nevenfo/kicad-agentic-mcp/crates/konnect/src/ffi.rs

//! C ABI exports for KiCAD plugin integration.
//!
//! KiCAD (or the thin Python launcher) can load this cdylib and call:
//!   kicad_plugin_init(config_path)  — start the embedded MCP server thread
//!   kicad_plugin_version()          — return the version string
//!   kicad_plugin_shutdown()         — stop the server cleanly
//!
//! The MCP server runs in a background tokio thread; the calling process
//! communicates with it via the configured transport (STDIO or HTTP/SSE).

use std::ffi::{c_char, c_int, CStr, CString};
use std::sync::OnceLock;

static RUNTIME: OnceLock<tokio::runtime::Runtime> = OnceLock::new();
static VERSION_CSTR: OnceLock<CString> = OnceLock::new();

/// Initialize and start the embedded MCP server.
///
/// # Safety
/// `config_path` must be a valid null-terminated UTF-8 C string, or NULL to use defaults.
#[no_mangle]
pub unsafe extern "C" fn kicad_plugin_init(config_path: *const c_char) -> c_int {
    let config_path_str = if config_path.is_null() {
        None
    } else {
        match CStr::from_ptr(config_path).to_str() {
            Ok(s) => Some(s.to_owned()),
            Err(_) => return -1,
        }
    };

    let rt = match tokio::runtime::Runtime::new() {
        Ok(rt) => rt,
        Err(_) => return -1,
    };

    rt.spawn(async move {
        use crate::config::{Config, TransportMode};
        use konnect_core::mcp::handler::McpHandler;

        let mut config = match config_path_str.as_deref() {
            Some(p) => Config::load_from(std::path::Path::new(p)).unwrap_or_default(),
            None => Config::load().unwrap_or_default(),
        };
        // `load_from` does not apply the env fallbacks `load` does, and this
        // is the path KiCAD's own plugin loader takes (D.8). Without this,
        // `KONNECT_MODE=read-only` is silently ignored here and the plugin
        // starts writable — a guarantee that holds only on the binary's path
        // is the bug it is meant to prevent. Idempotent on the `load` branch:
        // every fallback either fills a blank or re-parses to the same value.
        // An unrecognised mode stops the server from starting at all, the
        // same shape as an invalid provider below: refusing to run is the
        // only safe reading of "I asked for read-only".
        if let Err(error) = config.apply_env_fallbacks() {
            tracing::error!("invalid server configuration: {error}");
            return;
        }
        let server_config = konnect_core::tools::ServerConfig {
            kicad_cli: config.kicad_cli.clone(),
            kicad_binary: config.kicad_binary.clone(),
            ipc_address: config.ipc_address.clone(),
            project_dir: config.project_dir.clone(),
            jlcpcb_db_path: config.jlcpcb_db_path.clone(),
            auto_load_toolsets: config.auto_load_toolsets,
            mode: config.mode,
        };
        let provider = match config.local_provider() {
            Ok(provider) => provider,
            Err(error) => {
                tracing::error!("invalid local Agent provider configuration: {error}");
                return;
            }
        };
        match McpHandler::new_with_agent_provider(server_config, provider).await {
            Ok(handler) => match config.transport {
                TransportMode::Stdio => {
                    let _ = crate::transport::stdio::run_stdio(handler).await;
                }
                TransportMode::Http => {
                    let _ = crate::transport::http::run_http(handler, &config.http_address).await;
                }
                TransportMode::Both => {
                    let handler_http = handler.clone();
                    let http_addr = config.http_address.clone();
                    tokio::select! {
                        _ = crate::transport::http::run_http(handler_http, &http_addr) => {},
                        _ = crate::transport::stdio::run_stdio(handler) => {},
                    }
                }
            },
            Err(e) => {
                eprintln!("kicad_plugin_init: failed to create handler: {}", e);
            }
        }
    });

    RUNTIME.set(rt).is_ok() as c_int
}

/// Return the plugin version string.
///
/// # Safety
/// The returned pointer is valid for the lifetime of the process.
#[no_mangle]
pub unsafe extern "C" fn kicad_plugin_version() -> *const c_char {
    VERSION_CSTR
        .get_or_init(|| CString::new(env!("CARGO_PKG_VERSION")).expect("version string is valid"))
        .as_ptr()
}

/// Shut down the embedded MCP server.
#[no_mangle]
pub extern "C" fn kicad_plugin_shutdown() {
    // The runtime will be dropped here; tokio tasks are cancelled automatically.
    // In a more complete implementation we would signal the server to flush and close.
    let _ = RUNTIME.get();
}
