nevenfo/kicad-agentic-mcp/crates/konnect-core/src/tools/library.rs

//! `library` toolset — create and manage footprints, symbols, and KiCAD library tables.
//!
//! Operations are file-based (S-expression manipulation + directory scanning).
//! No IPC or kicad-cli is required for most tools.

use crate::mcp::error::ToolErrorKind;
use crate::mcp::protocol::CallToolResult;
use crate::tool;
use crate::tools::{get_path, require_array, require_str, ToolContext, ToolDef};
use crate::try_arg;
use konnect_sexp::parser::{parse_sexp, SexpNode};
use konnect_sexp::writer::{find_balanced_block, find_block_starts, write_atomic};
use serde_json::json;
use std::path::{Path, PathBuf};

// ─── Tool definitions ─────────────────────────────────────────────────────────

/// The pin-item object schema (number/name/type/style/x/y/angle/length) shared
/// by `pins`, `units[].pins`, and `power_pins` in the create_symbol schema
/// below. `require_xy` is false where a `glyph` may auto-place the pins (so x/y
/// become optional) and true for the always-rectangular `power_pins`.
///
/// This object is emitted three times in one schema, so every word in it costs
/// three times as much catalogue budget as it looks like it does. The `type` and
/// `style` enums are self-documenting and carry no `description`; the one fact
/// they cannot express (NC is spelled `no_connect`) lives once in the tool
/// description instead of three times here. Measured: 219 -> 118 tokens per
/// copy, no field, value or default removed.
fn pin_item_schema(require_xy: bool) -> serde_json::Value {
    let mut required = vec!["number", "name", "type"];
    if require_xy {
        required.push("x");
        required.push("y");
    }
    json!({
        "type": "object",
        "properties": {
            "number": { "type": "string" },
            "name": { "type": "string" },
            "type": {
                "type": "string",
                "enum": ["input", "output", "bidirectional", "tri_state", "passive", "free", "unspecified", "power_in", "power_out", "open_collector", "open_emitter", "no_connect"]
            },
            "style": {
                "type": "string",
                "default": "line",
                "enum": ["line", "inverted", "clock", "inverted_clock", "input_low", "clock_low", "output_low", "edge_clock_high", "non_logic"]
            },
            "x": { "type": "number" },
            "y": { "type": "number" },
            "angle": { "type": "number", "default": 0 },
            "length": { "type": "number", "default": 2.54 }
        },
        "required": required
    })
}

pub fn tools() -> Vec<ToolDef> {
    vec![
        super::footprint_graphics::tool(),
        tool!(
            "create_footprint",
            "Create a new footprint (.kicad_mod) file from a pad layout description.",
            json!({
                "type": "object",
                "properties": {
                    "output": { "type": "string", "description": "Output .kicad_mod file path" },
                    "name": { "type": "string", "description": "Footprint name" },
                    "description": { "type": "string", "description": "Footprint description (optional)" },
                    "pads": {
                        "type": "array",
                        "description": "Pad definitions. Sizes in mm.",
                        "items": {
                            "type": "object",
                            "properties": {
                                "number": { "type": "string" },
                                "type": { "type": "string", "enum": ["smd", "thru_hole", "np_thru_hole", "connect"] },
                                "shape": { "type": "string", "enum": ["rect", "oval", "circle", "roundrect", "trapezoid", "custom"] },
                                "x": { "type": "number" },
                                "y": { "type": "number" },
                                "width": { "type": "number" },
                                "height": { "type": "number" },
                                "drill": { "type": "number", "description": "Drill diameter, thru-hole pads only" }
                            },
                            "required": ["number", "type", "shape", "x", "y", "width", "height"]
                        }
                    },
                    "body_width": { "type": "number", "description": "Component body width in mm. The courtyard, silkscreen and fab outlines are all derived from the body and pad envelopes together. Defaults to the pad envelope." },
                    "body_height": { "type": "number", "description": "Component body height in mm." },
                    "pin1_marker": { "type": "boolean", "default": true, "description": "Draw the pin-1 marker (silk dot + fab chamfer). Set false for a non-polarised part such as a fuse or a film capacitor, which has no pin 1 to point at." },
                    "package_type": {
                        "type": "string",
                        "enum": ["smd", "through_hole", "small", "bga"],
                        "description": "Courtyard clearance preset used when `courtyard_clearance` is absent: smd 0.25mm, through_hole 0.5mm, small 0.15mm (below 0603), bga 1.0mm."
                    },
                    "courtyard_clearance": { "type": "number", "description": "Courtyard clearance in mm; overrides `package_type`." },
                    "model": {
                        "type": "object",
                        "description": "3D model to attach.",
                        "properties": {
                            "path": { "type": "string", "description": "Path to a .step/.wrl file, absolute or KiCAD env-var form (${KICAD9_3DMODEL_DIR}/...)" },
                            "offset": { "type": "object", "description": "{x,y,z} mm, default 0,0,0" },
                            "scale": { "type": "object", "description": "{x,y,z}, default 1,1,1" },
                            "rotate": { "type": "object", "description": "{x,y,z} degrees, default 0,0,0" }
                        },
                        "required": ["path"]
                    }
                },
                "required": ["output", "name", "pads"]
            }),
            |args, ctx| async move { handle_create_footprint(args, ctx).await }
        ),
        tool!(
            "edit_footprint_pad",
            "Edit the size, shape, or position of a pad in an existing .kicad_mod footprint file.",
            json!({
                "type": "object",
                "properties": {
                    "footprint_path": { "type": "string", "description": "Path to .kicad_mod file" },
                    "pad_number": { "type": "string", "description": "Pad number to edit" },
                    "x": { "type": "number", "description": "New X position in mm (optional)" },
                    "y": { "type": "number", "description": "New Y position in mm (optional)" },
                    "width": { "type": "number", "description": "New pad width in mm (optional)" },
                    "height": { "type": "number", "description": "New pad height in mm (optional)" },
                    "shape": { "type": "string", "description": "New pad shape (optional)" },
                    "drill": { "type": "number", "description": "New drill diameter in mm (optional)" }
                },
                "required": ["footprint_path", "pad_number"]
            }),
            |args, ctx| async move { handle_edit_footprint_pad(args, ctx).await }
        ),
        tool!(
            "register_footprint_library",
            "Register a local footprint library directory in the KiCAD global or project library table.",
            json!({
                "type": "object",
                "properties": {
                    "library_path": { "type": "string", "description": "Path to .pretty directory" },
                    "nickname": { "type": "string", "description": "Library nickname" },
                    "scope": {
                        "type": "string",
                        "description": "Scope: 'global' or 'project'",
                        "default": "project"
                    },
                    "project": { "type": "string", "description": "Path to .kicad_pro file (required for project scope)" },
                    "replace_existing": {
                        "type": "boolean",
                        "description": "If the nickname is already registered with a different URI, correct that entry's URI in place, keeping its options and descr. Without it such a call is refused and nothing is written.",
                        "default": false
                    }
                },
                "required": ["library_path", "nickname"]
            }),
            |args, ctx| async move { handle_register_footprint_library(args, ctx).await }
        ),
        tool!(
            "list_footprint_libraries",
            "List all registered footprint libraries (global and optionally project-level).",
            json!({
                "type": "object",
                "properties": {
                    "project": { "type": "string", "description": "Path to .kicad_pro to include project libraries (optional)" },
                    "scope": {
                        "type": "string",
                        "description": "Scope: 'global', 'project', or 'all'",
                        "default": "all"
                    }
                },
                "required": []
            }),
            |args, ctx| async move { handle_list_footprint_libraries(args, ctx).await }
        ),
        tool!(
            "create_symbol",
            "Create a KiCAD schematic symbol and append it to a .kicad_sym library file. \
             Single-unit part: use `pins`. Multi-unit part (dual/quad op-amp, gate bank, \
             multi-bank connector): use `units`, plus `power_pins` for the rails they share. \
             A unit's body is a rectangle sized to its pins unless a `glyph` is set, in which \
             case the pins auto-place by `type` (inputs left, in the order listed, top-to- \
             bottom; output right; power top/bottom) and their x/y are ignored. NC pins take \
             type 'no_connect', not 'not_connected'.",
            json!({
                "type": "object",
                "properties": {
                    "library_path": { "type": "string", "description": "Path to .kicad_sym library file" },
                    "name": { "type": "string", "description": "Symbol name" },
                    "reference_prefix": { "type": "string", "description": "Default reference prefix (e.g. 'U')" },
                    "value": { "type": "string", "description": "Default value string" },
                    "glyph": {
                        "type": "string",
                        "default": "rectangle",
                        "enum": ["rectangle", "opamp", "buffer", "inverter", "schmitt", "schmitt_inverter", "and", "nand", "or", "nor", "xor", "xnor"],
                        "description": "Default body shape. 'rectangle' honours the pin x/y you supply; every other value draws a fixed conventional shape and auto-places the pins. Inverting glyphs (inverter/schmitt_inverter/nand/nor/xnor) draw their base body plus an inversion bubble on the output. A glyph whose pins do not fit it (wrong input count, not exactly one output) falls back to a rectangle and reports a warning."
                    },
                    "pins": {
                        "type": "array",
                        "description": "Pins of a single-unit symbol.",
                        "items": pin_item_schema(false)
                    },
                    "show_pin_names": { "type": "boolean", "description": "Show pin names (default true).", "default": true },
                    "show_pin_numbers": { "type": "boolean", "description": "Show pin numbers (default true).", "default": true },
                    "units": {
                        "type": "array",
                        "description": "One element per unit (Unit A, B, C...), each with its own pins and body. Replaces `pins`.",
                        "items": {
                            "type": "object",
                            "properties": {
                                "glyph": {
                                    "type": "string",
                                    "enum": ["rectangle", "opamp", "buffer", "inverter", "schmitt", "schmitt_inverter", "and", "nand", "or", "nor", "xor", "xnor"],
                                    "description": "Overrides the symbol-level `glyph` for this unit."
                                },
                                "pins": { "type": "array", "items": pin_item_schema(false) }
                            },
                            "required": ["pins"]
                        }
                    },
                    "power_pins": {
                        "type": "array",
                        "description": "Rails shared by every unit (V+/V-, VCC/GND). Only meaningful with `units`: they become one final rectangular power unit, following KiCAD's 74xx convention, instead of being drawn on every unit where each copy would need its own wiring to pass ERC.",
                        "items": pin_item_schema(true)
                    }
                },
                "required": ["library_path", "name", "reference_prefix"]
            }),
            |args, ctx| async move { handle_create_symbol(args, ctx).await }
        ),
        tool!(
            "delete_symbol",
            "Delete a symbol definition from a .kicad_sym library file.",
            json!({
                "type": "object",
                "properties": {
                    "library_path": { "type": "string", "description": "Path to .kicad_sym library file" },
                    "symbol_name": { "type": "string", "description": "Name of the symbol to delete" }
                },
                "required": ["library_path", "symbol_name"]
            }),
            |args, ctx| async move { handle_delete_symbol(args, ctx).await }
        ),
        tool!(
            "list_symbols_in_library",
            "List all symbol names defined in a .kicad_sym library file.",
            json!({
                "type": "object",
                "properties": {
                    "library_path": { "type": "string", "description": "Path to .kicad_sym library file" },
                    "limit": { "type": "integer", "description": "Maximum number of symbols to return", "default": 100 }
                },
                "required": ["library_path"]
            }),
            |args, ctx| async move { handle_list_symbols_in_library(args, ctx).await }
        ),
        tool!(
            "register_symbol_library",
            "Register a .kicad_sym library file in the KiCAD global or project symbol table.",
            json!({
                "type": "object",
                "properties": {
                    "library_path": { "type": "string", "description": "Path to .kicad_sym file" },
                    "nickname": { "type": "string", "description": "Library nickname" },
                    "scope": {
                        "type": "string",
                        "description": "Scope: 'global' or 'project'",
                        "default": "project"
                    },
                    "project": { "type": "string", "description": "Path to .kicad_pro file (required for project scope)" },
                    "replace_existing": {
                        "type": "boolean",
                        "description": "If the nickname is already registered with a different URI, correct that entry's URI in place, keeping its options and descr. Without it such a call is refused and nothing is written.",
                        "default": false
                    }
                },
                "required": ["library_path", "nickname"]
            }),
            |args, ctx| async move { handle_register_symbol_library(args, ctx).await }
        ),
        tool!(
            "list_symbol_libraries",
            "List all registered symbol libraries (global and optionally project-level).",
            json!({
                "type": "object",
                "properties": {
                    "project": { "type": "string", "description": "Path to .kicad_pro to include project libraries (optional)" },
                    "scope": {
                        "type": "string",
                        "description": "Scope: 'global', 'project', or 'all'",
                        "default": "all"
                    }
                },
                "required": []
            }),
            |args, ctx| async move { handle_list_symbol_libraries(args, ctx).await }
        ),
        tool!(
            "search_symbols",
            "Search for symbols across all registered libraries by name or keyword.",
            json!({
                "type": "object",
                "properties": {
                    "query": { "type": "string", "description": "Search string (partial name or keyword match)" },
                    "limit": { "type": "integer", "description": "Maximum number of results to return", "default": 50 },
                    "project_dir": { "type": "string", "description": "Project directory whose sym-lib-table is also searched. Defaults to the configured project_dir." }
                },
                "required": ["query"]
            }),
            |args, ctx| async move { handle_search_symbols(args, ctx).await }
        ),
        tool!(
            "list_library_footprints",
            "List all footprints in a specific registered footprint library (.pretty directory).",
            json!({
                "type": "object",
                "properties": {
                    "library_path": { "type": "string", "description": "Path to .pretty directory (or nickname to look up)" }
                },
                "required": ["library_path"]
            }),
            |args, ctx| async move { handle_list_library_footprints(args, ctx).await }
        ),
        tool!(
            "get_footprint_info",
            "Return detailed information about a footprint: pad layout, courtyard, description,              and its line/arc/rect/circle/poly graphics in the exact shape `set_footprint_graphics`              takes back.",
            json!({
                "type": "object",
                "properties": {
                    "footprint_path": { "type": "string", "description": "Path to .kicad_mod file, OR 'Library:Footprint' identifier" },
                    "graphics_layer": { "type": "string", "description": "Report only graphics on this canonical layer, such as F.CrtYd. Omit for all layers." }
                },
                "required": ["footprint_path"]
            }),
            |args, ctx| async move { handle_get_footprint_info(args, ctx).await }
        ),
        tool!(
            "search_footprints",
            "Search for footprints across all registered libraries by name or keyword.",
            json!({
                "type": "object",
                "properties": {
                    "query": { "type": "string", "description": "Search string (partial name or keyword)" },
                    "limit": { "type": "integer", "description": "Maximum number of results to return", "default": 50 }
                },
                "required": ["query"]
            }),
            |args, ctx| async move { handle_search_footprints(args, ctx).await }
        ),
        tool!(
            "get_symbol_info",
            "Return detailed information about a schematic symbol: pins, properties, description.",
            json!({
                "type": "object",
                "properties": {
                    "lib_id": { "type": "string", "description": "Library:Symbol identifier (e.g. 'Device:R')" },
                    "project_dir": { "type": "string", "description": "Project directory to resolve project-scoped libraries. Defaults to the configured project_dir." }
                },
                "required": ["lib_id"]
            }),
            |args, ctx| async move { handle_get_symbol_info(args, ctx).await }
        ),
    ]
}

// ─── Handlers ─────────────────────────────────────────────────────────────────

// ─── Footprint / symbol geometry (pure, unit-tested) ──────────────────────────

/// Minimal pad geometry needed to derive outlines, courtyards, and pin 1.
#[derive(Debug, Clone)]
struct PadGeom {
    number: String,
    pad_type: String,
    x: f64,
    y: f64,
    w: f64,
    h: f64,
}

/// Axis-aligned bounding box `(min_x, min_y, max_x, max_y)` over pad extents.
fn pads_bbox(pads: &[PadGeom]) -> (f64, f64, f64, f64) {
    let mut min_x = f64::INFINITY;
    let mut min_y = f64::INFINITY;
    let mut max_x = f64::NEG_INFINITY;
    let mut max_y = f64::NEG_INFINITY;
    for p in pads {
        min_x = min_x.min(p.x - p.w / 2.0);
        min_y = min_y.min(p.y - p.h / 2.0);
        max_x = max_x.max(p.x + p.w / 2.0);
        max_y = max_y.max(p.y + p.h / 2.0);
    }
    (min_x, min_y, max_x, max_y)
}

/// The body's own axis-aligned box, centred on the pad envelope — `None` when
/// the caller did not describe a body.
///
/// Centring on the pads rather than on the origin is what the fab outline
/// already did; keeping one definition means the courtyard and the fab outline
/// can never disagree about where the body is.
fn body_bbox(pads: &[PadGeom], body: Option<(f64, f64)>) -> Option<(f64, f64, f64, f64)> {
    let (bw, bh) = body?;
    let (pmin_x, pmin_y, pmax_x, pmax_y) = pads_bbox(pads);
    let cx = (pmin_x + pmax_x) / 2.0;
    let cy = (pmin_y + pmax_y) / 2.0;
    Some((cx - bw / 2.0, cy - bh / 2.0, cx + bw / 2.0, cy + bh / 2.0))
}

/// The union of two boxes.
fn union_bbox(a: (f64, f64, f64, f64), b: (f64, f64, f64, f64)) -> (f64, f64, f64, f64) {
    (a.0.min(b.0), a.1.min(b.1), a.2.max(b.2), a.3.max(b.3))
}

/// KLC's courtyard grid, as steps per millimetre: `KLC_CRTYD_GRID = 0.01` mm,
/// from `pcb/rules/klc_constants.py` in KiCad's own `kicad-library-utils`.
///
/// Held as the reciprocal because that is what makes the arithmetic exact.
/// `(-3.8 / 0.01).floor() * 0.01` is -3.8000000000000003 — one ULP out, and a
/// value that was already on the grid comes back off it. `-380.0 / 100.0` is
/// -3.8 exactly.
const COURTYARD_GRID_STEPS_PER_MM: f64 = 100.0;

/// Snap a courtyard box to the KLC grid, always **outward**.
///
/// KiCad's own checker snaps to nearest (`mapToGrid` in `pcb/rules/F5_3.py`).
/// Rounding outward instead is the one deliberate difference: rounding a bound
/// inward would take back up to half a grid step of the clearance that was just
/// added, and a courtyard 5 µm too small is the failure this whole change exists
/// to stop. Growing by at most 5 µm costs nothing.
fn snap_courtyard_outward(bbox: (f64, f64, f64, f64)) -> (f64, f64, f64, f64) {
    // The epsilon absorbs binary-float noise, so a bound that is already on the
    // grid is not pushed a whole step out by a representation error.
    let epsilon = 1e-9;
    let down =
        |v: f64| (v * COURTYARD_GRID_STEPS_PER_MM + epsilon).floor() / COURTYARD_GRID_STEPS_PER_MM;
    let up =
        |v: f64| (v * COURTYARD_GRID_STEPS_PER_MM - epsilon).ceil() / COURTYARD_GRID_STEPS_PER_MM;
    (down(bbox.0), down(bbox.1), up(bbox.2), up(bbox.3))
}

/// The courtyard box: the combined pad and body envelope, grown by `clearance`
/// and snapped outward to the KLC grid.
///
/// # The defect this replaces
///
/// The courtyard used to be the *pad* envelope plus clearance, with the body
/// used only for the fab outline. Every part whose body overruns its land
/// pattern therefore got a courtyard smaller than the part — and a courtyard
/// smaller than the part is worse than none, because DRC then reports clearance
/// as satisfied while the physical bodies collide. Found on a real board: a
/// 5 mm-pitch film capacitor, body 3.5 mm deep, pads 1.6 mm, courtyard 2.6 mm.
///
/// # The rule
///
/// KLC F5.3 defines the courtyard as the smallest rectangle giving the required
/// clearance around the **combined component body and land pattern**. KiCad's
/// own conformance checker implements exactly that: `getFootprintBounds()` in
/// `pcb/rules/F5_3.py` adds the pad bounds to the geometric bounds of F.Fab
/// (falling back to B.Fab, then the silkscreen), then `defaultCourtyard()`
/// expands by the offset and snaps to `KLC_CRTYD_GRID`.
fn courtyard_bbox(
    pads: &[PadGeom],
    body: Option<(f64, f64)>,
    clearance: f64,
) -> (f64, f64, f64, f64) {
    let envelope = match body_bbox(pads, body) {
        Some(body) => union_bbox(pads_bbox(pads), body),
        None => pads_bbox(pads),
    };
    snap_courtyard_outward((
        envelope.0 - clearance,
        envelope.1 - clearance,
        envelope.2 + clearance,
        envelope.3 + clearance,
    ))
}

/// Courtyard clearance per the contributor's rule: an explicit value wins, else
/// `package_type`, else auto-detect (through-hole 0.5 mm, sub-0603 body 0.15 mm,
/// otherwise SMT 0.25 mm). BGA (1.0 mm) is opt-in via `package_type` because an
/// area array can't be reliably auto-detected from pads alone.
fn courtyard_clearance(
    explicit: Option<f64>,
    package_type: Option<&str>,
    pads: &[PadGeom],
    body: Option<(f64, f64)>,
) -> f64 {
    if let Some(c) = explicit {
        return c;
    }
    match package_type {
        Some("bga") => return 1.0,
        Some("small") => return 0.15,
        Some("through_hole") | Some("th") => return 0.5,
        Some("smd") => return 0.25,
        _ => {}
    }
    if pads.iter().any(|p| p.pad_type.contains("thru")) {
        return 0.5;
    }
    if let Some((bw, bh)) = body {
        // 0603 imperial body is 1.6 x 0.8 mm; anything shorter is "smaller".
        if bw.max(bh) < 1.6 {
            return 0.15;
        }
    }
    0.25
}

/// Index of pin 1: the pad numbered "1", else the first pad. `None` if no pads.
fn pin1_index(pads: &[PadGeom]) -> Option<usize> {
    if pads.is_empty() {
        return None;
    }
    Some(pads.iter().position(|p| p.number == "1").unwrap_or(0))
}

/// The rectangle corner (of the four) nearest point `(px, py)`.
fn nearest_corner(min_x: f64, min_y: f64, max_x: f64, max_y: f64, px: f64, py: f64) -> (f64, f64) {
    let cx = if (px - min_x).abs() <= (max_x - px).abs() {
        min_x
    } else {
        max_x
    };
    let cy = if (py - min_y).abs() <= (max_y - py).abs() {
        min_y
    } else {
        max_y
    };
    (cx, cy)
}

/// Radius of the pin-1 silk dot, in mm.
const PIN1_DOT_RADIUS_MM: f64 = 0.15;

/// Where the pin-1 dot's centre goes along one axis: just outside the silk
/// outline, but never so far that any part of the dot leaves the courtyard.
///
/// `sign` is the outward direction, -1 for a min edge and +1 for a max edge.
///
/// The unclamped version put a dot at x = -9.3 on a footprint whose courtyard
/// stopped at -9.0. Drawing a footprint's own marker outside its own courtyard
/// is a contradiction: the courtyard is the claim about how much room the part
/// needs, and a mark beyond it says the claim is short. Clamping to
/// `courtyard_edge - sign * radius` puts the dot flush against the inside of
/// the courtyard in the worst case, which is still unmistakably beside pin 1.
fn pin1_dot_center(silk_edge: f64, courtyard_edge: f64, sign: f64) -> f64 {
    let desired = silk_edge + sign * 0.4;
    let limit = courtyard_edge - sign * PIN1_DOT_RADIUS_MM;
    if sign < 0.0 {
        desired.max(limit)
    } else {
        desired.min(limit)
    }
}

fn point_toward(from: (f64, f64), toward: (f64, f64), d: f64) -> (f64, f64) {
    let dx = toward.0 - from.0;
    let dy = toward.1 - from.1;
    let len = (dx * dx + dy * dy).sqrt();
    if len < 1e-9 {
        return from;
    }
    (from.0 + dx / len * d, from.1 + dy / len * d)
}

/// Ordered vertices of a rectangle outline whose corner nearest `(px, py)` is
/// chamfered by `chamfer` mm (clamped to 40% of the shorter side) — the F.Fab
/// pin-1 marker. Clockwise, KiCAD footprint Y-down.
fn chamfered_rect_points(
    min_x: f64,
    min_y: f64,
    max_x: f64,
    max_y: f64,
    px: f64,
    py: f64,
    chamfer: f64,
) -> Vec<(f64, f64)> {
    let ch = chamfer
        .min(0.4 * (max_x - min_x).min(max_y - min_y))
        .max(0.0);
    let corners = [
        (min_x, min_y),
        (max_x, min_y),
        (max_x, max_y),
        (min_x, max_y),
    ];
    let (tcx, tcy) = nearest_corner(min_x, min_y, max_x, max_y, px, py);
    let mut pts = Vec::new();
    for (i, &(cx, cy)) in corners.iter().enumerate() {
        if (cx - tcx).abs() < 1e-9 && (cy - tcy).abs() < 1e-9 && ch > 0.0 {
            let prev = corners[(i + 3) % 4];
            let next = corners[(i + 1) % 4];
            pts.push(point_toward((cx, cy), prev, ch));
            pts.push(point_toward((cx, cy), next, ch));
        } else {
            pts.push((cx, cy));
        }
    }
    pts
}

/// Emit the `(model ...)` block when a `model` object with a non-empty `path`
/// is present. Path is passed through verbatim (absolute or KiCAD env-var).
fn build_model_sexp(args: &serde_json::Value) -> String {
    let model = match args.get("model") {
        Some(m) if m.is_object() => m,
        _ => return String::new(),
    };
    let path = match model["path"].as_str() {
        Some(p) if !p.is_empty() => p,
        _ => return String::new(),
    };
    let xyz = |key: &str, default: f64| -> (f64, f64, f64) {
        let o = &model[key];
        (
            o["x"].as_f64().unwrap_or(default),
            o["y"].as_f64().unwrap_or(default),
            o["z"].as_f64().unwrap_or(default),
        )
    };
    let (ox, oy, oz) = xyz("offset", 0.0);
    let (sx, sy, sz) = xyz("scale", 1.0);
    let (rx, ry, rz) = xyz("rotate", 0.0);
    format!(
        "\n  (model \"{}\"\n    (offset (xyz {} {} {}))\n    (scale (xyz {} {} {}))\n    (rotate (xyz {} {} {}))\n  )",
        path, ox, oy, oz, sx, sy, sz, rx, ry, rz
    )
}

/// Build the courtyard, silkscreen, fab outline, reference/value text, and the
/// pin-1 marker (silk dot + fab chamfer) for a footprint from its pad geometry.
fn build_footprint_graphics(args: &serde_json::Value, name: &str, pads: &[PadGeom]) -> String {
    let (pmin_x, pmin_y, pmax_x, pmax_y) = pads_bbox(pads);

    let body = match (args["body_width"].as_f64(), args["body_height"].as_f64()) {
        (Some(bw), Some(bh)) => Some((bw, bh)),
        _ => None,
    };
    let clearance = courtyard_clearance(
        args["courtyard_clearance"].as_f64(),
        args["package_type"].as_str(),
        pads,
        body,
    );

    // Courtyard: the *combined* pad and body envelope plus clearance, per KLC
    // F5.3 — see `courtyard_bbox` for why the pad envelope alone was wrong.
    let (cmin_x, cmin_y, cmax_x, cmax_y) = courtyard_bbox(pads, body, clearance);

    // Fab: the component body when given, else the pad envelope. May overlap
    // pads — fab is a documentation layer, not subject to silk-over-pad rules.
    let (fmin_x, fmin_y, fmax_x, fmax_y) =
        body_bbox(pads, body).unwrap_or((pmin_x, pmin_y, pmax_x, pmax_y));

    // Silk: outside the same combined envelope, so it clears the pads (no
    // silk-over-pad violation) *and* actually outlines the part. Deriving it
    // from the pad envelope alone drew a 1.9 mm box around a 3.5 mm body on the
    // footprint that exposed the courtyard defect — three layers each claiming
    // a different body size.
    let silk_margin = 0.15;
    let (emin_x, emin_y, emax_x, emax_y) = match body_bbox(pads, body) {
        Some(body) => union_bbox((pmin_x, pmin_y, pmax_x, pmax_y), body),
        None => (pmin_x, pmin_y, pmax_x, pmax_y),
    };
    let (smin_x, smin_y, smax_x, smax_y) = (
        emin_x - silk_margin,
        emin_y - silk_margin,
        emax_x + silk_margin,
        emax_y + silk_margin,
    );

    let mut s = String::new();

    // Courtyard rectangle (F.CrtYd) — required for DRC.
    s.push_str(&format!(
        "\n  (fp_rect (start {:.4} {:.4}) (end {:.4} {:.4}) (stroke (width 0.05) (type solid)) (fill none) (layer \"F.CrtYd\"))",
        cmin_x, cmin_y, cmax_x, cmax_y
    ));
    // Silkscreen outline (F.SilkS).
    s.push_str(&format!(
        "\n  (fp_rect (start {:.4} {:.4}) (end {:.4} {:.4}) (stroke (width 0.12) (type solid)) (fill none) (layer \"F.SilkS\"))",
        smin_x, smin_y, smax_x, smax_y
    ));

    // A pin-1 mark is right for a polarised part and wrong for one that has no
    // pin 1 to find: a fuse, a resistor, a non-polarised capacitor. Nothing in
    // a pad list distinguishes the two — a fuse's pads are numbered "1" and "2"
    // exactly like a diode's — so this is a caller's statement, not a guess.
    // Default true, because the parts that need the mark are the ones where
    // omitting it is a build error.
    let want_pin1 = args["pin1_marker"].as_bool().unwrap_or(true);

    if let Some(i1) = pin1_index(pads).filter(|_| want_pin1) {
        let p1 = &pads[i1];

        // Fab outline with the pin-1 corner chamfered.
        let chamfer = (0.25 * (fmax_x - fmin_x).min(fmax_y - fmin_y)).clamp(0.3, 1.0);
        let pts = chamfered_rect_points(fmin_x, fmin_y, fmax_x, fmax_y, p1.x, p1.y, chamfer);
        let pts_str: String = pts
            .iter()
            .map(|(x, y)| format!("(xy {:.4} {:.4}) ", x, y))
            .collect();
        s.push_str(&format!(
            "\n  (fp_poly (pts {}) (stroke (width 0.1) (type solid)) (fill none) (layer \"F.Fab\"))",
            pts_str.trim()
        ));

        // Silk pin-1 dot just outside the silk outline, aligned with pin 1's
        // pad — NOT at the footprint corner, where a dot is ambiguous between
        // pin 1 and the last pin that shares the same corner. It sits directly
        // beside pin 1 so the mark is unmistakable.
        let bcx = (pmin_x + pmax_x) / 2.0;
        let bcy = (pmin_y + pmax_y) / 2.0;
        let (dx, dy) = if (p1.x - bcx).abs() >= (p1.y - bcy).abs() {
            // Pin 1 is on a left/right edge: dot outside that edge, at pin 1's y.
            let sign = if p1.x < bcx { -1.0 } else { 1.0 };
            let silk_edge = if sign < 0.0 { smin_x } else { smax_x };
            let courtyard_edge = if sign < 0.0 { cmin_x } else { cmax_x };
            (pin1_dot_center(silk_edge, courtyard_edge, sign), p1.y)
        } else {
            // Pin 1 is on a top/bottom edge: dot outside that edge, at pin 1's x.
            let sign = if p1.y < bcy { -1.0 } else { 1.0 };
            let silk_edge = if sign < 0.0 { smin_y } else { smax_y };
            let courtyard_edge = if sign < 0.0 { cmin_y } else { cmax_y };
            (p1.x, pin1_dot_center(silk_edge, courtyard_edge, sign))
        };
        s.push_str(&format!(
            "\n  (fp_circle (center {:.4} {:.4}) (end {:.4} {:.4}) (stroke (width 0.1) (type solid)) (fill solid) (layer \"F.SilkS\"))",
            dx, dy, dx + PIN1_DOT_RADIUS_MM, dy
        ));
    } else {
        // No pads to mark pin 1 against — plain fab rectangle.
        s.push_str(&format!(
            "\n  (fp_rect (start {:.4} {:.4}) (end {:.4} {:.4}) (stroke (width 0.1) (type solid)) (fill none) (layer \"F.Fab\"))",
            fmin_x, fmin_y, fmax_x, fmax_y
        ));
    }

    // Reference (F.SilkS, above) and value (F.Fab, below).
    let cx = (pmin_x + pmax_x) / 2.0;
    s.push_str(&format!(
        "\n  (fp_text reference \"REF**\" (at {:.4} {:.4} 0) (layer \"F.SilkS\") (effects (font (size 1 1) (thickness 0.15))))",
        cx, cmin_y - 1.0
    ));
    s.push_str(&format!(
        "\n  (fp_text value \"{}\" (at {:.4} {:.4} 0) (layer \"F.Fab\") (effects (font (size 1 1) (thickness 0.15))))",
        name, cx, cmax_y + 1.0
    ));

    s
}

async fn handle_create_footprint(
    args: &serde_json::Value,
    _ctx: &ToolContext,
) -> anyhow::Result<CallToolResult> {
    let output = get_path(args, "output")?;
    let name = try_arg!(require_str(args, "name"));
    let description = args["description"].as_str().unwrap_or("");

    // `name` and `pads` are `required` in the schema. Defaulting them wrote a
    // footprint called "Footprint" with no pads over whatever `output` already
    // held — a destructive write standing in for the call the caller meant.
    let pads_val = try_arg!(require_array(args, "pads"));
    let mut pad_geoms: Vec<PadGeom> = Vec::new();
    let mut pad_sexp = String::new();
    for pad in pads_val {
        let number = pad["number"].as_str().unwrap_or("1").to_string();
        let pad_type = pad["type"].as_str().unwrap_or("smd").to_string();
        let shape = pad["shape"].as_str().unwrap_or("rect");
        let x = pad["x"].as_f64().unwrap_or(0.0);
        let y = pad["y"].as_f64().unwrap_or(0.0);
        let w = pad["width"].as_f64().unwrap_or(1.0);
        let h = pad["height"].as_f64().unwrap_or(1.0);

        let layers = if pad_type == "smd" {
            r#"(layers "F.Cu" "F.Paste" "F.Mask")"#
        } else {
            r#"(layers "*.Cu" "*.Mask")"#
        };

        let drill_sexp = if let Some(drill) = pad["drill"].as_f64() {
            format!("(drill {})", drill)
        } else {
            String::new()
        };

        pad_sexp.push_str(&format!(
            "\n  (pad \"{}\" {} {} (at {} {}) (size {} {}) {} {})",
            number, pad_type, shape, x, y, w, h, layers, drill_sexp
        ));
        pad_geoms.push(PadGeom {
            number,
            pad_type,
            x,
            y,
            w,
            h,
        });
    }

    // Courtyard, silk, fab, text, and pin-1 marker, derived from pad geometry.
    let graphics = if pad_geoms.is_empty() {
        String::new()
    } else {
        build_footprint_graphics(args, name, &pad_geoms)
    };
    let model_sexp = build_model_sexp(args);

    let attr = if pad_geoms.iter().any(|p| p.pad_type == "smd") {
        "smd"
    } else {
        "through_hole"
    };

    let content = format!(
        "(footprint \"{}\"\n  (version 20240108)\n  (generator \"konnect\")\n  (layer \"F.Cu\")\n  (descr \"{}\")\n  (attr {}){}{}{}\n)",
        name, description, attr, pad_sexp, graphics, model_sexp
    );

    // Ensure parent directory exists
    if let Some(parent) = output.parent() {
        tokio::fs::create_dir_all(parent).await?;
    }
    write_atomic(&output, &content)?;

    Ok(CallToolResult::text(
        serde_json::to_string(&json!({
            "success": true,
            "footprint": name,
            "output": output.to_str().unwrap_or(""),
            "pad_count": pad_geoms.len(),
            "courtyard": !pad_geoms.is_empty(),
            "pin1_marked": !pad_geoms.is_empty() && args["pin1_marker"].as_bool().unwrap_or(true),
            "model": args.get("model").and_then(|m| m["path"].as_str()).unwrap_or("")
        }))
        .unwrap(),
    ))
}

async fn handle_edit_footprint_pad(
    args: &serde_json::Value,
    _ctx: &ToolContext,
) -> anyhow::Result<CallToolResult> {
    let path = get_path(args, "footprint_path")?;
    let pad_number = try_arg!(require_str(args, "pad_number"));

    let content = tokio::fs::read_to_string(&path).await?;

    // Find the pad block:  (pad "N" ... (at X Y) (size W H) ...)
    // We search for the at/size/drill atoms and replace them individually.
    let pad_pat = format!(r#"(pad "{}""#, pad_number);
    let pad_start = content
        .find(&pad_pat)
        .ok_or_else(|| anyhow::anyhow!("Pad '{}' not found in footprint", pad_number))?;

    // Find the closing paren of this pad block (simple depth count)
    let pad_end = {
        let mut depth = 0i32;
        let mut end = pad_start;
        for (i, ch) in content[pad_start..].char_indices() {
            match ch {
                '(' => depth += 1,
                ')' => {
                    depth -= 1;
                    if depth == 0 {
                        end = pad_start + i + 1;
                        break;
                    }
                }
                _ => {}
            }
        }
        end
    };
    let pad_block = &content[pad_start..pad_end];

    // Helper: replace or add a sub-expression within the pad block
    let mut new_pad = pad_block.to_string();

    if let Some(x) = args["x"].as_f64() {
        // Replace (at OLD_X OLD_Y [ROT]) → update X
        if let Some(at_pos) = new_pad.find("(at ") {
            let at_end = new_pad[at_pos..]
                .find(')')
                .map(|i| at_pos + i + 1)
                .unwrap_or(new_pad.len());
            let at_block = &new_pad[at_pos..at_end];
            // Parse existing values
            let parts: Vec<&str> = at_block
                .trim_start_matches("(at ")
                .trim_end_matches(')')
                .split_whitespace()
                .collect();
            let old_y = parts
                .get(1)
                .and_then(|s| s.parse::<f64>().ok())
                .unwrap_or(0.0);
            let rot = parts.get(2).map(|s| format!(" {}", s)).unwrap_or_default();
            let new_at = format!("(at {} {}{})", x, old_y, rot);
            new_pad.replace_range(at_pos..at_end, &new_at);
        }
    }
    if let Some(y) = args["y"].as_f64() {
        if let Some(at_pos) = new_pad.find("(at ") {
            let at_end = new_pad[at_pos..]
                .find(')')
                .map(|i| at_pos + i + 1)
                .unwrap_or(new_pad.len());
            let at_block = &new_pad[at_pos..at_end];
            let parts: Vec<&str> = at_block
                .trim_start_matches("(at ")
                .trim_end_matches(')')
                .split_whitespace()
                .collect();
            let old_x = parts
                .first()
                .and_then(|s| s.parse::<f64>().ok())
                .unwrap_or(0.0);
            let rot = parts.get(2).map(|s| format!(" {}", s)).unwrap_or_default();
            let new_at = format!("(at {} {}{})", old_x, y, rot);
            new_pad.replace_range(at_pos..at_end, &new_at);
        }
    }
    if let (Some(w), Some(h)) = (args["width"].as_f64(), args["height"].as_f64()) {
        if let Some(sz_pos) = new_pad.find("(size ") {
            let sz_end = new_pad[sz_pos..]
                .find(')')
                .map(|i| sz_pos + i + 1)
                .unwrap_or(new_pad.len());
            let new_size = format!("(size {} {})", w, h);
            new_pad.replace_range(sz_pos..sz_end, &new_size);
        }
    }
    if let Some(drill) = args["drill"].as_f64() {
        if let Some(dr_pos) = new_pad.find("(drill ") {
            let dr_end = new_pad[dr_pos..]
                .find(')')
                .map(|i| dr_pos + i + 1)
                .unwrap_or(new_pad.len());
            let new_drill = format!("(drill {})", drill);
            new_pad.replace_range(dr_pos..dr_end, &new_drill);
        } else {
            // Insert drill before closing paren of pad
            let insert_at = new_pad.rfind(')').unwrap_or(new_pad.len());
            new_pad.insert_str(insert_at, &format!(" (drill {})", drill));
        }
    }

    // Apply the pad block replacement
    let new_content = format!(
        "{}{}{}",
        &content[..pad_start],
        new_pad,
        &content[pad_end..]
    );
    write_atomic(&path, &new_content)?;

    Ok(CallToolResult::text(
        serde_json::to_string(&json!({
            "success": true,
            "pad": pad_number
        }))
        .unwrap(),
    ))
}

// ─── Library table helpers ────────────────────────────────────────────────────

/// Returns the path to the global fp-lib-table file.
fn global_fp_lib_table() -> PathBuf {
    super::kicad_config_dir().join("fp-lib-table")
}

/// Returns the path to the global sym-lib-table file.
fn global_sym_lib_table() -> PathBuf {
    super::kicad_config_dir().join("sym-lib-table")
}

/// Parse a lib-table S-expression and return list of (nickname, uri, type) tuples.
///
/// Indentation-agnostic: KiCad's own writers emit tab-indented, CRLF-terminated
/// tables while this crate's writer uses two spaces, so a fixed literal such as
/// `"\n  (lib "` silently matches nothing in a real `fp-lib-table`.
fn parse_lib_table(content: &str) -> Vec<serde_json::Value> {
    let mut libs = Vec::new();
    // Each entry: (lib (name "NICK") (type "...") (uri "...") (options "") (descr "..."))
    for start in find_block_starts(content, "lib") {
        let Some((block_start, block_end)) = find_balanced_block(content, start) else {
            continue;
        };
        let block = &content[block_start..block_end];

        let nickname = extract_sexp_string(block, "name").unwrap_or_default();
        let uri = extract_sexp_string(block, "uri").unwrap_or_default();
        let lib_type = extract_sexp_string(block, "type").unwrap_or_default();
        let descr = extract_sexp_string(block, "descr").unwrap_or_default();

        libs.push(json!({
            "nickname": nickname,
            "uri": uri,
            "type": lib_type,
            "description": descr
        }));
    }
    libs
}

/// Resolve a lib-table URI to a concrete path, expanding a leading
/// `${KICAD*_DIR}` reference.
///
/// KiCad's shipped tables address bundled libraries as
/// `${KICAD10_FOOTPRINT_DIR}/Resistor_SMD.pretty`. An exported environment
/// variable wins; otherwise the variable's kind is inferred from its name and
/// the known install locations are searched.
fn expand_lib_uri(uri: &str, kiprjmod: Option<&Path>) -> Option<PathBuf> {
    let Some(rest) = uri.strip_prefix("${") else {
        return (!uri.is_empty()).then(|| PathBuf::from(uri));
    };
    let close = rest.find('}')?;
    let var = &rest[..close];
    let tail = rest[close + 1..].trim_start_matches(['/', '\\']);

    // ${KIPRJMOD} is the project directory — resolved from the table's own
    // location, not the environment: KiCad sets it per open project at
    // runtime, so an exported value (if any) may belong to a different
    // project than the table being read. Project-scoped registrations are
    // the default for register_footprint_library, so this is the common
    // case for user-registered libraries, not an edge.
    if var == "KIPRJMOD" {
        let p = kiprjmod?.join(tail);
        return p.exists().then_some(p);
    }

    // var_os, not var: `var` treats a non-Unicode value as absent, which would
    // send a perfectly good ${KICAD*_DIR} down the install-root guess path.
    if let Some(base) = std::env::var_os(var) {
        let p = PathBuf::from(base).join(tail);
        if p.exists() {
            return Some(p);
        }
    }

    // e.g. KICAD10_FOOTPRINT_DIR -> "footprints"
    let kind = if var.ends_with("_FOOTPRINT_DIR") {
        "footprints"
    } else if var.ends_with("_SYMBOL_DIR") {
        "symbols"
    } else if var.ends_with("_3DMODEL_DIR") {
        "3dmodels"
    } else {
        return None;
    };

    super::find_kicad_library_dirs(kind)
        .into_iter()
        .map(|base| base.join(tail))
        .find(|p| p.exists())
}

/// Maximum depth when following nested `(type "Table")` lib-table references.
const MAX_LIB_TABLE_DEPTH: usize = 4;

/// Parse a lib-table and return concrete libraries, following nested tables.
///
/// KiCad 10 no longer copies its ~155 bundled libraries into the user's table.
/// The default global table instead holds a single indirection entry —
/// `(lib (name "KiCad") (type "Table") (uri ".../template/fp-lib-table"))` —
/// pointing at the shipped template table. Treating that entry as a library
/// makes every bundled library invisible, so it is followed here.
///
/// Each returned entry carries the original `uri` plus a resolved `path`
/// whenever [`expand_lib_uri`] yields one: a `${KICAD*_DIR}` URI resolves only
/// if the expansion exists on disk, while a plain URI is passed through as
/// written. The target may be a directory (`.pretty`) or a file
/// (`.kicad_sym`), so the presence of `path` is not a promise that the library
/// is readable — only that the URI was understood.
fn flatten_lib_table(
    content: &str,
    depth: usize,
    kiprjmod: Option<&Path>,
) -> Vec<serde_json::Value> {
    let mut out = Vec::new();

    for mut entry in parse_lib_table(content) {
        let uri = entry["uri"].as_str().unwrap_or("").to_string();
        let is_nested = entry["type"].as_str() == Some("Table");

        if is_nested {
            if depth >= MAX_LIB_TABLE_DEPTH {
                tracing::warn!(
                    "lib-table nesting deeper than {} levels at '{}' — not followed",
                    MAX_LIB_TABLE_DEPTH,
                    uri
                );
                continue;
            }
            match expand_lib_uri(&uri, kiprjmod).map(std::fs::read_to_string) {
                Some(Ok(nested)) => out.extend(flatten_lib_table(&nested, depth + 1, kiprjmod)),
                _ => tracing::warn!("nested lib-table '{}' could not be read", uri),
            }
            continue;
        }

        if let Some(path) = expand_lib_uri(&uri, kiprjmod) {
            entry["path"] = json!(path.to_string_lossy());
        }
        out.push(entry);
    }

    out
}

/// Read a lib-table file from disk and flatten it, reporting a table that is
/// present but unreadable.
///
/// An absent table is normal and yields an empty list: a project without its
/// own fp-lib-table simply has none, and every caller checks both the global
/// and project tables. Anything else — a permissions problem, a truncated
/// file — is not normal, and must not be folded into the same empty list. The
/// symptom that produces is a bare `{"count": 0}`, which is precisely what the
/// bug this module fixes looked like, so silence here would make a real
/// failure indistinguishable from a regression.
fn read_lib_table_checked(path: &Path) -> Result<Vec<serde_json::Value>, LibTableUnreadable> {
    match std::fs::read_to_string(path) {
        // ${KIPRJMOD} is the directory the project's lib-table lives in, so
        // the table's own parent IS the correct expansion base for a project
        // table. For the global table the parent is KiCad's config dir, where
        // a ${KIPRJMOD} entry would be authoring error to begin with — the
        // expansion then simply fails its exists() check.
        Ok(content) => Ok(flatten_lib_table(&content, 0, path.parent())),
        Err(e) if e.kind() == std::io::ErrorKind::NotFound => Ok(Vec::new()),
        Err(source) => Err(LibTableUnreadable {
            path: path.to_path_buf(),
            source,
        }),
    }
}

/// A lib-table that exists but could not be read.
///
/// D.6.5: this used to be a `String`, and the `io::Error` inside it — the only
/// thing that distinguishes a permissions problem from a truncated file from a
/// path that is really a directory — was destroyed at the point of formatting.
/// Every handler downstream then had nothing left to classify on, which is why
/// four call sites carried the same "uncatalogued on purpose" comment. The
/// prose is unchanged; only the type survives further now.
#[derive(Debug)]
pub(crate) struct LibTableUnreadable {
    /// The table that could not be read.
    pub path: PathBuf,
    /// Why. Kept as the original error, never as its message.
    pub source: std::io::Error,
}

impl std::fmt::Display for LibTableUnreadable {
    fn fmt(&self, formatter: &mut std::fmt::Formatter<'_>) -> std::fmt::Result {
        write!(
            formatter,
            "Cannot read lib-table {}: {}",
            self.path.display(),
            self.source
        )
    }
}

impl std::error::Error for LibTableUnreadable {
    fn source(&self) -> Option<&(dyn std::error::Error + 'static)> {
        Some(&self.source)
    }
}

/// The one place a [`LibTableUnreadable`] becomes an agent-facing error.
///
/// The kind comes from the `io::Error` itself, so `permission_denied` and
/// `is_a_directory` reach the caller as different codes rather than as the
/// same sentence with different words in it.
fn lib_table_error_result(error: &LibTableUnreadable) -> CallToolResult {
    CallToolResult::error_kind(ToolErrorKind::from_io(&error.source), error.to_string())
}

/// As [`read_lib_table_checked`], for callers with nowhere to put an error.
///
/// The failure is logged rather than dropped in silence. Handlers that can
/// surface it to the user should call `read_lib_table_checked` directly.
fn read_flat_lib_table(path: &Path) -> Vec<serde_json::Value> {
    match read_lib_table_checked(path) {
        Ok(libs) => libs,
        Err(error) => {
            tracing::warn!("{error}");
            Vec::new()
        }
    }
}

/// Whether a footprint reference is KiCad's `Library:Footprint` form rather
/// than a filesystem path.
///
/// "Contains a colon" is not enough, because Windows paths contain one too.
/// `C:\libs\R.kicad_mod` is caught by the separator test, but the
/// drive-*relative* form `C:R.kicad_mod` — meaning `R.kicad_mod` in the current
/// directory of drive C — carries no separator and is otherwise shaped exactly
/// like a lib id.
///
/// A one-letter prefix is therefore read as a drive letter rather than a
/// nickname. Nothing distinguishes the two, so this is a choice: a drive letter
/// is much the likelier reading, and guessing the other way means silently
/// hunting for a library named "C". The cost is that a single-letter nickname
/// cannot be written in this form — it is still reachable by path — and the
/// rule is applied on every platform so the behaviour does not change under
/// the caller's feet.
pub(crate) fn is_lib_id(reference: &str) -> bool {
    let Some((nick, _)) = reference.split_once(':') else {
        return false;
    };
    if reference.contains('/') || reference.contains('\\') {
        return false;
    }
    !(nick.len() == 1 && nick.as_bytes()[0].is_ascii_alphabetic())
}

/// The nickname the fp-lib-table gives to the library living in `dir`, if any.
///
/// This is the inverse of `resolve_footprint_path` and exists because a
/// nickname is *not* derivable from the directory name: KiCad lets a table map
/// any nickname to any path, so `MyParts` may well point at `vendor.pretty`,
/// and two nicknames may share one directory. Only the table can answer it.
///
/// Paths are compared canonicalised so a symlinked or non-normalised entry
/// still matches, falling back to a literal comparison when canonicalisation
/// fails (a directory that no longer exists, say).
pub(crate) fn footprint_lib_nickname_for_dir(dir: &Path) -> Option<String> {
    let canonical = std::fs::canonicalize(dir).ok();
    let same = |candidate: &Path| -> bool {
        match (&canonical, std::fs::canonicalize(candidate).ok()) {
            (Some(a), Some(b)) => a == &b,
            _ => candidate == dir,
        }
    };

    read_flat_lib_table(&global_fp_lib_table())
        .into_iter()
        .find(|lib| lib["path"].as_str().is_some_and(|p| same(Path::new(p))))
        .and_then(|lib| lib["nickname"].as_str().map(str::to_string))
}

/// Resolve a footprint reference to an on-disk `.kicad_mod` path.
///
/// Accepts either a direct filesystem path or KiCad's `Library:Footprint`
/// form. Returns a human-readable message on failure so callers can surface it
/// verbatim.
///
/// A lib id is looked up in `project_dir`'s fp-lib-table first, then the
/// global one, and finally the conventional `<nickname>.pretty` layout under
/// the bundled library directories. Project-first matches KiCad, where a
/// project entry shadows a global one of the same nickname, and it is the only
/// order that makes `register_footprint_library` useful — it writes to the
/// project table by default, so a global-only lookup cannot see anything it
/// registers. The `.pretty` fallback covers a stock install whose global
/// table is missing or unreadable.
///
/// (`resolve_symbol_lib_path` still searches global-first for symbols; that
/// asymmetry is pre-existing and noted on that function.)
pub(crate) fn resolve_footprint_path(
    reference: &str,
    project_dir: Option<&Path>,
) -> Result<PathBuf, FootprintPathError> {
    if !is_lib_id(reference) {
        // Check here rather than leaving it to the caller's read: an unchecked
        // path reaches the reader as a bare io::Error, which surfaces as
        // "The system cannot find the file specified. (os error 2)" with no
        // mention of what was being looked for.
        let path = PathBuf::from(reference);
        if !path.is_file() {
            return Err(FootprintPathError::FileNotFound { path });
        }
        return Ok(path);
    }

    let (nick, fp_name) = reference.split_once(':').expect("checked above");
    let filename = format!("{fp_name}.kicad_mod");

    // Project table first: its entries shadow same-nickname global ones.
    let mut libs = Vec::new();
    if let Some(project) = project_dir.map(|d| d.join("fp-lib-table")) {
        libs.extend(read_flat_lib_table(&project));
    }
    libs.extend(read_flat_lib_table(&global_fp_lib_table()));

    if let Some(lib) = libs.iter().find(|l| l["nickname"].as_str() == Some(nick)) {
        let Some(dir) = lib["path"].as_str() else {
            return Err(FootprintPathError::LibraryUriUnresolved {
                table: "fp-lib-table",
                nickname: nick.to_string(),
                uri: lib["uri"].as_str().unwrap_or("").to_string(),
            });
        };
        let path = PathBuf::from(dir).join(&filename);
        if !path.is_file() {
            return Err(FootprintPathError::FootprintNotInLibrary {
                nickname: nick.to_string(),
                footprint: fp_name.to_string(),
                looked_for: path,
            });
        }
        return Ok(path);
    }

    // Not in any table — fall back to the conventional `<nickname>.pretty`
    // layout under the discovered KiCad library directories.
    let attempted: Vec<PathBuf> = super::find_kicad_library_dirs("footprints")
        .into_iter()
        .map(|base| base.join(format!("{nick}.pretty")).join(&filename))
        .collect();
    if let Some(path) = attempted.iter().find(|p| p.is_file()) {
        return Ok(path.clone());
    }

    let known: Vec<&str> = libs
        .iter()
        .filter_map(|l| l["nickname"].as_str())
        .take(12)
        .collect();
    let attempted_list = if attempted.is_empty() {
        "no KiCad library directories were found — set KICAD10_FOOTPRINT_DIR for a \
         non-standard install"
            .to_string()
    } else {
        format!(
            "also looked for {}",
            attempted
                .iter()
                .map(|p| p.display().to_string())
                .collect::<Vec<_>>()
                .join(", ")
        )
    };
    Err(FootprintPathError::LibraryNotRegistered {
        table: "fp-lib-table",
        nickname: nick.to_string(),
        // Built here, where the search's own bookkeeping still exists: how
        // many libraries were known, which of them, and where else this
        // lookup looked. No caller downstream can reconstruct a search it
        // did not run, so the prose travels with the variant.
        detail: format!(
            "Library '{}' not found in the project or global fp-lib-table ({} libraries known{}); {}",
            nick,
            libs.len(),
            if known.is_empty() {
                String::new()
            } else {
                format!(", e.g. {}", known.join(", "))
            },
            attempted_list
        ),
    })
}

/// Why a footprint reference did not resolve to a file on disk.
///
/// D.6.5: `resolve_footprint_path` used to answer `Result<PathBuf, String>`,
/// and its own doc admitted what that cost — "a human-readable message ...
/// verbatim" covering a missing file, a library whose URI does not resolve, a
/// footprint absent from a library that exists, and a nickname registered
/// nowhere. Those are four different things to do next, and the caller had one
/// sentence to guess from.
///
/// The prose is unchanged at every variant. What is new is that the *reason*
/// survives the return, so `kind` can name it.
#[derive(Debug)]
pub(crate) enum FootprintPathError {
    /// `reference` was a filesystem path, and nothing is at it.
    FileNotFound { path: PathBuf },
    /// The nickname is registered, but its URI expanded to no path — a
    /// `${KICAD*_DIR}` that is not set, or a table entry pointing at a
    /// directory that is gone.
    LibraryUriUnresolved {
        table: &'static str,
        nickname: String,
        uri: String,
    },
    /// The library resolved; it does not contain this footprint.
    FootprintNotInLibrary {
        nickname: String,
        footprint: String,
        looked_for: PathBuf,
    },
    /// No lib-table and no conventional `.pretty` directory has this nickname.
    LibraryNotRegistered {
        table: &'static str,
        nickname: String,
        detail: String,
    },
}

impl FootprintPathError {
    /// The catalogued kind for this failure.
    ///
    /// Three of the four are `NotFound`, and the distinction a caller acts on
    /// is carried by `item_kind`: a library that is not registered is fixed by
    /// `register_footprint_library`, a library whose URI does not expand is
    /// fixed in the environment or the table, and a missing footprint is fixed
    /// by naming a different one. All three are `TransientClass::None` — no
    /// retry of the identical call resolves any of them.
    pub(crate) fn kind(&self) -> ToolErrorKind {
        match self {
            Self::FileNotFound { path } => ToolErrorKind::FileNotFound {
                path: path.display().to_string(),
            },
            Self::LibraryUriUnresolved {
                table, nickname, ..
            } => ToolErrorKind::NotFound {
                document: (*table).to_string(),
                item_kind: "library uri".to_string(),
                key: nickname.clone(),
                candidates: Vec::new(),
            },
            Self::FootprintNotInLibrary {
                nickname,
                footprint,
                ..
            } => ToolErrorKind::NotFound {
                document: nickname.clone(),
                item_kind: "footprint".to_string(),
                key: footprint.clone(),
                candidates: Vec::new(),
            },
            Self::LibraryNotRegistered {
                table, nickname, ..
            } => ToolErrorKind::NotFound {
                document: (*table).to_string(),
                item_kind: "library".to_string(),
                key: nickname.clone(),
                candidates: Vec::new(),
            },
        }
    }
}

impl std::fmt::Display for FootprintPathError {
    fn fmt(&self, formatter: &mut std::fmt::Formatter<'_>) -> std::fmt::Result {
        match self {
            Self::FileNotFound { path } => write!(
                formatter,
                "Footprint file not found: {}. Pass either a path to a .kicad_mod \
                 file or a Library:Footprint id (e.g. 'Resistor_SMD:R_0402').",
                path.display()
            ),
            Self::LibraryUriUnresolved { nickname, uri, .. } => {
                write!(
                    formatter,
                    "Library '{nickname}' has an unresolvable URI '{uri}'"
                )
            }
            Self::FootprintNotInLibrary {
                nickname,
                footprint,
                looked_for,
            } => write!(
                formatter,
                "Footprint '{}' not found in library '{}' (looked for {})",
                footprint,
                nickname,
                looked_for.display()
            ),
            Self::LibraryNotRegistered { detail, .. } => write!(formatter, "{detail}"),
        }
    }
}

impl std::error::Error for FootprintPathError {}

/// The one place a [`FootprintPathError`] becomes an agent-facing error.
fn footprint_path_error_result(error: &FootprintPathError) -> CallToolResult {
    CallToolResult::error_kind(error.kind(), error.to_string())
}

/// Extract a quoted string value from `(key "value")` within a block.
fn extract_sexp_string(block: &str, key: &str) -> Option<String> {
    let pat = format!("({} \"", key);
    let start = block.find(&pat)? + pat.len();
    let end = block[start..].find('"')? + start;
    Some(block[start..end].to_string())
}

/// The `replace_existing` policy, defaulting to `false`.
///
/// False is the conservative reading of the old behaviour: a registration used
/// to touch nothing when the nickname was present, so a default of `true`
/// would turn every repeat call into a silent rewrite of someone else's entry.
/// Correcting a stale URI is an explicit request, and the refusal that comes
/// without it names the flag.
fn replace_existing(args: &serde_json::Value) -> bool {
    args["replace_existing"].as_bool().unwrap_or(false)
}

/// The one place a [`LibTableRegistration`] becomes an agent-facing answer,
/// shared by the footprint and symbol registrars so the two report the same
/// vocabulary for the same outcome.
fn registration_result(
    outcome: &LibTableRegistration,
    nickname: &str,
    scope: &str,
    table_path: &Path,
    requested_uri: &str,
) -> CallToolResult {
    let table = table_path.to_str().unwrap_or("");
    if let LibTableRegistration::UriConflict { existing_uri } = outcome {
        return CallToolResult::error_kind(
            crate::mcp::error::ToolErrorKind::InvalidArgument {
                field: "replace_existing".to_string(),
                reason: "nickname already registered with a different URI".to_string(),
            },
            format!(
                "'{nickname}' is already registered in {table} as '{existing_uri}', not \
                 '{requested_uri}'. Nothing was written — pass replace_existing: true to \
                 correct the URI in place, or register under another nickname."
            ),
        );
    }

    let mut body = json!({
        "success": true,
        "result": outcome.as_str(),
        "nickname": nickname,
        "scope": scope,
        "table": table,
        "uri": requested_uri
    });
    if let LibTableRegistration::Updated { previous_uri } = outcome {
        body["previous_uri"] = json!(previous_uri);
    }
    CallToolResult::text(serde_json::to_string(&body).unwrap())
}

async fn handle_register_footprint_library(
    args: &serde_json::Value,
    _ctx: &ToolContext,
) -> anyhow::Result<CallToolResult> {
    let lib_path = get_path(args, "library_path")?;
    let nickname = try_arg!(require_str(args, "nickname"));
    let scope = args["scope"].as_str().unwrap_or("project");

    let table_path = if scope == "global" {
        global_fp_lib_table()
    } else if let Some(proj) = args["project"].as_str() {
        PathBuf::from(proj)
            .parent()
            .unwrap_or(Path::new("."))
            .join("fp-lib-table")
    } else {
        return Ok(CallToolResult::error_kind(
            crate::mcp::error::ToolErrorKind::InvalidArgument {
                field: "project".to_string(),
                reason: "required for project scope".to_string(),
            },
            "For project scope, provide 'project' path to .kicad_pro file",
        ));
    };

    let requested_uri = lib_path.to_str().unwrap_or("");
    let outcome = register_in_lib_table(
        &table_path,
        nickname,
        requested_uri,
        "KiCad",
        replace_existing(args),
    )
    .await?;

    Ok(registration_result(
        &outcome,
        nickname,
        scope,
        &table_path,
        requested_uri,
    ))
}

async fn handle_list_footprint_libraries(
    args: &serde_json::Value,
    _ctx: &ToolContext,
) -> anyhow::Result<CallToolResult> {
    let scope = args["scope"].as_str().unwrap_or("all");
    let mut all_libs = Vec::new();

    // A table that exists but cannot be read is reported rather than counted
    // as zero libraries — "0" is the symptom of the bug this PR fixes, so the
    // two must not look alike.
    if scope == "global" || scope == "all" {
        let mut libs = match read_lib_table_checked(&global_fp_lib_table()) {
            Ok(libs) => libs,
            Err(error) => return Ok(lib_table_error_result(&error)),
        };
        for lib in &mut libs {
            lib["scope"] = json!("global");
        }
        all_libs.extend(libs);
    }

    if (scope == "project" || scope == "all") && args["project"].is_string() {
        let proj = PathBuf::from(args["project"].as_str().unwrap());
        let table = proj.parent().unwrap_or(Path::new(".")).join("fp-lib-table");
        let mut libs = match read_lib_table_checked(&table) {
            Ok(libs) => libs,
            Err(error) => return Ok(lib_table_error_result(&error)),
        };
        for lib in &mut libs {
            lib["scope"] = json!("project");
        }
        all_libs.extend(libs);
    }

    Ok(CallToolResult::text(
        serde_json::to_string(&json!({
            "count": all_libs.len(),
            "libraries": all_libs
        }))
        .unwrap(),
    ))
}

async fn handle_register_symbol_library(
    args: &serde_json::Value,
    _ctx: &ToolContext,
) -> anyhow::Result<CallToolResult> {
    let lib_path = get_path(args, "library_path")?;
    let nickname = try_arg!(require_str(args, "nickname"));
    let scope = args["scope"].as_str().unwrap_or("project");

    let table_path = if scope == "global" {
        global_sym_lib_table()
    } else if let Some(proj) = args["project"].as_str() {
        PathBuf::from(proj)
            .parent()
            .unwrap_or(Path::new("."))
            .join("sym-lib-table")
    } else {
        return Ok(CallToolResult::error_kind(
            crate::mcp::error::ToolErrorKind::InvalidArgument {
                field: "project".to_string(),
                reason: "required for project scope".to_string(),
            },
            "For project scope, provide 'project' path to .kicad_pro file",
        ));
    };

    let requested_uri = lib_path.to_str().unwrap_or("");
    let outcome = register_in_lib_table(
        &table_path,
        nickname,
        requested_uri,
        "KiCad",
        replace_existing(args),
    )
    .await?;

    Ok(registration_result(
        &outcome,
        nickname,
        scope,
        &table_path,
        requested_uri,
    ))
}

async fn handle_list_symbol_libraries(
    args: &serde_json::Value,
    _ctx: &ToolContext,
) -> anyhow::Result<CallToolResult> {
    let scope = args["scope"].as_str().unwrap_or("all");
    let mut all_libs = Vec::new();

    // Same as the footprint listing: an unreadable table is an error, not a
    // zero count.
    if scope == "global" || scope == "all" {
        let mut libs = match read_lib_table_checked(&global_sym_lib_table()) {
            Ok(libs) => libs,
            Err(error) => return Ok(lib_table_error_result(&error)),
        };
        for lib in &mut libs {
            lib["scope"] = json!("global");
        }
        all_libs.extend(libs);
    }

    if (scope == "project" || scope == "all") && args["project"].is_string() {
        let proj = PathBuf::from(args["project"].as_str().unwrap());
        let table = proj
            .parent()
            .unwrap_or(Path::new("."))
            .join("sym-lib-table");
        let mut libs = match read_lib_table_checked(&table) {
            Ok(libs) => libs,
            Err(error) => return Ok(lib_table_error_result(&error)),
        };
        for lib in &mut libs {
            lib["scope"] = json!("project");
        }
        all_libs.extend(libs);
    }

    Ok(CallToolResult::text(
        serde_json::to_string(&json!({
            "count": all_libs.len(),
            "libraries": all_libs
        }))
        .unwrap(),
    ))
}

/// Root S-expression element for a lib-table file, decided by its filename:
/// `sym-lib-table` uses `sym_lib_table`, everything else (`fp-lib-table`)
/// uses `fp_lib_table`. Credit: first diagnosed in PR #54 (presire) — the
/// hardcoded `fp_lib_table` scaffold produced symbol tables KiCad rejects.
fn table_root_element(table_path: &Path) -> &'static str {
    let is_sym = table_path
        .file_name()
        .and_then(|n| n.to_str())
        .is_some_and(|n| n.contains("sym"));
    if is_sym {
        "sym_lib_table"
    } else {
        "fp_lib_table"
    }
}

/// What a call to [`register_in_lib_table`] did to the table.
///
/// P.6.9.12: the function used to return `()`, so "wrote the entry" and "found
/// the nickname and did nothing" reached the caller as the same bare
/// `"success": true`. A no-op was indistinguishable from a registration, and a
/// stale URI could not be corrected at all — re-registering hit the early
/// return and reported success without touching the table.
#[derive(Debug, Clone, PartialEq, Eq)]
enum LibTableRegistration {
    /// The nickname was not in the table; the entry was appended.
    Inserted,
    /// The nickname was already registered against this exact URI. The file
    /// is not rewritten, so it stays byte-identical.
    Unchanged,
    /// The nickname was registered against a different URI and
    /// `replace_existing` allowed correcting it in place.
    Updated { previous_uri: String },
    /// The nickname was registered against a different URI and
    /// `replace_existing` was not set. Nothing was written.
    UriConflict { existing_uri: String },
}

impl LibTableRegistration {
    /// The word the tool reports.
    fn as_str(&self) -> &'static str {
        match self {
            Self::Inserted => "inserted",
            Self::Unchanged => "unchanged",
            Self::Updated { .. } => "updated",
            Self::UriConflict { .. } => "uri_conflict",
        }
    }
}

/// Byte range of the `(lib …)` block in `content` whose `(name …)` is
/// `nickname`.
///
/// Not `content.contains("(name \"X\")")`, which is what this replaced: that
/// is a substring test over the whole file, so any entry whose `descr` quotes
/// the text made `X` look registered. [`find_block_starts`] skips quoted
/// strings and matches whole tags, and [`find_balanced_block`] closes the
/// entry by nesting depth — the same pair [`parse_lib_table`] already reads
/// these tables with, rather than a second parser for the same file.
fn find_lib_entry(content: &str, nickname: &str) -> Option<(usize, usize)> {
    find_block_starts(content, "lib")
        .into_iter()
        .filter_map(|start| find_balanced_block(content, start))
        .find(|&(block_start, block_end)| {
            extract_sexp_string(&content[block_start..block_end], "name").as_deref()
                == Some(nickname)
        })
}

/// Insert a new `(lib ...)` entry into a lib-table file (fp-lib-table or sym-lib-table),
/// or correct an existing entry's URI when `replace_existing` is set.
/// Creates the file with minimal scaffolding if it doesn't exist.
///
/// An update rewrites the `(uri …)` sub-block and nothing else, so the entry's
/// own `options` and `descr` — whatever the user or KiCad put there — survive
/// the correction.
async fn register_in_lib_table(
    table_path: &Path,
    nickname: &str,
    uri: &str,
    lib_type: &str,
    replace_existing: bool,
) -> anyhow::Result<LibTableRegistration> {
    let content = if table_path.exists() {
        tokio::fs::read_to_string(table_path).await?
    } else {
        // The scaffold's root element must match the table kind: a
        // sym-lib-table created with an (fp_lib_table root is rejected by
        // KiCad. Decide from the filename, which is fixed by convention.
        format!("({}\n  (version 7)\n)\n", table_root_element(table_path))
    };

    let (new_content, outcome) = match find_lib_entry(&content, nickname) {
        Some((entry_start, entry_end)) => {
            let entry = &content[entry_start..entry_end];
            let existing_uri = extract_sexp_string(entry, "uri").unwrap_or_default();
            if existing_uri == uri {
                return Ok(LibTableRegistration::Unchanged);
            }
            if !replace_existing {
                return Ok(LibTableRegistration::UriConflict { existing_uri });
            }
            // Replace only the (uri …) sub-block, keeping the rest of the
            // entry — an entry with no uri at all gets one before its closing
            // paren.
            let (uri_start, uri_end) = find_block_starts(entry, "uri")
                .into_iter()
                .find_map(|start| find_balanced_block(entry, start))
                .unwrap_or((entry.len() - 1, entry.len() - 1));
            let rewritten = format!(
                "{}(uri \"{}\"){}",
                &entry[..uri_start],
                uri,
                &entry[uri_end..]
            );
            (
                format!(
                    "{}{}{}",
                    &content[..entry_start],
                    rewritten,
                    &content[entry_end..]
                ),
                LibTableRegistration::Updated {
                    previous_uri: existing_uri,
                },
            )
        }
        None => {
            // Find closing paren of the root expression
            let insert_pos = content.rfind(')').unwrap_or(content.len());
            let entry = format!(
                "\n  (lib (name \"{}\") (type \"{}\") (uri \"{}\") (options \"\") (descr \"\"))",
                nickname, lib_type, uri
            );
            (
                format!("{}{}\n)", &content[..insert_pos], entry),
                LibTableRegistration::Inserted,
            )
        }
    };

    if let Some(parent) = table_path.parent() {
        tokio::fs::create_dir_all(parent).await?;
    }
    write_atomic(table_path, &new_content)?;
    Ok(outcome)
}

// ─── Symbol library tools ─────────────────────────────────────────────────────

/// Minimal pin geometry for deriving the symbol body.
#[derive(Debug, Clone, Copy)]
struct PinGeom {
    x: f64,
    y: f64,
    angle: f64,
    length: f64,
}

/// The point where a pin meets the symbol body. In KiCAD symbols the pin's
/// connection endpoint (the "bulb", where wires attach) is at `(x, y)` and the
/// pin extends by `length` in its orientation to reach the body outline. Angles
/// are 0=E, 90=N, 180=W, 270=S with Y up, so the body-attach point (root) is
/// `(x + length*cos, y + length*sin)` — on the far side of the bulb.
fn pin_root(x: f64, y: f64, angle_deg: f64, length: f64) -> (f64, f64) {
    let a = angle_deg.to_radians();
    (x + length * a.cos(), y + length * a.sin())
}

/// Body rectangle `(min_x, min_y, max_x, max_y)` for a symbol: edges that pins
/// attach to pass through those pins' roots (so each pin's far end touches the
/// border and its connection bulb sits outside), and edges with no pins are
/// pushed out by a margin so there is clear spacing beyond the outermost pins.
/// `None` when there are no pins.
fn symbol_body_rect(pins: &[PinGeom]) -> Option<(f64, f64, f64, f64)> {
    if pins.is_empty() {
        return None;
    }
    let roots: Vec<(f64, f64)> = pins
        .iter()
        .map(|p| pin_root(p.x, p.y, p.angle, p.length))
        .collect();
    let mut min_x = f64::INFINITY;
    let mut min_y = f64::INFINITY;
    let mut max_x = f64::NEG_INFINITY;
    let mut max_y = f64::NEG_INFINITY;
    for &(x, y) in &roots {
        min_x = min_x.min(x);
        min_y = min_y.min(y);
        max_x = max_x.max(x);
        max_y = max_y.max(y);
    }

    // Which edges have pins attaching, by orientation (Y up): a pin pointing
    // right (0) sits on the left edge, left (180) on the right edge, up (90) on
    // the bottom edge, down (270) on the top edge.
    let norm = |a: f64| ((a % 360.0) + 360.0) % 360.0;
    let near = |a: f64, t: f64| {
        let d = (norm(a) - t).abs();
        !(1.0..=359.0).contains(&d)
    };
    let (mut has_left, mut has_right, mut has_bottom, mut has_top) = (false, false, false, false);
    for p in pins {
        if near(p.angle, 0.0) {
            has_left = true;
        } else if near(p.angle, 180.0) {
            has_right = true;
        } else if near(p.angle, 90.0) {
            has_bottom = true;
        } else if near(p.angle, 270.0) {
            has_top = true;
        }
    }

    // Spacing beyond the last pin on any edge without attachments (~1 grid).
    let margin = 2.54;
    if !has_left {
        min_x -= margin;
    }
    if !has_right {
        max_x += margin;
    }
    if !has_bottom {
        min_y -= margin;
    }
    if !has_top {
        max_y += margin;
    }

    // Minimum visible body.
    let min_size = 2.54;
    if max_x - min_x < min_size {
        let c = (min_x + max_x) / 2.0;
        min_x = c - min_size / 2.0;
        max_x = c + min_size / 2.0;
    }
    if max_y - min_y < min_size {
        let c = (min_y + max_y) / 2.0;
        min_y = c - min_size / 2.0;
        max_y = c + min_size / 2.0;
    }
    Some((min_x, min_y, max_x, max_y))
}

/// KiCAD's 12 valid pin electrical types — the first token of a
/// `(pin TYPE line …)` S-expression. Anything else makes eeschema refuse to
/// load the library ("Failed to load schematic"-class parse error), so the
/// value is validated instead of interpolated verbatim (#55).
const ALLOWED_PIN_ELECTRICAL_TYPES: [&str; 12] = [
    "input",
    "output",
    "bidirectional",
    "tri_state",
    "passive",
    "free",
    "unspecified",
    "power_in",
    "power_out",
    "open_collector",
    "open_emitter",
    "no_connect",
];

/// Error when any pin's electrical type is not one of KiCAD's 12 valid values
/// (#55) — eeschema refuses to load a library with a bad type, so nothing must
/// be written in that case. Shared by the rectangle and glyph paths.
fn validate_pin_types(pins_val: &[serde_json::Value]) -> anyhow::Result<()> {
    for pin in pins_val {
        let pin_type = pin["type"].as_str().unwrap_or("passive");
        if !ALLOWED_PIN_ELECTRICAL_TYPES.contains(&pin_type) {
            let number = pin["number"].as_str().unwrap_or("1");
            // The one mistake seen in the wild (#55) gets a targeted hint.
            let hint = if pin_type == "not_connected" {
                " (did you mean \"no_connect\"?)"
            } else {
                ""
            };
            anyhow::bail!(
                "invalid pin electrical type \"{}\" on pin \"{}\"{} — KiCAD accepts exactly one of: {}",
                pin_type,
                number,
                hint,
                ALLOWED_PIN_ELECTRICAL_TYPES.join(", ")
            );
        }
    }
    Ok(())
}

/// A conventional body shape for a symbol unit. `Rectangle` is the default (a
/// derived box around caller-positioned pins); the others draw a fixed op-amp or
/// logic-gate glyph copied from KiCAD's stock libraries and auto-place the pins.
#[derive(Debug, Clone, Copy, PartialEq, Eq)]
enum Glyph {
    Rectangle,
    Opamp,
    Buffer,
    Inverter,
    Schmitt,
    SchmittInverter,
    And,
    Nand,
    Or,
    Nor,
    Xor,
    Xnor,
}

impl Glyph {
    fn parse(s: &str) -> Option<Glyph> {
        Some(match s {
            "rectangle" => Glyph::Rectangle,
            "opamp" => Glyph::Opamp,
            "buffer" => Glyph::Buffer,
            "inverter" => Glyph::Inverter,
            "schmitt" => Glyph::Schmitt,
            "schmitt_inverter" => Glyph::SchmittInverter,
            "and" => Glyph::And,
            "nand" => Glyph::Nand,
            "or" => Glyph::Or,
            "nor" => Glyph::Nor,
            "xor" => Glyph::Xor,
            "xnor" => Glyph::Xnor,
            _ => return None,
        })
    }

    fn name(self) -> &'static str {
        match self {
            Glyph::Rectangle => "rectangle",
            Glyph::Opamp => "opamp",
            Glyph::Buffer => "buffer",
            Glyph::Inverter => "inverter",
            Glyph::Schmitt => "schmitt",
            Glyph::SchmittInverter => "schmitt_inverter",
            Glyph::And => "and",
            Glyph::Nand => "nand",
            Glyph::Or => "or",
            Glyph::Nor => "nor",
            Glyph::Xor => "xor",
            Glyph::Xnor => "xnor",
        }
    }

    /// Inverting glyphs draw the same body as their non-inverting base and mark
    /// the inversion with an `inverted` output pin (matching KiCAD's own gates,
    /// which carry the bubble on the pin rather than as a body circle).
    fn is_inverting(self) -> bool {
        matches!(
            self,
            Glyph::Inverter | Glyph::SchmittInverter | Glyph::Nand | Glyph::Nor | Glyph::Xnor
        )
    }

    /// How many input pins the fixed geometry has room for.
    fn input_count(self) -> usize {
        match self {
            Glyph::Buffer | Glyph::Inverter | Glyph::Schmitt | Glyph::SchmittInverter => 1,
            _ => 2,
        }
    }

    /// The narrow triangle-bodied glyphs (op-amp and the buffer family). Their
    /// apex leaves no room for power-pin names, so a single-unit triangular
    /// symbol that carries power pins puts them on a separate rectangular power
    /// unit instead (the gate glyphs have a flat back with room, so they keep
    /// their power pins on the body).
    fn is_triangular(self) -> bool {
        matches!(
            self,
            Glyph::Opamp
                | Glyph::Buffer
                | Glyph::Inverter
                | Glyph::Schmitt
                | Glyph::SchmittInverter
        )
    }
}

/// Whether a pin is a supply pin (belongs on a power unit).
fn is_power_pin(p: &serde_json::Value) -> bool {
    matches!(p["type"].as_str(), Some("power_in") | Some("power_out"))
}

/// Lay out power pins for a standalone rectangular power unit: vertical, V+/V-
/// style — even-indexed pins enter from the top (pointing down), odd from the
/// bottom (pointing up), matching KiCAD's multi-unit op-amp power unit. Any
/// caller x/y is replaced. Same spread (bulbs at y = ±7.62) as the multi-unit
/// `power_pins` path so a single op-amp's power unit matches a dual's.
fn layout_power_unit(power: &[serde_json::Value]) -> Vec<serde_json::Value> {
    let n_top = power.len().div_ceil(2);
    let n_bot = power.len() / 2;
    let mut top_i = 0usize;
    let mut bot_i = 0usize;
    power
        .iter()
        .enumerate()
        .map(|(i, p)| {
            let mut q = p.clone();
            if let Some(obj) = q.as_object_mut() {
                if i % 2 == 0 {
                    let x = (top_i as f64 - (n_top as f64 - 1.0) / 2.0) * 2.54;
                    obj.insert("x".into(), json!(x));
                    obj.insert("y".into(), json!(7.62));
                    obj.insert("angle".into(), json!(270));
                    obj.insert("length".into(), json!(2.54));
                    top_i += 1;
                } else {
                    let x = (bot_i as f64 - (n_bot as f64 - 1.0) / 2.0) * 2.54;
                    obj.insert("x".into(), json!(x));
                    obj.insert("y".into(), json!(-7.62));
                    obj.insert("angle".into(), json!(90));
                    obj.insert("length".into(), json!(2.54));
                    bot_i += 1;
                }
            }
            q
        })
        .collect()
}

/// Normalize a caller-supplied pin graphic style to a valid KiCAD token,
/// defaulting to `line`.
fn pin_style_token(s: Option<&str>) -> &'static str {
    match s {
        Some("inverted") => "inverted",
        Some("clock") => "clock",
        Some("inverted_clock") => "inverted_clock",
        Some("input_low") => "input_low",
        Some("clock_low") => "clock_low",
        Some("output_low") => "output_low",
        Some("edge_clock_high") => "edge_clock_high",
        Some("non_logic") => "non_logic",
        _ => "line",
    }
}

/// Default pin name/number text height (KiCAD's default).
const PIN_TEXT: f64 = 1.27;
/// Smaller pin-name height for glyph units. The fixed op-amp/gate bodies are
/// compact (KiCAD's own gates keep pin names empty on them), so real pin names
/// at the default 1.27 mm collide; 0.762 mm (KiCAD's standard small text) fits
/// them without enlarging the body and breaking the library-matching shape.
const GLYPH_PIN_NAME_TEXT: f64 = 0.762;

/// One `(pin …)` S-expression. `name_font` sets the pin-name text height;
/// numbers stay at the default (they sit outside the body and don't crowd).
#[allow(clippy::too_many_arguments)]
fn emit_pin(
    pin_type: &str,
    style: &str,
    x: f64,
    y: f64,
    angle: f64,
    length: f64,
    name: &str,
    number: &str,
    name_font: f64,
) -> String {
    format!(
        "\n    (pin {} {} (at {} {} {})\n      (length {})\n      (name \"{}\" (effects (font (size {} {}))))\n      (number \"{}\" (effects (font (size {} {}))))\n    )",
        pin_type, style, x, y, angle, length, name, name_font, name_font, number, PIN_TEXT, PIN_TEXT
    )
}

// ── Glyph geometry (coordinates copied verbatim from KiCAD 10's stock symbols)

fn fmt_pts(pts: &[(f64, f64)]) -> String {
    pts.iter()
        .map(|(x, y)| format!("(xy {} {})", x, y))
        .collect::<Vec<_>>()
        .join(" ")
}

fn g_polyline(pts: &[(f64, f64)], width: f64, fill: &str) -> String {
    format!(
        "\n      (polyline (pts {}) (stroke (width {}) (type default)) (fill (type {})))",
        fmt_pts(pts),
        width,
        fill
    )
}

fn g_arc(s: (f64, f64), m: (f64, f64), e: (f64, f64), fill: &str) -> String {
    format!(
        "\n      (arc (start {} {}) (mid {} {}) (end {} {}) (stroke (width 0.254) (type default)) (fill (type {})))",
        s.0, s.1, m.0, m.1, e.0, e.1, fill
    )
}

/// The OR/NOR body (also the base of XOR/XNOR): a concave back arc, two back
/// stubs, two front arcs meeting at the apex, and KiCAD's fill-outline polyline.
fn or_body() -> String {
    let mut b = g_arc((-3.81, 3.81), (-2.589, 0.0), (-3.81, -3.81), "none");
    b.push_str(&g_polyline(
        &[(-3.81, 3.81), (-0.635, 3.81)],
        0.254,
        "background",
    ));
    b.push_str(&g_polyline(
        &[(-3.81, -3.81), (-0.635, -3.81)],
        0.254,
        "background",
    ));
    b.push_str(&g_arc(
        (3.81, 0.0),
        (2.1855, -2.584),
        (-0.6096, -3.81),
        "background",
    ));
    b.push_str(&g_arc(
        (-0.6096, 3.81),
        (2.1928, 2.5924),
        (3.81, 0.0),
        "background",
    ));
    b.push_str(&g_polyline(
        &[
            (-0.635, 3.81),
            (-3.81, 3.81),
            (-3.81, 3.81),
            (-3.556, 3.4036),
            (-3.0226, 2.2606),
            (-2.6924, 1.0414),
            (-2.6162, -0.254),
            (-2.7686, -1.4986),
            (-3.175, -2.7178),
            (-3.81, -3.81),
            (-3.81, -3.81),
            (-0.635, -3.81),
        ],
        -25.4,
        "background",
    ));
    b
}

/// Fixed body + pin anchors for a glyph. Input anchors are ordered
/// top-to-bottom; the caller's pin order maps onto them in that order.
/// `power_top`/`power_bottom` are the points *on the body outline* where a
/// power pin's root should land (so the pin visually touches the shape, not the
/// bounding box).
struct GlyphGeom {
    body: String,
    inputs: Vec<(f64, f64, f64, f64)>,
    output: (f64, f64, f64, f64),
    power_top: (f64, f64),
    power_bottom: (f64, f64),
    rect: (f64, f64, f64, f64),
}

fn glyph_geom(g: Glyph) -> GlyphGeom {
    match g {
        Glyph::Rectangle => unreachable!("rectangle is handled by the rectangle path"),
        Glyph::Opamp => GlyphGeom {
            body: g_polyline(
                &[(-5.08, 5.08), (5.08, 0.0), (-5.08, -5.08), (-5.08, 5.08)],
                0.254,
                "background",
            ),
            inputs: vec![(-7.62, 2.54, 0.0, 2.54), (-7.62, -2.54, 0.0, 2.54)],
            output: (7.62, 0.0, 180.0, 2.54),
            // Centered on the triangle top/bottom edges (at x = 0, y = ±2.54),
            // so the power names clear the +/- input names on the left.
            power_top: (0.0, 2.54),
            power_bottom: (0.0, -2.54),
            rect: (-5.08, -5.08, 5.08, 5.08),
        },
        Glyph::Buffer | Glyph::Inverter => GlyphGeom {
            body: g_polyline(
                &[(-3.81, 3.81), (-3.81, -3.81), (3.81, 0.0), (-3.81, 3.81)],
                0.254,
                "background",
            ),
            inputs: vec![(-7.62, 0.0, 0.0, 3.81)],
            output: (7.62, 0.0, 180.0, 3.81),
            // Centered on the triangle top/bottom edges (x = 0, y = ±1.905).
            power_top: (0.0, 1.905),
            power_bottom: (0.0, -1.905),
            rect: (-3.81, -3.81, 3.81, 3.81),
        },
        Glyph::Schmitt | Glyph::SchmittInverter => {
            let mut body = g_polyline(
                &[(-3.81, 3.81), (-3.81, -3.81), (3.81, 0.0), (-3.81, 3.81)],
                0.254,
                "background",
            );
            // Hysteresis mark (from KiCAD's 74HC14).
            body.push_str(&g_polyline(
                &[(-2.54, -1.27), (-0.635, -1.27), (-0.635, 1.27), (0.0, 1.27)],
                0.254,
                "none",
            ));
            body.push_str(&g_polyline(
                &[(-1.905, -1.27), (-1.905, 1.27), (-0.635, 1.27)],
                0.254,
                "none",
            ));
            GlyphGeom {
                body,
                inputs: vec![(-7.62, 0.0, 0.0, 3.81)],
                output: (7.62, 0.0, 180.0, 3.81),
                // Centered (x = 0, y = ±1.905); the hysteresis mark sits at x <= 0.
                power_top: (0.0, 1.905),
                power_bottom: (0.0, -1.905),
                rect: (-3.81, -3.81, 3.81, 3.81),
            }
        }
        Glyph::And | Glyph::Nand => {
            let mut body = g_arc((0.0, 3.81), (3.7934, 0.0), (0.0, -3.81), "background");
            body.push_str(&g_polyline(
                &[(0.0, 3.81), (-3.81, 3.81), (-3.81, -3.81), (0.0, -3.81)],
                0.254,
                "background",
            ));
            GlyphGeom {
                body,
                inputs: vec![(-7.62, 2.54, 0.0, 3.81), (-7.62, -2.54, 0.0, 3.81)],
                output: (7.62, 0.0, 180.0, 3.81),
                // Right end of the flat back edges (x = 0, y = ±3.81), away from
                // the input names on the left.
                power_top: (0.0, 3.81),
                power_bottom: (0.0, -3.81),
                rect: (-3.81, -3.81, 3.81, 3.81),
            }
        }
        Glyph::Or | Glyph::Nor => GlyphGeom {
            body: or_body(),
            // Longer than the gates above: the back is a *concave* arc that sits
            // at x ≈ -3.10 at the input height, so length 4.52 puts the roots on
            // the curve (3.81 would leave a visible gap).
            inputs: vec![(-7.62, 2.54, 0.0, 4.52), (-7.62, -2.54, 0.0, 4.52)],
            output: (7.62, 0.0, 180.0, 3.81),
            // Rightmost point of the flat back stubs (y = ±3.81, x = -0.635),
            // away from the input names on the left.
            power_top: (-0.635, 3.81),
            power_bottom: (-0.635, -3.81),
            rect: (-3.81, -3.81, 3.81, 3.81),
        },
        Glyph::Xor | Glyph::Xnor => {
            // OR body plus a second offset back arc and two input stubs.
            let mut body = g_arc((-4.4196, 3.81), (-3.2033, 0.0), (-4.4196, -3.81), "none");
            body.push_str(&or_body());
            body.push_str(&g_polyline(
                &[(-3.81, 2.54), (-3.175, 2.54)],
                0.254,
                "background",
            ));
            body.push_str(&g_polyline(
                &[(-3.81, -2.54), (-3.175, -2.54)],
                0.254,
                "background",
            ));
            GlyphGeom {
                body,
                inputs: vec![(-7.62, 2.54, 0.0, 4.445), (-7.62, -2.54, 0.0, 4.445)],
                output: (7.62, 0.0, 180.0, 3.81),
                // Rightmost flat point of the back stubs (x = -0.635, y = ±3.81).
                power_top: (-0.635, 3.81),
                power_bottom: (-0.635, -3.81),
                rect: (-4.4196, -3.81, 3.81, 3.81),
            }
        }
    }
}

/// Build a glyph unit: the fixed body plus auto-placed pins. Returns `Err(msg)`
/// when the unit's pins don't fit the glyph (wrong input count, not exactly one
/// output, or unsupported pin types) so the caller can fall back to a rectangle.
fn build_glyph_unit(
    pins_val: &[serde_json::Value],
    g: Glyph,
) -> Result<(String, SymbolRect), String> {
    let mut inputs: Vec<&serde_json::Value> = Vec::new();
    let mut outputs: Vec<&serde_json::Value> = Vec::new();
    let mut powers: Vec<&serde_json::Value> = Vec::new();
    let mut others = 0usize;
    for p in pins_val {
        match p["type"].as_str().unwrap_or("passive") {
            "input" => inputs.push(p),
            "output" | "tri_state" | "open_collector" | "open_emitter" => outputs.push(p),
            "power_in" | "power_out" => powers.push(p),
            _ => others += 1,
        }
    }

    let want = g.input_count();
    if inputs.len() != want {
        return Err(format!(
            "glyph '{}' expects {} input pin(s) but {} were given; drew a rectangle instead",
            g.name(),
            want,
            inputs.len()
        ));
    }
    if outputs.len() != 1 {
        return Err(format!(
            "glyph '{}' expects exactly 1 output pin but {} were given; drew a rectangle instead",
            g.name(),
            outputs.len()
        ));
    }
    if others > 0 {
        return Err(format!(
            "glyph '{}' only supports input/output/power pins; drew a rectangle instead",
            g.name()
        ));
    }

    let geom = glyph_geom(g);
    let mut sexp = geom.body.clone();

    // Inputs map onto the glyph anchors in the caller's order (top-to-bottom).
    for (p, &(x, y, angle, length)) in inputs.iter().zip(geom.inputs.iter()) {
        let number = p["number"].as_str().unwrap_or("1");
        let name = p["name"].as_str().unwrap_or("~");
        let style = pin_style_token(p["style"].as_str());
        sexp.push_str(&emit_pin(
            "input",
            style,
            x,
            y,
            angle,
            length,
            name,
            number,
            GLYPH_PIN_NAME_TEXT,
        ));
    }

    // The single output sits at the apex; inverting glyphs default to an
    // inverted pin (the bubble), but the caller can override via `style`.
    let out = outputs[0];
    let out_number = out["number"].as_str().unwrap_or("1");
    let out_name = out["name"].as_str().unwrap_or("~");
    let out_type = out["type"].as_str().unwrap_or("output");
    let out_style = match out["style"].as_str() {
        Some(s) => pin_style_token(Some(s)),
        None if g.is_inverting() => "inverted",
        None => "line",
    };
    let (ox, oy, oa, ol) = geom.output;
    sexp.push_str(&emit_pin(
        out_type,
        out_style,
        ox,
        oy,
        oa,
        ol,
        out_name,
        out_number,
        GLYPH_PIN_NAME_TEXT,
    ));

    // Power pins (e.g. a single op-amp's V+/V-) enter vertically, alternating
    // top/bottom, with their roots on the body outline so they touch the shape.
    for (i, p) in powers.iter().enumerate() {
        let number = p["number"].as_str().unwrap_or("1");
        let name = p["name"].as_str().unwrap_or("~");
        let ptype = p["type"].as_str().unwrap_or("power_in");
        let style = pin_style_token(p["style"].as_str());
        let length = 2.54;
        let (x, y, angle) = if i % 2 == 0 {
            let (ax, ay) = geom.power_top;
            (ax, ay + length, 270.0) // bulb above, root on the top edge
        } else {
            let (ax, ay) = geom.power_bottom;
            (ax, ay - length, 90.0) // bulb below, root on the bottom edge
        };
        sexp.push_str(&emit_pin(
            ptype,
            style,
            x,
            y,
            angle,
            length,
            name,
            number,
            GLYPH_PIN_NAME_TEXT,
        ));
    }

    Ok((sexp, Some(geom.rect)))
}

/// Build one unit's inner S-expression — an optional body (a rectangle, or a
/// conventional `glyph` shape) followed by its pins — and return it with the
/// body rect (used for reference/value placement) and an optional warning (e.g.
/// a glyph that didn't fit its pins and fell back to a rectangle). Shared by the
/// single- and multi-unit paths.
///
/// Errors (#55) when a pin's electrical type is not one of KiCAD's 12 valid
/// values — the caller must not write anything to disk in that case.
fn build_symbol_unit(
    pins_val: &[serde_json::Value],
    with_body: bool,
    glyph: Option<Glyph>,
) -> anyhow::Result<(String, SymbolRect, Option<String>)> {
    validate_pin_types(pins_val)?;
    if let Some(g) = glyph {
        if g != Glyph::Rectangle {
            match build_glyph_unit(pins_val, g) {
                Ok((sexp, rect)) => return Ok((sexp, rect, None)),
                Err(reason) => {
                    let (sexp, rect) = build_rect_unit(pins_val, with_body);
                    return Ok((sexp, rect, Some(reason)));
                }
            }
        }
    }
    let (sexp, rect) = build_rect_unit(pins_val, with_body);
    Ok((sexp, rect, None))
}

/// The default rectangle body + caller-positioned pins. Pin types are assumed
/// already validated by `build_symbol_unit`.
fn build_rect_unit(pins_val: &[serde_json::Value], with_body: bool) -> (String, SymbolRect) {
    let mut pins_sexp = String::new();
    let mut pin_geoms: Vec<PinGeom> = Vec::new();
    for pin in pins_val {
        let number = pin["number"].as_str().unwrap_or("1");
        let pin_name = pin["name"].as_str().unwrap_or("~");
        let pin_type = pin["type"].as_str().unwrap_or("passive");
        let style = pin_style_token(pin["style"].as_str());
        let x = pin["x"].as_f64().unwrap_or(0.0);
        let y = pin["y"].as_f64().unwrap_or(0.0);
        let angle = pin["angle"].as_f64().unwrap_or(0.0);
        let length = pin["length"].as_f64().unwrap_or(2.54);

        pin_geoms.push(PinGeom {
            x,
            y,
            angle,
            length,
        });
        pins_sexp.push_str(&emit_pin(
            pin_type, style, x, y, angle, length, pin_name, number, PIN_TEXT,
        ));
    }
    let body = if with_body {
        symbol_body_rect(&pin_geoms)
    } else {
        None
    };
    let body_sexp = match body {
        Some((min_x, min_y, max_x, max_y)) => format!(
            "\n      (rectangle (start {:.4} {:.4}) (end {:.4} {:.4})\n        (stroke (width 0.254) (type default))\n        (fill (type background))\n      )",
            min_x, min_y, max_x, max_y
        ),
        None => String::new(),
    };
    (format!("{}{}", body_sexp, pins_sexp), body)
}

type SymbolRect = Option<(f64, f64, f64, f64)>;

async fn handle_create_symbol(
    args: &serde_json::Value,
    _ctx: &ToolContext,
) -> anyhow::Result<CallToolResult> {
    let lib_path = get_path(args, "library_path")?;
    // Both are `required` in the schema; the old defaults appended a symbol
    // named "Symbol" with prefix "U" to the caller's library.
    let name = try_arg!(require_str(args, "name"));
    let ref_prefix = try_arg!(require_str(args, "reference_prefix"));
    let value_str = args["value"].as_str().unwrap_or(name);
    let show_names = args["show_pin_names"].as_bool().unwrap_or(true);
    let show_numbers = args["show_pin_numbers"].as_bool().unwrap_or(true);

    // Optional conventional body shape. `glyph` may be set at the symbol level
    // (a default for every unit) and/or per unit (overriding the default).
    let mut warnings: Vec<String> = Vec::new();
    let sym_glyph = match args["glyph"].as_str() {
        None => None,
        Some(s) => match Glyph::parse(s) {
            Some(g) => Some(g),
            None => {
                warnings.push(format!("unknown glyph '{}'; used a rectangle", s));
                None
            }
        },
    };

    // Multi-unit when `units` is a non-empty array; otherwise the single-unit
    // `pins` path. Sub-symbols are named NAME_<unit>_1; units 1..N are the
    // individual units, and shared `power_pins` become a dedicated final unit.
    let unit_objs: Vec<serde_json::Value> = args["units"].as_array().cloned().unwrap_or_default();
    let power_pins = args["power_pins"].as_array().cloned().unwrap_or_default();

    let mut units_sexp = String::new();
    let unit_count: usize;
    let ref_body: SymbolRect;
    if unit_objs.is_empty() {
        let pins_val = args["pins"].as_array().cloned().unwrap_or_default();
        // A single-unit triangular glyph (op-amp/buffer/inverter/schmitt) has no
        // room for power-pin names on its narrow apex, so if it carries power
        // pins, split them onto a dedicated rectangular power unit (like KiCAD's
        // multi-unit op-amps) instead of drawing them on the triangle.
        let split_power =
            matches!(sym_glyph, Some(g) if g.is_triangular()) && pins_val.iter().any(is_power_pin);
        if split_power {
            let signal: Vec<serde_json::Value> = pins_val
                .iter()
                .filter(|p| !is_power_pin(p))
                .cloned()
                .collect();
            let power: Vec<serde_json::Value> = pins_val
                .iter()
                .filter(|p| is_power_pin(p))
                .cloned()
                .collect();
            // Unit 1: the triangle with its signal pins.
            let (inner1, body1, warn1) = match build_symbol_unit(&signal, true, sym_glyph) {
                Ok(v) => v,
                Err(e) => {
                    return Ok(CallToolResult::error_kind(
                        crate::mcp::error::ToolErrorKind::InvalidArgument {
                            field: "pins[].type".to_string(),
                            reason: e.to_string(),
                        },
                        e.to_string(),
                    ))
                }
            };
            if let Some(w) = warn1 {
                warnings.push(w);
            }
            units_sexp.push_str(&format!("\n    (symbol \"{}_1_1\"{}\n    )", name, inner1));
            // Unit 2: a rectangular power unit.
            let power_laid = layout_power_unit(&power);
            let (inner2, _, warn2) = match build_symbol_unit(&power_laid, true, None) {
                Ok(v) => v,
                Err(e) => {
                    return Ok(CallToolResult::error_kind(
                        crate::mcp::error::ToolErrorKind::InvalidArgument {
                            field: "pins[].type".to_string(),
                            reason: e.to_string(),
                        },
                        e.to_string(),
                    ))
                }
            };
            if let Some(w) = warn2 {
                warnings.push(w);
            }
            units_sexp.push_str(&format!("\n    (symbol \"{}_2_1\"{}\n    )", name, inner2));
            unit_count = 2;
            ref_body = body1;
        } else {
            // Single unit: body + all pins live in NAME_0_1 (unchanged behavior).
            let (inner, body, warn) = match build_symbol_unit(&pins_val, true, sym_glyph) {
                Ok(v) => v,
                Err(e) => {
                    return Ok(CallToolResult::error_kind(
                        crate::mcp::error::ToolErrorKind::InvalidArgument {
                            field: "pins[].type".to_string(),
                            reason: e.to_string(),
                        },
                        e.to_string(),
                    ))
                }
            };
            if let Some(w) = warn {
                warnings.push(w);
            }
            units_sexp.push_str(&format!("\n    (symbol \"{}_0_1\"{}\n    )", name, inner));
            unit_count = 1;
            ref_body = body;
        }
    } else {
        // Multi-unit: each signal unit is NAME_1_1..NAME_N_1, and the power
        // pins (if any) become a dedicated FINAL unit rather than being drawn
        // on every unit. KiCAD's own multi-unit parts do this (e.g. 74LS00 has
        // the four gates as units 1..4 and VCC/GND as unit 5). It means the
        // power pins appear on exactly one placed unit instead of on every
        // unit, where each duplicate would otherwise need wiring to pass ERC.
        let mut first_body: SymbolRect = None;
        for (i, u) in unit_objs.iter().enumerate() {
            let unit_pins = u["pins"].as_array().cloned().unwrap_or_default();
            // A per-unit `glyph` overrides the symbol-level default.
            let unit_glyph = match u["glyph"].as_str() {
                None => sym_glyph,
                Some(s) => match Glyph::parse(s) {
                    Some(g) => Some(g),
                    None => {
                        warnings.push(format!(
                            "unit {}: unknown glyph '{}'; used a rectangle",
                            i + 1,
                            s
                        ));
                        Some(Glyph::Rectangle)
                    }
                },
            };
            let (inner, body, warn) = match build_symbol_unit(&unit_pins, true, unit_glyph) {
                Ok(v) => v,
                Err(e) => {
                    return Ok(CallToolResult::error_kind(
                        crate::mcp::error::ToolErrorKind::InvalidArgument {
                            field: "pins[].type".to_string(),
                            reason: e.to_string(),
                        },
                        e.to_string(),
                    ))
                }
            };
            if let Some(w) = warn {
                warnings.push(format!("unit {}: {}", i + 1, w));
            }
            if i == 0 {
                first_body = body;
            }
            units_sexp.push_str(&format!(
                "\n    (symbol \"{}_{}_1\"{}\n    )",
                name,
                i + 1,
                inner
            ));
        }
        let mut total = unit_objs.len();
        if !power_pins.is_empty() {
            // The power unit is always a rectangle.
            let (inner, _, _) = match build_symbol_unit(&power_pins, true, None) {
                Ok(v) => v,
                Err(e) => {
                    return Ok(CallToolResult::error_kind(
                        crate::mcp::error::ToolErrorKind::InvalidArgument {
                            field: "pins[].type".to_string(),
                            reason: e.to_string(),
                        },
                        e.to_string(),
                    ))
                }
            };
            total += 1;
            units_sexp.push_str(&format!(
                "\n    (symbol \"{}_{}_1\"{}\n    )",
                name, total, inner
            ));
        }
        unit_count = total;
        ref_body = first_body;
    }

    // Reference/value placement above/below the (first) unit body (Y-up).
    let (ref_y, value_y) = match ref_body {
        Some((_, min_y, _, max_y)) => (max_y + 2.54, min_y - 2.54),
        None => (2.54, -2.54),
    };

    let numbers_vis = if show_numbers { "" } else { " hide" };
    let names_vis = if show_names { "" } else { " hide" };

    let symbol_sexp = format!(
        "\n  (symbol \"{}\"\n    (pin_numbers{})\n    (pin_names (offset 1.016){})\n    (in_bom yes)\n    (on_board yes)\n    (property \"Reference\" \"{}\" (at 0 {:.4} 0) (effects (font (size 1.27 1.27))))\n    (property \"Value\" \"{}\" (at 0 {:.4} 0) (effects (font (size 1.27 1.27))))\n    (property \"Footprint\" \"\" (at 0 0 0) (effects (font (size 1.27 1.27)) hide))\n    (property \"Datasheet\" \"~\" (at 0 0 0) (effects (font (size 1.27 1.27)) hide)){}\n  )",
        name, numbers_vis, names_vis, ref_prefix, ref_y, value_str, value_y, units_sexp
    );

    // If file doesn't exist, create scaffold
    let content = if lib_path.exists() {
        tokio::fs::read_to_string(&lib_path).await?
    } else {
        "(kicad_symbol_lib\n  (version 20240108)\n  (generator \"konnect\")\n)\n".to_string()
    };

    // Insert before closing paren of root expression
    let insert_pos = content.rfind(')').unwrap_or(content.len());
    let new_content = format!("{}{}\n)", &content[..insert_pos], symbol_sexp);

    if let Some(parent) = lib_path.parent() {
        tokio::fs::create_dir_all(parent).await?;
    }
    write_atomic(&lib_path, &new_content)?;

    let mut result = json!({
        "success": true,
        "symbol": name,
        "library": lib_path.to_str().unwrap_or(""),
        "unit_count": unit_count,
        "power_pin_count": power_pins.len()
    });
    if !warnings.is_empty() {
        result["warnings"] = json!(warnings);
    }

    Ok(CallToolResult::text(
        serde_json::to_string(&result).unwrap(),
    ))
}

async fn handle_delete_symbol(
    args: &serde_json::Value,
    _ctx: &ToolContext,
) -> anyhow::Result<CallToolResult> {
    let lib_path = get_path(args, "library_path")?;
    let symbol_name = try_arg!(require_str(args, "symbol_name"));

    let content = tokio::fs::read_to_string(&lib_path).await?;

    // Find `  (symbol "NAME"` block
    let pat = format!(r#"  (symbol "{}""#, symbol_name);
    let start = content
        .find(&pat)
        .ok_or_else(|| anyhow::anyhow!("Symbol '{}' not found in library", symbol_name))?;

    // Walk back to find preceding newline
    let block_start = content[..start].rfind('\n').map(|i| i + 1).unwrap_or(start);

    // Walk forward to find end of block (depth count)
    let mut depth = 0i32;
    let mut end = start;
    for (i, ch) in content[start..].char_indices() {
        match ch {
            '(' => depth += 1,
            ')' => {
                depth -= 1;
                if depth == 0 {
                    end = start + i + 1;
                    break;
                }
            }
            _ => {}
        }
    }
    // Skip trailing newline
    let end = if content[end..].starts_with('\n') {
        end + 1
    } else {
        end
    };

    let new_content = format!("{}{}", &content[..block_start], &content[end..]);
    write_atomic(&lib_path, &new_content)?;

    Ok(CallToolResult::text(
        serde_json::to_string(&json!({
            "success": true,
            "deleted": symbol_name
        }))
        .unwrap(),
    ))
}

/// Extract the names of every top-level symbol defined in a `.kicad_sym`
/// library body, sorted and de-duplicated.
///
/// KiCad writes these files with CRLF line endings (on Windows) and TAB
/// indentation, so a fixed string search such as `\n  (symbol "` does not work
/// — it returned 0 symbols for every real library (KiCad 10, format version
/// 20251024). Instead we parse the S-expression structurally and read the
/// **direct** children of the `(kicad_symbol_lib …)` root whose head is
/// `symbol`. Nested unit sub-symbols (`NAME_0_1`, `NAME_1_1`, …) live one
/// level deeper, so they are excluded automatically — no name-pattern
/// heuristics required, and names containing underscores are preserved
/// verbatim.
fn top_level_symbol_names(content: &str) -> anyhow::Result<Vec<String>> {
    let root = parse_sexp(content)
        .map_err(|e| anyhow::anyhow!("failed to parse .kicad_sym library: {e}"))?;
    let mut names: Vec<String> = root
        .find_all("symbol")
        .into_iter()
        .filter_map(|sym| sym.get(1).and_then(|n| n.as_str()).map(str::to_owned))
        .collect();
    names.sort();
    names.dedup();
    Ok(names)
}

/// Resolve a symbol library nickname to an on-disk `.kicad_sym` path.
///
/// Checks the **project** table at `project_dir/sym-lib-table` first (when a
/// project dir is supplied), then the **global** sym-lib-table. Returns the first
/// entry whose nickname matches and whose URI resolved to a path at all. Both
/// tables are read with `read_flat_lib_table`, so nested `(type "Table")`
/// references are followed and `${KICAD*_DIR}` URIs are expanded.
///
/// The returned path is *not* guaranteed to exist: `expand_lib_uri` checks
/// existence only for `${KICAD*_DIR}` expansions, and takes a plain URI as
/// written. Project-first ordering matches KiCad's project override semantics.
async fn resolve_symbol_lib_path(
    nick: &str,
    project_dir: Option<&Path>,
) -> Result<PathBuf, SymbolLibPathError> {
    let mut tables = Vec::with_capacity(2);
    if let Some(pd) = project_dir {
        tables.push(pd.join("sym-lib-table"));
    }
    tables.push(global_sym_lib_table());
    // D.6.5: the nickname matching and the URI expanding are separate
    // failures, and this used to return `None` for both. A nickname whose URI
    // does not expand is passed over in favour of a later table that resolves;
    // if nothing resolves, the fact that the nickname *was* registered is what
    // gets reported.
    let mut nickname_seen = false;
    for table in tables {
        for lib in read_flat_lib_table(&table) {
            if lib["nickname"].as_str() == Some(nick) {
                nickname_seen = true;
                if let Some(path) = lib["path"].as_str() {
                    return Ok(PathBuf::from(path));
                }
            }
        }
    }
    Err(if nickname_seen {
        SymbolLibPathError::LibraryUriUnresolved {
            nickname: nick.to_string(),
        }
    } else {
        SymbolLibPathError::LibraryNotRegistered {
            nickname: nick.to_string(),
        }
    })
}

/// Why a symbol library nickname did not resolve to a path.
///
/// D.6.5: this was an `Option::None`, and the call site's message had to name
/// both possibilities at once — "not found in global or project sym-lib-table,
/// or its uri uses an unresolved env var" — because nothing downstream could
/// tell which had happened. They are separated here for the reason the prose
/// gives away: the fix for one is to register the library, and the fix for the
/// other is to set the variable its URI names.
#[derive(Debug)]
pub(crate) enum SymbolLibPathError {
    /// Neither table has an entry with this nickname.
    LibraryNotRegistered { nickname: String },
    /// A table has the nickname, but its URI expanded to no path.
    LibraryUriUnresolved { nickname: String },
}

impl SymbolLibPathError {
    fn kind(&self) -> ToolErrorKind {
        let (item_kind, nickname) = match self {
            Self::LibraryNotRegistered { nickname } => ("library", nickname),
            Self::LibraryUriUnresolved { nickname } => ("library uri", nickname),
        };
        ToolErrorKind::NotFound {
            document: "sym-lib-table".to_string(),
            item_kind: item_kind.to_string(),
            key: nickname.clone(),
            candidates: Vec::new(),
        }
    }
}

impl std::fmt::Display for SymbolLibPathError {
    fn fmt(&self, formatter: &mut std::fmt::Formatter<'_>) -> std::fmt::Result {
        match self {
            Self::LibraryNotRegistered { nickname } => write!(
                formatter,
                "Library '{nickname}' not found in the global or project sym-lib-table"
            ),
            Self::LibraryUriUnresolved { nickname } => write!(
                formatter,
                "Library '{nickname}' is registered in a sym-lib-table, but its uri \
                 resolved to no path — it most likely uses an environment \
                 variable that is not set"
            ),
        }
    }
}

impl std::error::Error for SymbolLibPathError {}
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
