nevenfo/kicad-agentic-mcp/crates/konnect-core/src/tools/design_review.rs

//! `design_review` toolset — AI-powered design audits.
//!
//! Analyzes schematic and PCB files for common design issues. Returns structured
//! findings that Claude can explain, prioritize, and suggest fixes for.
//!
//! These tools work on the S-expression files directly — no KiCAD running required.

use crate::mcp::protocol::CallToolResult;
use crate::tool;
use crate::tools::{drc_gate, get_path, invalid_arg, ToolContext, ToolDef};
use konnect_schematic_editor as cse;
use konnect_sexp::{
    parser::parse_sexp,
    schematic::{
        extract_lib_pins_for_unit, extract_symbol_instances, find_lib_symbol, pin_endpoint,
        read_schematic,
    },
};
use serde_json::json;
use std::collections::HashSet;
use tracing::info;

// ─── Tool definitions ─────────────────────────────────────────────────────────

pub fn tools() -> Vec<ToolDef> {
    vec![
        tool!(
            "audit_decoupling",
            "Check that all ICs have appropriate decoupling capacitors. Finds power pins \
             without nearby capacitors and flags wrong values. The #1 most common PCB design mistake.",
            json!({
                "type": "object",
                "properties": {
                    "schematic": { "type": "string", "description": "Path to .kicad_sch file" },
                    "board": { "type": "string", "description": "Path to .kicad_pcb file (optional, for distance check)" },
                    "max_distance_mm": {
                        "type": "number",
                        "description": "Max allowed distance from power pin to decoupling cap on PCB (mm)",
                        "default": 5.0
                    }
                },
                "required": ["schematic"]
            }),
            |args, ctx| async move { handle_audit_decoupling(args, ctx).await }
        ),
        tool!(
            "audit_connections",
            "Check for common connection mistakes: missing pull-ups on I2C/reset, \
             missing series resistors on LEDs, floating inputs, outputs shorted together.",
            json!({
                "type": "object",
                "properties": {
                    "schematic": { "type": "string", "description": "Path to .kicad_sch file" }
                },
                "required": ["schematic"]
            }),
            |args, ctx| async move { handle_audit_connections(args, ctx).await }
        ),
        tool!(
            "audit_power_rails",
            "Check power rail integrity: missing bulk capacitance, no test points on power rails, \
             voltage regulator output caps missing.",
            json!({
                "type": "object",
                "properties": {
                    "schematic": { "type": "string", "description": "Path to .kicad_sch file" }
                },
                "required": ["schematic"]
            }),
            |args, ctx| async move { handle_audit_power_rails(args, ctx).await }
        ),
        tool!(
            "audit_manufacturing",
            "DFM checks for the configured fab house: component spacing, silkscreen overlap, \
             via-in-pad, acid traps, board outline issues.",
            json!({
                "type": "object",
                "properties": {
                    "board": { "type": "string", "description": "Path to .kicad_pcb file" },
                    "fab_house": {
                        "type": "string",
                        "description": "Target manufacturer: 'jlcpcb' (default), 'pcbway', 'oshpark'",
                        "default": "jlcpcb"
                    }
                },
                "required": ["board"]
            }),
            |args, ctx| async move { handle_audit_manufacturing(args, ctx).await }
        ),
        tool!(
            "run_design_review",
            "Run all available audit checks and produce a consolidated design review report. \
             This is the tool to call when the user asks 'is my board ready?' or 'review my design'.",
            json!({
                "type": "object",
                "properties": {
                    "schematic": { "type": "string", "description": "Path to .kicad_sch file" },
                    "board": { "type": "string", "description": "Path to .kicad_pcb file (optional)" },
                    "severity_filter": {
                        "type": "string",
                        "description": "Minimum severity to include: 'error', 'warning' (default), 'info'",
                        "default": "warning"
                    }
                },
                // P.6.9.16: `schematic` alone was never the contract. A
                // board-only review is intended and tested
                // (`a_board_review_without_drc_evidence_cannot_look_good`),
                // so listing `schematic` as required made the dispatch refuse
                // a legitimate call. The real rule is the same disjunction
                // `get_datasheet_url` publishes: one of the two, or both.
                "required": [],
                "anyOf": [
                    { "required": ["schematic"] },
                    { "required": ["board"] }
                ]
            }),
            |args, ctx| async move { handle_run_design_review(args, ctx).await }
        ),
        tool!(
            "check_bom_health",
            "Analyze the BOM for supply chain risks: parts with no MPN, lifecycle warnings, \
             low stock, parts not available from preferred distributors.",
            json!({
                "type": "object",
                "properties": {
                    "schematic": { "type": "string", "description": "Path to .kicad_sch file" }
                },
                "required": ["schematic"]
            }),
            |args, ctx| async move { handle_check_bom_health(args, ctx).await }
        ),
    ]
}

// ─── Audit types ─────────────────────────────────────────────────────────────

#[derive(Debug, Clone, serde::Serialize)]
struct AuditFinding {
    severity: &'static str, // "error", "warning", "info"
    category: &'static str, // "decoupling", "connection", "power", "dfm", "bom"
    component: Option<String>,
    issue: String,
    recommendation: String,
}

// ─── Decoupling audit ────────────────────────────────────────────────────────

async fn handle_audit_decoupling(
    args: &serde_json::Value,
    _ctx: &ToolContext,
) -> anyhow::Result<CallToolResult> {
    let sch_path = get_path(args, "schematic")?;
    info!(schematic = %sch_path.display(), "[BETA] Running decoupling audit");
    let (content, tree) = read_schematic(&sch_path)?;

    let instances = extract_symbol_instances(&tree);
    let lib_syms = tree
        .find("lib_symbols")
        .map(|n| n.find_all("symbol"))
        .unwrap_or_default();

    let mut findings = Vec::new();
    let mut pass_count = 0;
    let mut total_power_pins = 0;

    // Collect all capacitor references and their net connections
    let cap_nets = collect_capacitor_nets(&content, &instances, &lib_syms);

    // For each IC (non-passive, non-connector component), check power pins
    for inst in &instances {
        let lib_sym = find_lib_symbol(&lib_syms, inst);
        let lib_sym = match lib_sym {
            Some(s) => s,
            None => continue,
        };

        let pins = extract_lib_pins_for_unit(lib_sym, inst.unit);
        let is_passive = inst.lib_id.contains("R_")
            || inst.lib_id.contains("C_")
            || inst.lib_id.contains("L_")
            || inst.lib_id.contains("D_");
        let is_connector = inst.lib_id.contains("Conn_")
            || inst.lib_id.contains("Jack")
            || inst.lib_id.contains("Header");

        if is_passive || is_connector {
            continue;
        }

        // Find power pins (power_in type, or named VCC/VDD/VBUS/3V3/etc.)
        for pin in &pins {
            let is_power_pin = is_power_pin_name(&pin.name);
            if !is_power_pin {
                continue;
            }
            total_power_pins += 1;

            // Get the endpoint position of this power pin
            let (px, py) = pin_endpoint(pin, inst.pin_transform());

            // Check if there's a capacitor connected to a net that this pin is on
            let pin_net = find_net_at_point(&content, px, py);

            let has_decoupling = if let Some(ref net) = pin_net {
                cap_nets.contains(net)
            } else {
                false
            };

            if has_decoupling {
                pass_count += 1;
            } else {
                findings.push(AuditFinding {
                    severity: "error",
                    category: "decoupling",
                    component: Some(inst.reference.clone()),
                    issue: format!(
                        "Power pin '{}' on {} has no decoupling capacitor{}",
                        pin.name,
                        inst.reference,
                        pin_net
                            .as_ref()
                            .map(|n| format!(" (net: {})", n))
                            .unwrap_or_default()
                    ),
                    recommendation: format!(
                        "Add a 100nF ceramic capacitor close to {} pin '{}'",
                        inst.reference, pin.name
                    ),
                });
            }
        }
    }

    Ok(CallToolResult::text(
        serde_json::to_string(&json!({
            "audit": "decoupling",
            "findings": findings,
            "pass_count": pass_count,
            "total_power_pins": total_power_pins,
            "summary": format!(
                "{}/{} power pins have decoupling. {} issues found.",
                pass_count, total_power_pins, findings.len()
            )
        }))
        .unwrap(),
    ))
}

// ─── Connection audit ────────────────────────────────────────────────────────

async fn handle_audit_connections(
    args: &serde_json::Value,
    _ctx: &ToolContext,
) -> anyhow::Result<CallToolResult> {
    let sch_path = get_path(args, "schematic")?;
    info!(schematic = %sch_path.display(), "[BETA] Running connection audit");
    let (content, tree) = read_schematic(&sch_path)?;

    let instances = extract_symbol_instances(&tree);
    let lib_syms = tree
        .find("lib_symbols")
        .map(|n| n.find_all("symbol"))
        .unwrap_or_default();

    let mut findings = Vec::new();

    for inst in &instances {
        let lib_sym = match find_lib_symbol(&lib_syms, inst) {
            Some(s) => s,
            None => continue,
        };

        let pins = extract_lib_pins_for_unit(lib_sym, inst.unit);

        // Check for I2C pull-ups
        if has_i2c_pins(&pins) {
            let sda_pin = pins.iter().find(|p| p.name.to_uppercase().contains("SDA"));
            let scl_pin = pins.iter().find(|p| p.name.to_uppercase().contains("SCL"));

            for (pin_name, pin) in [("SDA", sda_pin), ("SCL", scl_pin)] {
                if let Some(pin) = pin {
                    let (px, py) = pin_endpoint(pin, inst.pin_transform());
                    let net = find_net_at_point(&content, px, py);
                    if let Some(ref net_name) = net {
                        if !has_pull_up_on_net(&content, &instances, &lib_syms, net_name) {
                            findings.push(AuditFinding {
                                severity: "warning",
                                category: "connection",
                                component: Some(inst.reference.clone()),
                                issue: format!(
                                    "I2C {} pin on {} (net: {}) has no pull-up resistor",
                                    pin_name, inst.reference, net_name
                                ),
                                recommendation: format!(
                                    "Add a 4.7k pull-up resistor from {} to VCC",
                                    net_name
                                ),
                            });
                        }
                    }
                }
            }
        }

        // Check for reset pins without pull-up
        for pin in &pins {
            let name_upper = pin.name.to_uppercase();
            if (name_upper.contains("RESET") || name_upper.contains("NRST") || name_upper == "RST")
                && !name_upper.contains("OUT")
            {
                let (px, py) = pin_endpoint(pin, inst.pin_transform());
                let net = find_net_at_point(&content, px, py);
                if let Some(ref net_name) = net {
                    if !has_pull_up_on_net(&content, &instances, &lib_syms, net_name) {
                        findings.push(AuditFinding {
                            severity: "warning",
                            category: "connection",
                            component: Some(inst.reference.clone()),
                            issue: format!(
                                "Reset pin '{}' on {} (net: {}) has no pull-up resistor",
                                pin.name, inst.reference, net_name
                            ),
                            recommendation: format!(
                                "Add a 10k pull-up resistor from {} to VCC with 100nF cap to GND",
                                net_name
                            ),
                        });
                    }
                }
            }
        }
    }

    Ok(CallToolResult::text(
        serde_json::to_string(&json!({
            "audit": "connections",
            "findings": findings,
            "summary": format!("{} connection issues found.", findings.len())
        }))
        .unwrap(),
    ))
}

// ─── Power rail audit ────────────────────────────────────────────────────────

async fn handle_audit_power_rails(
    args: &serde_json::Value,
    _ctx: &ToolContext,
) -> anyhow::Result<CallToolResult> {
    let sch_path = get_path(args, "schematic")?;
    info!(schematic = %sch_path.display(), "[BETA] Running power rail audit");
    let (content, tree) = read_schematic(&sch_path)?;

    let instances = extract_symbol_instances(&tree);
    let lib_syms = tree
        .find("lib_symbols")
        .map(|n| n.find_all("symbol"))
        .unwrap_or_default();

    let mut findings = Vec::new();

    // Find all power nets (from power symbols and labels)
    let power_nets = collect_power_nets(&content);

    // Check each power net for bulk capacitance
    let cap_nets = collect_capacitor_nets(&content, &instances, &lib_syms);
    let bulk_cap_nets = collect_bulk_cap_nets(&content, &instances, &lib_syms);

    for net in &power_nets {
        if net.to_uppercase().contains("GND") || net.to_uppercase().contains("VSS") {
            continue; // Ground nets don't need caps
        }

        if !cap_nets.contains(net.as_str()) {
            findings.push(AuditFinding {
                severity: "error",
                category: "power",
                component: None,
                issue: format!("Power rail '{}' has no decoupling capacitors", net),
                recommendation: format!("Add at least one 100nF ceramic cap on the '{}' rail", net),
            });
        } else if !bulk_cap_nets.contains(net.as_str()) {
            findings.push(AuditFinding {
                severity: "warning",
                category: "power",
                component: None,
                issue: format!("Power rail '{}' has no bulk capacitance (>= 10uF)", net),
                recommendation: format!(
                    "Add a 10uF or larger electrolytic/ceramic cap on the '{}' rail near the power source",
                    net
                ),
            });
        }
    }

    // Check for test points on power rails
    let test_point_nets = collect_test_point_nets(&content, &instances);
    for net in &power_nets {
        if net.to_uppercase().contains("GND") {
            continue;
        }
        if !test_point_nets.contains(net.as_str()) {
            findings.push(AuditFinding {
                severity: "info",
                category: "power",
                component: None,
                issue: format!("Power rail '{}' has no test point", net),
                recommendation: format!("Add a test point on '{}' for debugging", net),
            });
        }
    }

    Ok(CallToolResult::text(
        serde_json::to_string(&json!({
            "audit": "power_rails",
            "power_nets": power_nets,
            "findings": findings,
            "summary": format!("{} power rail issues found across {} rails.", findings.len(), power_nets.len())
        }))
        .unwrap(),
    ))
}

// ─── Manufacturing audit ─────────────────────────────────────────────────────

async fn handle_audit_manufacturing(
    args: &serde_json::Value,
    _ctx: &ToolContext,
) -> anyhow::Result<CallToolResult> {
    let board_path = get_path(args, "board")?;
    let fab_house = args["fab_house"].as_str().unwrap_or("jlcpcb");
    info!(board = %board_path.display(), fab_house = %fab_house, "[BETA] Running DFM audit");

    let content = tokio::fs::read_to_string(&board_path).await?;
    let tree = parse_sexp(&content)?;

    let mut findings = Vec::new();

    // Get fab constraints for the target fab house
    let (min_trace, _min_space, _min_drill, _min_annular) = match fab_house {
        "jlcpcb" => (0.127, 0.127, 0.3, 0.13), // JLCPCB standard capability
        "pcbway" => (0.1, 0.1, 0.2, 0.1),
        "oshpark" => (0.152, 0.152, 0.254, 0.127), // 6mil/6mil
        _ => (0.15, 0.15, 0.3, 0.13),
    };

    // Check board outline exists
    let has_edge_cuts = content.contains("Edge.Cuts");
    if !has_edge_cuts {
        findings.push(AuditFinding {
            severity: "error",
            category: "dfm",
            component: None,
            issue: "No board outline found (Edge.Cuts layer is empty)".to_string(),
            recommendation: "Add a board outline on the Edge.Cuts layer using add_board_outline"
                .to_string(),
        });
    }

    // Check for footprints on both sides (assembly complexity)
    let fps = tree.find_all("footprint");
    let mut front_count = 0;
    let mut back_count = 0;
    for fp in &fps {
        if let Some(layer) = fp
            .find("layer")
            .and_then(|l| l.get(1))
            .and_then(|l| l.as_str())
        {
            if layer == "F.Cu" {
                front_count += 1;
            }
            if layer == "B.Cu" {
                back_count += 1;
            }
        }
    }
    if back_count > 0 && front_count > 0 {
        findings.push(AuditFinding {
            severity: "info",
            category: "dfm",
            component: None,
            issue: format!(
                "Components on both sides: {} front, {} back. This requires dual-side assembly.",
                front_count, back_count
            ),
            recommendation: "Verify your fab house supports dual-side assembly. JLCPCB charges extra for back-side SMT.".to_string(),
        });
    }

    // Check for silkscreen overlapping pads
    let silkscreen_issues = check_silkscreen_overlap(&content, &tree);
    findings.extend(silkscreen_issues);

    // Check design rules in setup section
    let _setup = tree.find("setup");
    if let Some(_setup) = _setup {
        // Check trace width
        if let Some(trace_min) = find_design_rule_value(&content, "min_trace_width") {
            if trace_min < min_trace {
                findings.push(AuditFinding {
                    severity: "error",
                    category: "dfm",
                    component: None,
                    issue: format!(
                        "Minimum trace width ({:.3}mm) is below {} capability ({:.3}mm)",
                        trace_min, fab_house, min_trace
                    ),
                    recommendation: format!(
                        "Increase minimum trace width to at least {:.3}mm",
                        min_trace
                    ),
                });
            }
        }
    }

    Ok(CallToolResult::text(
        serde_json::to_string(&json!({
            "audit": "manufacturing",
            "fab_house": fab_house,
            "components": { "front": front_count, "back": back_count },
            "findings": findings,
            "summary": format!("{} DFM issues found for {}.", findings.len(), fab_house)
        }))
        .unwrap(),
    ))
}

// ─── Unified design review ───────────────────────────────────────────────────

async fn handle_run_design_review(
    args: &serde_json::Value,
    ctx: &ToolContext,
) -> anyhow::Result<CallToolResult> {
    // P.6.9.16: both halves of this tool's contract were wrong, in opposite
    // directions. `run_design_review_with` only *tests*
    // `args["schematic"].is_string()` / `args["board"].is_string()`, so a call
    // carrying neither quietly skipped every audit and came back "LOOKS GOOD"
    // with nothing reviewed — reachable through `kicad_invoke`, whose batch
    // entries skip `first_missing_required` (D131). Meanwhile the schema said
    // `required: ["schematic"]`, which made the dispatch refuse a board-only
    // review that `a_board_review_without_drc_evidence_cannot_look_good`
    // proves is intended. The contract is `schematic` *or* `board`; the schema
    // now says so via `anyOf`, and this guard closes the case that `anyOf`
    // cannot reach on its own — a batch entry with neither.
    if !args["schematic"].is_string() && !args["board"].is_string() {
        return Ok(invalid_arg(
            "schematic",
            "a review needs something to review: pass 'schematic', 'board', or both",
        ));
    }
    // A review with no board in it never had anything to run DRC on, and must
    // come back exactly as it did before DRC entered the verdict.
    let drc = match get_path(args, "board") {
        Ok(board) if args["board"].is_string() => {
            Some(drc_gate::gather(&ctx.config.kicad_cli, &board, false).await)
        }
        _ => None,
    };
    run_design_review_with(args, ctx, drc.as_ref()).await
}

/// The review itself, against a DRC report someone else gathered — split from
/// the handler for the same reason as `validate_for_manufacturing_with`.
async fn run_design_review_with(
    args: &serde_json::Value,
    ctx: &ToolContext,
    drc: Option<&drc_gate::DrcEvidence>,
) -> anyhow::Result<CallToolResult> {
    info!("[BETA] Running full design review");
    let severity_filter = args["severity_filter"].as_str().unwrap_or("warning");
    let min_rank = match severity_filter {
        "error" => 2,
        "warning" => 1,
        _ => 0,
    };

    let mut all_findings: Vec<serde_json::Value> = Vec::new();
    // Each entry is (audit name, findings), where every finding already
    // carries a "sheet" key naming the file it came from — a finding with no
    // sheet key would be indistinguishable from one that was actually checked
    // on every sheet.
    let mut audit_results: Vec<(&str, Vec<serde_json::Value>)> = Vec::new();

    // P.6.8.4: a schematic with sub-sheets used to be audited on its root
    // file alone — the four schematic audits never followed a `(sheet …)`
    // reference, so a defect living only on a sub-sheet was invisible to
    // `run_design_review` no matter how loud it was. Every reachable sheet
    // gets its own pass now, and every sheet a `(sheet …)` reference named
    // but this walk could not load is reported rather than silently skipped.
    let mut sheets_reachable = 0usize;
    let mut sheets_audited = 0usize;
    let mut unaudited_sheets: Vec<serde_json::Value> = Vec::new();
    if let Some(schematic_arg) = args["schematic"].as_str() {
        let root = std::path::Path::new(schematic_arg);
        let walk = super::reachable_sheets(root);
        sheets_reachable = walk.sheets.len() + walk.unloadable.len();
        sheets_audited = walk.sheets.len();
        for (path, reason) in &walk.unloadable {
            unaudited_sheets.push(json!({
                "sheet": path.display().to_string(),
                "reason": reason,
            }));
        }

        let mut decoupling_findings = Vec::new();
        let mut connections_findings = Vec::new();
        let mut power_findings = Vec::new();
        let mut bom_findings = Vec::new();
        for sheet in &walk.sheets {
            let sheet_label = sheet.display().to_string();
            let mut sheet_args = args.clone();
            sheet_args["schematic"] = json!(sheet_label);

            let decoupling = handle_audit_decoupling(&sheet_args, ctx).await?;
            decoupling_findings.extend(tag_with_sheet(extract_findings(&decoupling), &sheet_label));

            let connections = handle_audit_connections(&sheet_args, ctx).await?;
            connections_findings
                .extend(tag_with_sheet(extract_findings(&connections), &sheet_label));

            let power = handle_audit_power_rails(&sheet_args, ctx).await?;
            power_findings.extend(tag_with_sheet(extract_findings(&power), &sheet_label));

            let bom = handle_check_bom_health(&sheet_args, ctx).await?;
            bom_findings.extend(tag_with_sheet(extract_findings(&bom), &sheet_label));
        }
        audit_results.push(("decoupling", decoupling_findings));
        audit_results.push(("connections", connections_findings));
        audit_results.push(("power_rails", power_findings));
        audit_results.push(("bom_health", bom_findings));
    }

    // Run PCB audits
    if args["board"].is_string() {
        let dfm = handle_audit_manufacturing(args, ctx).await?;
        audit_results.push(("manufacturing", extract_findings(&dfm)));
    }

    // DRC — the one audit that reads the board the way the fab will, and the
    // only one that can tell a board routed all but one net from a finished
    // one.
    let mut drc_summary = serde_json::Value::Null;
    let mut drc_incomplete = false;
    if let Some(evidence) = drc {
        let gate = drc_gate::assess(evidence);
        drc_summary = gate.summary;
        drc_incomplete = gate.incomplete;
        audit_results.push((
            "drc",
            gate.findings
                .iter()
                .map(|f| {
                    json!({
                        "severity": f.severity,
                        "category": "drc",
                        "component": serde_json::Value::Null,
                        "issue": f.issue,
                        "recommendation": f.fix,
                    })
                })
                .collect(),
        ));
    }

    // Collect and filter findings
    let mut error_count = 0;
    let mut warning_count = 0;
    let mut info_count = 0;

    for (audit_name, findings) in &audit_results {
        for finding in findings {
            let sev = finding["severity"].as_str().unwrap_or("info");
            let rank = match sev {
                "error" => {
                    error_count += 1;
                    2
                }
                "warning" => {
                    warning_count += 1;
                    1
                }
                _ => {
                    info_count += 1;
                    0
                }
            };
            if rank >= min_rank {
                let mut f = finding.clone();
                f["audit"] = json!(audit_name);
                all_findings.push(f);
            }
        }
    }

    // Sort by severity (errors first)
    all_findings.sort_by(|a, b| {
        let rank_a = match a["severity"].as_str().unwrap_or("") {
            "error" => 0,
            "warning" => 1,
            _ => 2,
        };
        let rank_b = match b["severity"].as_str().unwrap_or("") {
            "error" => 0,
            "warning" => 1,
            _ => 2,
        };
        rank_a.cmp(&rank_b)
    });

    let verdict = if error_count > 0 {
        "NOT READY — critical issues must be fixed before manufacturing".to_string()
    } else if !unaudited_sheets.is_empty() {
        // Nothing found on the sheets that were audited — but at least one
        // sheet this hierarchy references was never looked at, so absence of
        // findings there proves nothing. Name it, the way `drc_incomplete`
        // names the missing DRC pass below.
        let names: Vec<String> = unaudited_sheets
            .iter()
            .map(|u| {
                format!(
                    "{} ({})",
                    u["sheet"].as_str().unwrap_or("?"),
                    u["reason"].as_str().unwrap_or("could not be loaded")
                )
            })
            .collect();
        format!("INCOMPLETE — sheet(s) not audited: {}", names.join(", "))
    } else if drc_incomplete {
        // Nothing found — but a pass of DRC never ran, so this review has not
        // seen the board the fab will see. "LOOKS GOOD" here would be a
        // clearance nobody earned.
        "INCOMPLETE — DRC did not run, so the board is unverified".to_string()
    } else if warning_count > 0 {
        "NEEDS ATTENTION — review warnings before manufacturing".to_string()
    } else {
        "LOOKS GOOD — no critical issues found".to_string()
    };

    let mut review = json!({
        "verdict": verdict,
        "errors": error_count,
        "warnings": warning_count,
        "info": info_count,
        "severity_filter": severity_filter,
        "findings": all_findings
    });
    if args["schematic"].is_string() {
        // Reported next to `drc` for the same reason `drc_incomplete` earned
        // a verdict of its own: a caller reading only `verdict` and `findings`
        // must still be able to tell a clean sheet from one nobody checked.
        review["schematic_coverage"] = json!({
            "sheets_reachable": sheets_reachable,
            "sheets_audited": sheets_audited,
            "unaudited": unaudited_sheets,
        });
    }
    if drc.is_some() {
        // `null` when DRC could not run — never zeroed counters.
        review["drc"] = drc_summary;
    }

    Ok(CallToolResult::text(
        serde_json::to_string(&json!({ "design_review": review })).unwrap(),
    ))
}

// ─── BOM health check ───────────────────────────────────────────────────────

async fn handle_check_bom_health(
    args: &serde_json::Value,
    _ctx: &ToolContext,
) -> anyhow::Result<CallToolResult> {
    let sch_path = get_path(args, "schematic")?;
    info!(schematic = %sch_path.display(), "[BETA] Running BOM health check");

    let sch = cse::Schematic::load(&sch_path)
        .map_err(|e| anyhow::anyhow!("Failed to load schematic: {e}"))?;

    let mut findings = Vec::new();
    let mut total_components = 0;
    let mut missing_mpn = 0;
    let mut missing_footprint = 0;
    let mut missing_value = 0;

    for sym in sch.symbols.iter() {
        let reference = match sym.reference() {
            Some(r) => r,
            None => continue,
        };

        // Skip power symbols and sub-units
        if reference.starts_with('#') {
            continue;
        }
        total_components += 1;

        let value = sym.value_str().unwrap_or("");

        // Check for missing value
        if value.is_empty() || value == "~" {
            missing_value += 1;
            findings.push(AuditFinding {
                severity: "warning",
                category: "bom",
                component: Some(reference.to_owned()),
                issue: format!("{} has no value assigned", reference),
                recommendation: "Set the component value (e.g., '100nF', '10k', 'STM32F411')"
                    .to_string(),
            });
        }

        // Check for missing footprint
        let footprint = sym.footprint().unwrap_or("");
        if footprint.is_empty() || footprint == "~" {
            missing_footprint += 1;
            findings.push(AuditFinding {
                severity: "error",
                category: "bom",
                component: Some(reference.to_owned()),
                issue: format!("{} ({}) has no footprint assigned", reference, value),
                recommendation: "Assign a footprint before PCB layout".to_string(),
            });
        }

        // Check for missing MPN (per-component check via properties)
        let has_mpn = sym.property("MPN").is_some() || sym.property("LCSC").is_some();
        if reference.starts_with('U') && !has_mpn {
            missing_mpn += 1;
            findings.push(AuditFinding {
                severity: "warning",
                category: "bom",
                component: Some(reference.to_owned()),
                issue: format!(
                    "{} ({}) has no MPN (Manufacturer Part Number)",
                    reference, value
                ),
                recommendation:
                    "Add an MPN property for accurate BOM generation and supply chain lookup"
                        .to_string(),
            });
        }
    }

    Ok(CallToolResult::text(
        serde_json::to_string(&json!({
            "audit": "bom_health",
            "total_components": total_components,
            "missing_mpn": missing_mpn,
            "missing_footprint": missing_footprint,
            "missing_value": missing_value,
            "findings": findings,
            "summary": format!(
                "{} components, {} issues. {} missing footprints, {} missing values.",
                total_components, findings.len(), missing_footprint, missing_value
            )
        }))
        .unwrap(),
    ))
}

// ─── Helper functions ────────────────────────────────────────────────────────

fn is_power_pin_name(name: &str) -> bool {
    let upper = name.to_uppercase();
    upper.starts_with("VCC")
        || upper.starts_with("VDD")
        || upper.starts_with("VBUS")
        || upper.starts_with("V+")
        || upper.starts_with("VIN")
        || upper.starts_with("3V3")
        || upper.starts_with("5V")
        || upper.starts_with("1V")
        || upper.starts_with("2V")
        || upper == "AVCC"
        || upper == "AVDD"
        || upper == "DVCC"
        || upper == "DVDD"
        || upper.starts_with("VCAP")
        || upper.starts_with("VREF")
        || upper.contains("POWER")
        || upper.contains("PWR")
}

fn has_i2c_pins(pins: &[konnect_sexp::schematic::LibPin]) -> bool {
    let names: Vec<String> = pins.iter().map(|p| p.name.to_uppercase()).collect();
    names.iter().any(|n| n.contains("SDA")) && names.iter().any(|n| n.contains("SCL"))
}

/// Collect nets that have at least one capacitor connected.
fn collect_capacitor_nets(
    content: &str,
    instances: &[konnect_sexp::schematic::SymbolInstance],
    lib_syms: &[&konnect_sexp::parser::SexpNode],
) -> HashSet<String> {
    let mut nets = HashSet::new();
    for inst in instances {
        if !inst.reference.starts_with('C') || inst.reference.starts_with("CN") {
            continue; // Only capacitors
        }
        let lib_sym = find_lib_symbol(lib_syms, inst);
        if let Some(sym) = lib_sym {
            let pins = extract_lib_pins_for_unit(sym, inst.unit);
            for pin in &pins {
                let (px, py) = pin_endpoint(pin, inst.pin_transform());
                if let Some(net) = find_net_at_point(content, px, py) {
                    nets.insert(net);
                }
            }
        }
    }
    nets
}

/// Collect nets that have bulk capacitors (>= 10uF).
fn collect_bulk_cap_nets(
    content: &str,
    instances: &[konnect_sexp::schematic::SymbolInstance],
    lib_syms: &[&konnect_sexp::parser::SexpNode],
) -> HashSet<String> {
    let mut nets = HashSet::new();
    for inst in instances {
        if !inst.reference.starts_with('C') || inst.reference.starts_with("CN") {
            continue;
        }
        // Check if value suggests bulk cap (>= 10uF)
        let val_upper = inst.value.to_uppercase();
        let is_bulk = val_upper.contains("10U")
            || val_upper.contains("22U")
            || val_upper.contains("47U")
            || val_upper.contains("100U")
            || val_upper.contains("220U")
            || val_upper.contains("470U")
            || val_upper.contains("1000U")
            || val_upper.contains("10µ")
            || val_upper.contains("22µ")
            || val_upper.contains("47µ");

        if !is_bulk {
            continue;
        }

        let lib_sym = find_lib_symbol(lib_syms, inst);
        if let Some(sym) = lib_sym {
            let pins = extract_lib_pins_for_unit(sym, inst.unit);
            for pin in &pins {
                let (px, py) = pin_endpoint(pin, inst.pin_transform());
                if let Some(net) = find_net_at_point(content, px, py) {
                    nets.insert(net);
                }
            }
        }
    }
    nets
}

/// Collect power net names from power symbols and labels.
fn collect_power_nets(content: &str) -> Vec<String> {
    let mut nets = HashSet::new();

    // Find power symbols (reference starts with #PWR)
    // and net labels with power-like names
    let _search = content.as_bytes();
    let mut pos = 0;
    while pos < content.len() {
        // Look for plain labels with power-ish names. KiCAD's tag is `label`;
        // `net_label` is not in the schematic format and matched nothing.
        if let Some(label_pos) = content[pos..].find("(label \"") {
            let abs = pos + label_pos + 8;
            if let Some(end) = content[abs..].find('"') {
                let name = &content[abs..abs + end];
                if is_power_net_name(name) {
                    nets.insert(name.to_string());
                }
            }
            pos = abs + 1;
        } else {
            break;
        }
    }

    // Also check global labels
    pos = 0;
    while pos < content.len() {
        if let Some(label_pos) = content[pos..].find("(global_label \"") {
            let abs = pos + label_pos + 15;
            if let Some(end) = content[abs..].find('"') {
                let name = &content[abs..abs + end];
                if is_power_net_name(name) {
                    nets.insert(name.to_string());
                }
            }
            pos = abs + 1;
        } else {
            break;
        }
    }

    // Also check power_port symbols
    pos = 0;
    while pos < content.len() {
        if let Some(pp_pos) = content[pos..].find("(power_port \"") {
            let abs = pos + pp_pos + 13;
            if let Some(end) = content[abs..].find('"') {
                nets.insert(content[abs..abs + end].to_string());
            }
            pos = abs + 1;
        } else {
            break;
        }
    }

    nets.into_iter().collect()
}

fn is_power_net_name(name: &str) -> bool {
    let upper = name.to_uppercase();
    upper.starts_with("VCC")
        || upper.starts_with("VDD")
        || upper.starts_with("3V3")
        || upper.starts_with("5V")
        || upper.starts_with("12V")
        || upper.starts_with("VBUS")
        || upper == "GND"
        || upper == "DGND"
        || upper == "AGND"
        || upper.starts_with("+")
        || upper.starts_with("V+")
}

/// Collect nets that have test points connected.
fn collect_test_point_nets(
    _content: &str,
    instances: &[konnect_sexp::schematic::SymbolInstance],
) -> HashSet<String> {
    let nets = HashSet::new();
    for inst in instances {
        if inst.reference.starts_with("TP") || inst.value.to_uppercase().contains("TESTPOINT") {
            // Find the net this test point is on (simplified: look for nearby label)
            // A proper implementation would trace the wire
        }
    }
    nets
}

fn has_pull_up_on_net(
    content: &str,
    instances: &[konnect_sexp::schematic::SymbolInstance],
    lib_syms: &[&konnect_sexp::parser::SexpNode],
    net_name: &str,
) -> bool {
    // Check if any resistor has one pin on this net and the other on a power net
    for inst in instances {
        if !inst.reference.starts_with('R') {
            continue;
        }
        let lib_sym = find_lib_symbol(lib_syms, inst);
        if let Some(sym) = lib_sym {
            let pins = extract_lib_pins_for_unit(sym, inst.unit);
            let pin_nets: Vec<Option<String>> = pins
                .iter()
                .map(|p| {
                    let (px, py) = pin_endpoint(p, inst.pin_transform());
                    find_net_at_point(content, px, py)
                })
                .collect();

            let has_target_net = pin_nets.iter().any(|n| n.as_deref() == Some(net_name));
            let has_power_net = pin_nets.iter().any(|n| {
                n.as_ref()
                    .map(|name| is_power_net_name(name))
                    .unwrap_or(false)
            });
            if has_target_net && has_power_net {
                return true;
            }
        }
    }
    false
}

/// Find the net name at a given schematic point by checking nearby labels and wires.
fn find_net_at_point(content: &str, x: f64, y: f64) -> Option<String> {
    // Check plain labels near this point (KiCAD's tag is `label`, not
    // `net_label` — the latter matched nothing in any real schematic).
    let tolerance = 0.5; // mm
    let mut search = 0;
    while let Some(pos) = content[search..].find("(label \"") {
        let abs = search + pos;
        let after = &content[abs + 8..];
        let name_end = after.find('"')?;
        let name = &after[..name_end];

        // Find the (at X Y) in this label
        let block_end = content[abs..].find(")\n").unwrap_or(200) + abs;
        let block = &content[abs..block_end.min(content.len())];
        if let Some(at_pos) = block.find("(at ") {
            let at_str = &block[at_pos + 4..];
            let parts: Vec<&str> = at_str.split([' ', ')']).take(2).collect();
            if parts.len() >= 2 {
                if let (Ok(lx), Ok(ly)) = (parts[0].parse::<f64>(), parts[1].parse::<f64>()) {
                    if (lx - x).abs() < tolerance && (ly - y).abs() < tolerance {
                        return Some(name.to_string());
                    }
                }
            }
        }
        search = abs + 1;
    }

    // Also check global_labels
    search = 0;
    while let Some(pos) = content[search..].find("(global_label \"") {
        let abs = search + pos;
        let after = &content[abs + 15..];
        let name_end = after.find('"')?;
        let name = &after[..name_end];

        let block_end = content[abs..].find(")\n").unwrap_or(200) + abs;
        let block = &content[abs..block_end.min(content.len())];
        if let Some(at_pos) = block.find("(at ") {
            let at_str = &block[at_pos + 4..];
            let parts: Vec<&str> = at_str.split([' ', ')']).take(2).collect();
            if parts.len() >= 2 {
                if let (Ok(lx), Ok(ly)) = (parts[0].parse::<f64>(), parts[1].parse::<f64>()) {
                    if (lx - x).abs() < tolerance && (ly - y).abs() < tolerance {
                        return Some(name.to_string());
                    }
                }
            }
        }
        search = abs + 1;
    }

    None
}

fn check_silkscreen_overlap(
    _content: &str,
    tree: &konnect_sexp::parser::SexpNode,
) -> Vec<AuditFinding> {
    // Simplified check: look for footprints that are very close together
    // A full implementation would check bounding boxes of silkscreen elements
    let fps = tree.find_all("footprint");
    let mut findings = Vec::new();

    let positions: Vec<(String, f64, f64)> = fps
        .iter()
        .filter_map(|fp| {
            let reference = fp
                .find_all("property")
                .iter()
                .find(|p| p.get(1).and_then(|n| n.as_str()) == Some("Reference"))
                .and_then(|p| p.get(2))
                .and_then(|n| n.as_str())?
                .to_string();
            let at = fp.find("at")?;
            let x = at.get_f64(1)?;
            let y = at.get_f64(2)?;
            Some((reference, x, y))
        })
        .collect();

    for i in 0..positions.len() {
        for j in (i + 1)..positions.len() {
            let (ref ref_a, xa, ya) = positions[i];
            let (ref ref_b, xb, yb) = positions[j];
            let dist = ((xa - xb).powi(2) + (ya - yb).powi(2)).sqrt();
            if dist < 1.0 {
                // Less than 1mm apart
                findings.push(AuditFinding {
                    severity: "warning",
                    category: "dfm",
                    component: Some(format!("{}, {}", ref_a, ref_b)),
                    issue: format!(
                        "{} and {} are only {:.2}mm apart — possible silkscreen overlap or assembly issue",
                        ref_a, ref_b, dist
                    ),
                    recommendation: "Increase spacing between components to at least 1mm for reliable assembly".to_string(),
                });
            }
        }
    }
    findings
}

fn find_design_rule_value(content: &str, rule_name: &str) -> Option<f64> {
    let pat = format!("({} ", rule_name);
    let pos = content.find(&pat)?;
    let after = &content[pos + pat.len()..];
    let end = after.find(')')?;
    after[..end].trim().parse().ok()
}

/// Stamp every finding with the sheet it was found on — the piece of context
/// that turns "a decoupling cap is missing somewhere" into "on `power.kicad_sch`".
fn tag_with_sheet(
    mut findings: Vec<serde_json::Value>,
    sheet_label: &str,
) -> Vec<serde_json::Value> {
    for f in &mut findings {
        f["sheet"] = json!(sheet_label);
    }
    findings
}

fn extract_findings(result: &CallToolResult) -> Vec<serde_json::Value> {
    if let Some(crate::mcp::protocol::ToolContent::Text { text }) = result.content.first() {
        if let Ok(parsed) = serde_json::from_str::<serde_json::Value>(text) {
            if let Some(findings) = parsed["findings"].as_array() {
                return findings.clone();
            }
        }
    }
    Vec::new()
}

#[cfg(test)]
mod drc_in_the_review_tests {
    use super::*;
    use crate::router::ToolRouter;
    use crate::tools::cli::{DrcCategory, DrcReport, DrcViolation};
    use crate::tools::drc_gate::DrcEvidence;
    use crate::tools::ServerConfig;
    use std::sync::Arc;

    fn test_ctx() -> ToolContext {
        ToolContext::new(
            ServerConfig {
                kicad_cli: String::new(),
                kicad_binary: String::new(),
                ipc_address: String::new(),
                project_dir: None,
                jlcpcb_db_path: None,
                auto_load_toolsets: false,
                mode: kam_state::OperatingMode::Write,
            },
            Arc::new(ToolRouter::new()),
        )
    }

    async fn review(drc: DrcEvidence) -> serde_json::Value {
        let dir = tempfile::tempdir().unwrap();
        let path = dir.path().join("board.kicad_pcb");
        std::fs::write(
            &path,
            "(kicad_pcb (version 20260206) (layers (44 \"Edge.Cuts\" user)))\n",
        )
        .unwrap();
        let result = run_design_review_with(
            &json!({ "board": path.display().to_string() }),
            &test_ctx(),
            Some(&drc),
        )
        .await
        .unwrap();
        let crate::mcp::protocol::ToolContent::Text { text } = &result.content[0] else {
            panic!("expected text");
        };
        let parsed: serde_json::Value = serde_json::from_str(text).unwrap();
        parsed["design_review"].clone()
    }

    /// One net left on the ratsnest is one DRC error, and one DRC error is a
    /// review that does not say the design is fine.
    #[tokio::test]
    async fn an_unconnected_net_lands_in_the_review_as_an_error() {
        let out = review(DrcEvidence::Measured(DrcReport {
            violations: Some(vec![]),
            unconnected_items: Some(vec![DrcViolation {
                severity: "error".to_string(),
                description: "Missing connection between items: Pad 2 [SCL] on C1".to_string(),
                pos: None,
                rule: Some("unconnected_items".to_string()),
                category: DrcCategory::UnconnectedItems,
                items: Vec::new(),
            }]),
            schematic_parity: Some(vec![]),
            schematic_parity_diagnostic: None,
        }))
        .await;
        assert_eq!(out["errors"], json!(1), "{out}");
        assert!(
            out["verdict"].as_str().unwrap().starts_with("NOT READY"),
            "{out}"
        );
        assert_eq!(out["drc"]["unconnected_items"], json!(1), "{out}");
        assert!(
            out["findings"]
                .as_array()
                .unwrap()
                .iter()
                .any(|f| f["audit"] == "drc"),
            "{out}"
        );
    }

    /// A DRC that ran every pass and found nothing is the one case where the
    /// review may still say so.
    #[tokio::test]
    async fn a_complete_and_clean_drc_leaves_the_verdict_alone() {
        let out = review(DrcEvidence::Measured(DrcReport {
            violations: Some(vec![]),
            unconnected_items: Some(vec![]),
            schematic_parity: Some(vec![]),
            schematic_parity_diagnostic: None,
        }))
        .await;
        assert!(
            out["verdict"].as_str().unwrap().starts_with("LOOKS GOOD"),
            "{out}"
        );
        assert_eq!(out["drc"]["errors"], json!(0), "{out}");
    }
}
