nevenfo/kicad-agentic-mcp/crates/konnect-core/src/tools/mod.rs

//! Tool trait definitions, ToolContext, and all toolset modules.

pub mod cli;
pub mod config;
pub mod design_review;
pub(crate) mod drc_gate;
pub mod footprint_graphics;
pub mod graph;
pub mod integration;
mod ipc_boundary;
pub(crate) mod ipc_queue;
pub mod library;
pub mod manufacturing;
pub mod pcb_board;
pub mod pcb_components;
pub mod pcb_export;
pub mod pcb_routing;
pub(crate) mod pcb_sync;
pub mod plan;
pub mod project;
pub mod sch_analysis;
pub mod sch_batch;
pub mod sch_bridge;
pub mod sch_buses;
pub mod sch_components;
pub mod sch_export;
pub mod sch_hierarchy;
pub mod sch_wiring;
pub mod schematic_builder;
pub mod svg_import;
pub mod task;
pub mod templates;
pub mod verification;

use crate::mcp::protocol::{CallToolResult, McpToolDescription};
use crate::router::ToolRouter;
use serde_json::Value;
use std::future::Future;
use std::pin::Pin;
use std::sync::Arc;

// ─── Tool Handler Type ────────────────────────────────────────────────────────

pub type ToolHandlerFn = Arc<
    dyn Fn(
            &Value,
            Arc<ToolContext>,
        ) -> Pin<Box<dyn Future<Output = anyhow::Result<CallToolResult>> + Send>>
        + Send
        + Sync,
>;

// ─── ToolDef ─────────────────────────────────────────────────────────────────

/// A single tool definition: schema + async handler.
#[derive(Clone)]
pub struct ToolDef {
    pub name: &'static str,
    pub description: &'static str,
    pub input_schema: Value,
    pub handler: ToolHandlerFn,
}

impl ToolDef {
    pub fn to_mcp_description(&self) -> McpToolDescription {
        let effect = crate::capability::tool_effect(self.name);
        McpToolDescription {
            name: self.name.to_string(),
            description: self.description.to_string(),
            input_schema: self.input_schema.clone(),
            annotations: Some(crate::capability::tool_annotations(effect, self.name)),
        }
    }
}

// Implement Debug manually because handler is not Debug
impl std::fmt::Debug for ToolDef {
    fn fmt(&self, f: &mut std::fmt::Formatter<'_>) -> std::fmt::Result {
        f.debug_struct("ToolDef")
            .field("name", &self.name)
            .field("description", &self.description)
            .finish()
    }
}

// ─── ToolContext ──────────────────────────────────────────────────────────────

/// Shared context passed to every tool handler.
/// Contains config, the tool router, lazily-initialized KiCAD clients, and the
/// per-call observer (used by `get_recent_calls` / `server_stats` meta-tools).
pub struct ToolContext {
    pub config: ServerConfig,
    /// Editor context carried by the KiCad executable-plugin action. External
    /// MCP launches use `Auto`, which probes both handlers and requires one
    /// unambiguous `AS_OK` response.
    pub document_context: konnect_ipc::DocumentContext,
    pub router: Arc<ToolRouter>,
    pub observer: crate::observability::CallObserver,
    /// In-memory TTL cache for repeated JLCPCB parts-database queries.
    pub jlcpcb_cache: QueryCache,
    /// Results of batches that carried an `operation_id`, so a client retrying
    /// after a timeout gets the first outcome back instead of applying it
    /// twice. Shared for the life of the server, like the observer.
    pub idempotency: Arc<kam_state::IdempotencyLedger<serde_json::Value>>,
    /// Artefacts a reply refers to instead of carrying: the full change list
    /// behind `kicad://diff/N`, served over MCP `resources/read`. Shared for
    /// the life of the server so a handle stays resolvable across calls.
    pub evidence: Arc<kam_evidence::EvidenceStore>,
    /// ERC/DRC verdicts remembered against the document revision they were
    /// computed for, so a batch can report `ERC 4 -> 0` without running the
    /// validator twice.
    pub validation: Arc<crate::evidence::validators::Cache>,
    /// Objectives, constraints and what has already been tried — the part of a
    /// session that must outlive any one model's context window.
    pub tasks: Arc<kam_state::TaskStore>,
    /// Explicit Agent-only entry point. Direct KiCAD tools never consult it.
    pub supervisor: Arc<kam_runtime::Supervisor>,
    /// Deterministic companion to the Agent supervisor. Only validator-derived
    /// verdicts from this path enter `TaskState::verified_facts`.
    pub verification_agent: Arc<crate::verification_agent::VerificationAgent>,
    /// Built graphs of a project's documents, cached by content revision so a
    /// `graph_*` call reuses the last build when nothing on disk moved.
    pub graph: Arc<crate::graph::GraphStore>,
    /// The process's operating mode (plan.md D.8): orthogonal to which
    /// toolset is loaded, this is what decides whether a `Write`-effect call
    /// is allowed to run at all. Fixed at startup from `ServerConfig::mode`;
    /// the only public mutator is `kam_state::ModeGuard::restrict_to`, which
    /// can only lower it (D69) — see `mcp::handler::McpHandler::dispatch_tool`
    /// and `router::meta_tools::handle_kicad_invoke` for the two places it is
    /// enforced.
    pub mode: Arc<kam_state::ModeGuard>,
    /// Append-only record of what `kicad_invoke` batches did (plan.md D.7.1).
    /// `None` for `ToolContext::new` — the in-memory-only constructor used by
    /// most tests, which must stay free of IO — and for a server whose
    /// journal directory could not be opened; either way a batch still runs,
    /// it just leaves no journal entry behind it.
    pub journal: Option<Arc<kam_state::RunJournal>>,
}

impl ToolContext {
    /// Construct a context with an in-memory-only observer (no JSONL). Used by
    /// tests and by callers that don't need persistent call logs.
    pub fn new(config: ServerConfig, router: Arc<ToolRouter>) -> Self {
        let mode = Arc::new(kam_state::ModeGuard::new(config.mode));
        let tasks = Arc::new(kam_state::TaskStore::default());
        let evidence = Arc::new(kam_evidence::EvidenceStore::default());
        let validation = Arc::new(crate::evidence::validators::Cache::default());
        let verification_agent = Arc::new(crate::verification_agent::VerificationAgent::new(
            tasks.clone(),
            validation.clone(),
            evidence.clone(),
            config.kicad_cli.clone(),
        ));
        ToolContext {
            config,
            document_context: konnect_ipc::DocumentContext::Auto,
            router,
            observer: crate::observability::CallObserver::new(None),
            jlcpcb_cache: QueryCache::default(),
            idempotency: Arc::default(),
            evidence,
            validation,
            supervisor: Arc::new(kam_runtime::Supervisor::new(tasks.clone(), None)),
            verification_agent,
            tasks,
            graph: Arc::default(),
            mode,
            journal: None,
        }
    }

    /// Construct a context with a specific observer — wired in by `McpHandler`
    /// so the JSONL log and in-memory ring are shared across all tool calls.
    pub fn new_with_observer(
        config: ServerConfig,
        router: Arc<ToolRouter>,
        observer: crate::observability::CallObserver,
    ) -> Self {
        Self::new_with_observer_and_provider(config, router, observer, None)
    }

    /// Construct a context with an explicitly configured Agent-only provider.
    /// Direct tools retain no path to it; only `kicad_agent` uses the supervisor.
    pub fn new_with_observer_and_provider(
        config: ServerConfig,
        router: Arc<ToolRouter>,
        observer: crate::observability::CallObserver,
        provider: Option<Arc<dyn kam_llm::Provider>>,
    ) -> Self {
        Self::new_with_observer_provider_and_document_context(
            config,
            router,
            observer,
            provider,
            konnect_ipc::DocumentContext::Auto,
        )
    }

    pub fn new_with_observer_provider_and_document_context(
        config: ServerConfig,
        router: Arc<ToolRouter>,
        observer: crate::observability::CallObserver,
        provider: Option<Arc<dyn kam_llm::Provider>>,
        document_context: konnect_ipc::DocumentContext,
    ) -> Self {
        let mode = Arc::new(kam_state::ModeGuard::new(config.mode));
        let tasks = Arc::new(kam_state::TaskStore::default());
        let evidence = Arc::new(kam_evidence::EvidenceStore::default());
        let validation = Arc::new(crate::evidence::validators::Cache::default());
        let verification_agent = Arc::new(crate::verification_agent::VerificationAgent::new(
            tasks.clone(),
            validation.clone(),
            evidence.clone(),
            config.kicad_cli.clone(),
        ));
        // Best-effort: a journal that fails to open is an audit trail the
        // server runs without, never a reason to refuse to start.
        let journal = match kam_state::RunJournal::open(crate::observability::journal_dir()) {
            Ok(journal) => Some(Arc::new(journal)),
            Err(e) => {
                tracing::warn!("[journal] could not open run journal: {e}");
                None
            }
        };
        ToolContext {
            config,
            document_context,
            router,
            observer,
            jlcpcb_cache: QueryCache::default(),
            idempotency: Arc::default(),
            evidence,
            validation,
            supervisor: Arc::new(kam_runtime::Supervisor::new(tasks.clone(), provider)),
            verification_agent,
            tasks,
            graph: Arc::default(),
            mode,
            journal,
        }
    }
}

// ─── QueryCache ───────────────────────────────────────────────────────────────

/// A small in-memory, TTL-based cache for repeated read-only query results
/// (JSON values keyed by a caller-constructed string). One instance lives on
/// `ToolContext` for the life of the server, shared across all tool calls.
pub struct QueryCache {
    ttl: std::time::Duration,
    entries: std::sync::Mutex<std::collections::HashMap<String, (Value, std::time::Instant)>>,
}

impl QueryCache {
    pub fn new(ttl: std::time::Duration) -> Self {
        QueryCache {
            ttl,
            entries: std::sync::Mutex::new(std::collections::HashMap::new()),
        }
    }

    /// Returns a cached value for `key` if present and not yet expired.
    pub fn get(&self, key: &str) -> Option<Value> {
        let entries = self.entries.lock().unwrap();
        entries.get(key).and_then(|(value, inserted_at)| {
            if inserted_at.elapsed() < self.ttl {
                Some(value.clone())
            } else {
                None
            }
        })
    }

    /// Stores `value` under `key`, overwriting any existing (possibly expired) entry.
    pub fn put(&self, key: String, value: Value) {
        let mut entries = self.entries.lock().unwrap();
        entries.insert(key, (value, std::time::Instant::now()));
    }
}

impl Default for QueryCache {
    /// 5-minute TTL — long enough to skip redundant re-queries within a single
    /// design session, short enough that a `download_jlcpcb_database` refresh
    /// is reflected without needing an explicit cache-invalidation hook.
    fn default() -> Self {
        QueryCache::new(std::time::Duration::from_secs(300))
    }
}

// ─── ServerConfig ─────────────────────────────────────────────────────────────

/// Subset of the server configuration relevant to tool execution.
/// This is the config that flows from `konnect::Config` into the core crate.
#[derive(Debug, Clone)]
pub struct ServerConfig {
    pub kicad_cli: String,
    pub kicad_binary: String,
    pub ipc_address: String,
    pub project_dir: Option<std::path::PathBuf>,
    pub jlcpcb_db_path: Option<std::path::PathBuf>,
    /// Auto-load a tool's toolset on call instead of returning
    /// `toolset_not_loaded`. Off by default (see `konnect::Config::auto_load_toolsets`).
    pub auto_load_toolsets: bool,
    /// Process-wide execution-risk mode (plan.md D.8), orthogonal to
    /// toolset loading. `Write` (the default) is today's unrestricted
    /// behaviour; `ReadOnly` refuses every `Effect::Write` tool before its
    /// handler runs. Set once from `KONNECT_MODE` at startup
    /// (`konnect::config`) and never elevated afterward (D69).
    pub mode: kam_state::OperatingMode,
}

impl Default for ServerConfig {
    /// `Write`: matches every field's implicit prior default, so a caller
    /// that does not set `mode` gets today's unrestricted behaviour, not a
    /// silently locked-down server.
    fn default() -> Self {
        ServerConfig {
            kicad_cli: String::new(),
            kicad_binary: String::new(),
            ipc_address: String::new(),
            project_dir: None,
            jlcpcb_db_path: None,
            auto_load_toolsets: false,
            mode: kam_state::OperatingMode::Write,
        }
    }
}

#[cfg(test)]
mod query_cache_tests {
    use super::*;
    use serde_json::json;

    #[test]
    fn miss_on_unknown_key() {
        let cache = QueryCache::new(std::time::Duration::from_secs(60));
        assert!(cache.get("nope").is_none());
    }

    #[test]
    fn put_then_get_roundtrips() {
        let cache = QueryCache::new(std::time::Duration::from_secs(60));
        cache.put("key".to_string(), json!({ "count": 3 }));
        assert_eq!(cache.get("key"), Some(json!({ "count": 3 })));
    }

    #[test]
    fn entry_expires_after_ttl() {
        let cache = QueryCache::new(std::time::Duration::from_millis(10));
        cache.put("key".to_string(), json!("value"));
        assert_eq!(cache.get("key"), Some(json!("value")));
        std::thread::sleep(std::time::Duration::from_millis(20));
        assert!(cache.get("key").is_none());
    }

    #[test]
    fn put_overwrites_existing_entry() {
        let cache = QueryCache::new(std::time::Duration::from_secs(60));
        cache.put("key".to_string(), json!("first"));
        cache.put("key".to_string(), json!("second"));
        assert_eq!(cache.get("key"), Some(json!("second")));
    }
}

// ─── Helper macro for defining tools ─────────────────────────────────────────

/// Shorthand for building a ToolDef with a typed async handler function.
///
/// Usage:
/// ```rust,ignore
/// tool!(
///     "tool_name",
///     "Description of what it does.",
///     json_schema,        // serde_json::Value
///     |args, ctx| async move {
///         // handler body
///         Ok(CallToolResult::text("done"))
///     }
/// )
/// ```
#[macro_export]
macro_rules! tool {
    ($name:expr, $desc:expr, $schema:expr, $handler:expr) => {{
        let h: $crate::tools::ToolHandlerFn = std::sync::Arc::new(move |args, ctx| {
            let args = args.clone();
            let ctx = ctx.clone();
            Box::pin(async move { ($handler)(&args, &*ctx).await })
        });
        $crate::tools::ToolDef {
            name: $name,
            description: $desc,
            input_schema: $schema,
            handler: h,
        }
    }};
}

/// Unwrap a `require_*` helper inside a handler that returns
/// `anyhow::Result<CallToolResult>`, returning the structured error result to
/// the caller unchanged.
///
/// The pattern this replaces was `require_str(args, "k").map_err(|e|
/// anyhow::anyhow!("{:?}", e))?`, which Debug-formats the structured error into
/// an opaque string and then re-wraps it as `handler_error`. The client sees
/// `Tool error: CallToolResult { content: [Text { text: "{\"error\":..." }] }`
/// instead of a matchable `invalid_argument` with a `field`, so error matching,
/// dedup and recovery all break on exactly the calls that need them most.
///
/// ```ignore
/// let lib_id = try_arg!(require_str(args, "lib_id"));
/// ```
#[macro_export]
macro_rules! try_arg {
    ($e:expr) => {
        match $e {
            Ok(value) => value,
            Err(result) => return Ok(result),
        }
    };
}

// ─── Argument helpers ─────────────────────────────────────────────────────────

/// Build a structured `InvalidArgument` CallToolResult. Used by the
/// `require_*` helpers so every handler that uses them emits structured
/// errors the client / observer can match on — no per-handler change needed.
pub(crate) fn invalid_arg(field: &str, reason: &str) -> CallToolResult {
    CallToolResult::error_kind(
        crate::mcp::error::ToolErrorKind::InvalidArgument {
            field: field.to_string(),
            reason: reason.to_string(),
        },
        format!("Argument '{}' is invalid: {}", field, reason),
    )
}

/// The first key a schema's `"required"` list names that the call did not
/// supply, if any.
///
/// Presence only — no type, no format, no value constraint: that is what the
/// `require_*` helpers below still do, from inside the handler, where the type
/// a key must have is known. This is the floor under them, applied at dispatch
/// so a tool whose handler forgot to check (or checks late, after it has
/// already read a file) cannot run on an incomplete call.
///
/// An explicit `null` is missing. A client that serialises its absent
/// optionals as `null` is saying the same thing as one that omits the key, and
/// no `require_*` helper accepts `null` either.
pub(crate) fn first_missing_required(schema: &Value, args: &Value) -> Option<String> {
    schema
        .get("required")?
        .as_array()?
        .iter()
        .filter_map(Value::as_str)
        .find(|key| args.get(*key).unwrap_or(&Value::Null).is_null())
        .map(str::to_string)
}

/// Extract a required string argument, returning a structured
/// `InvalidArgument` error result if missing or not a string.
pub fn require_str<'a>(args: &'a Value, key: &str) -> Result<&'a str, CallToolResult> {
    args[key]
        .as_str()
        .ok_or_else(|| invalid_arg(key, "missing or not a string"))
}

/// Extract an optional string argument.
pub fn opt_str<'a>(args: &'a Value, key: &str) -> Option<&'a str> {
    args[key].as_str()
}

/// Extract a required f64 argument. Returns a structured `InvalidArgument`
/// error result if missing or not a number.
pub fn require_f64(args: &Value, key: &str) -> Result<f64, CallToolResult> {
    args[key]
        .as_f64()
        .ok_or_else(|| invalid_arg(key, "missing or not a number"))
}

/// Extract an optional f64.
pub fn opt_f64(args: &Value, key: &str) -> Option<f64> {
    args[key].as_f64()
}

/// Extract a required array argument. Returns a structured `InvalidArgument`
/// error result if missing or not an array.
///
/// An explicitly empty array is a legitimate answer — "export no layers", "a
/// footprint with no pads" — and is returned as an empty slice. Only absence
/// (or a non-array) is refused, because that is the caller who never said.
/// The borrowed slice, rather than an owned `Vec`, keeps the callers that only
/// iterate from cloning the whole payload.
pub fn require_array<'a>(args: &'a Value, key: &str) -> Result<&'a [Value], CallToolResult> {
    args[key]
        .as_array()
        .map(|a| a.as_slice())
        .ok_or_else(|| invalid_arg(key, "missing or not an array"))
}

/// Extract a required unsigned integer argument. Returns a structured
/// `InvalidArgument` error result if missing, not a number, or negative /
/// fractional — `serde_json`'s `as_u64` already rejects all three.
pub fn require_u64(args: &Value, key: &str) -> Result<u64, CallToolResult> {
    args[key]
        .as_u64()
        .ok_or_else(|| invalid_arg(key, "missing or not a non-negative integer"))
}

/// Extract a required path string and return it as a PathBuf, using
/// `anyhow::Error`. Use this variant with `?` inside handlers that return
/// `anyhow::Result`.
///
/// The absence is carried as a typed [`crate::mcp::error::MissingArgument`] in
/// the error chain, which
/// [`crate::mcp::error::ToolErrorKind::from_anyhow`] downcasts back into the
/// same `InvalidArgument` the `require_*` helpers return. Which of the two
/// helpers a handler was written with is an accident of its author; the
/// vocabulary a caller sees must not depend on it.
///
/// Only absence. A path that is present but leads nowhere stays whatever the
/// tool's own attempt to use it produced.
pub fn get_path(args: &Value, key: &str) -> anyhow::Result<std::path::PathBuf> {
    let s = args[key].as_str().ok_or_else(|| {
        anyhow::Error::new(crate::mcp::error::MissingArgument {
            key: key.to_string(),
        })
    })?;
    Ok(std::path::PathBuf::from(s))
}

/// How a zone must name `net_name` on this board, or the tool error to return.
///
/// The two board forms disagree about more than the id — see
/// [`konnect_sexp::net::NetRef::zone_tokens`] — and a net a legacy board does
/// not declare is refused here rather than written as id 0. Id 0 is the
/// unconnected pseudo-net: a pour attached to it is electrically orphaned, and
/// the tool used to report that as a success.
pub(crate) fn zone_net_ref(
    tree: &konnect_sexp::SexpNode,
    net_name: &str,
) -> Result<konnect_sexp::net::NetRef, CallToolResult> {
    konnect_sexp::net::net_ref_for_write(tree, net_name).map_err(|why| {
        CallToolResult::error_kind(
            crate::mcp::error::ToolErrorKind::InvalidArgument {
                field: "net_name".to_string(),
                reason: why.to_string(),
            },
            format!("Cannot place a zone on '{net_name}': {why}"),
        )
    })
}

/// Project name used in symbol/sheet `(instances (project "..." ...))` entries:
/// the schematic's file stem, matching what eeschema writes when it saves a
/// standalone root sheet.
pub fn project_name_for(sch_path: &std::path::Path) -> String {
    sch_path
        .file_stem()
        .and_then(|s| s.to_str())
        .unwrap_or("")
        .to_string()
}

/// Minimal valid blank schematic, with a freshly generated root `(uuid ...)`.
/// The root UUID is mandatory: KiCAD's netlister resolves symbol instance
/// paths against it and silently forms no wire-only nets when it's missing.
pub fn blank_schematic_template() -> String {
    konnect_sexp::schematic::format_blank_schematic()
}

/// Snap `(x, y)` to the schematic grid (see [`konnect_sexp::geometry::SCHEMATIC_GRID_MM`])
/// and report whether the snap moved the point.
///
/// Every tool that writes a placement coordinate into a `.kicad_sch` file
/// (component, power symbol, label, junction, no-connect, sheet, sheet pin,
/// text…) must go through this single helper — see E6: `add_power_symbol`
/// used to write coordinates verbatim while `add_schematic_component` snapped
/// to the 1.27mm grid, so a power symbol and a resistor placed at the same
/// nominal (x, y) ended up up to 0.635mm apart, `kicad-cli sch erc` reporting
/// "Pin not connected" with no tool ever flagging the mismatch.
///
/// A tool must not silently lie about what it wrote. When the input was
/// already on-grid, snapping is a no-op and nothing needs reporting. When it
/// moved the point, the returned `requested` value must be surfaced in the
/// tool's JSON result (typically as a `"requested": {"x":.., "y":..}` field
/// alongside the actually-written `x`/`y`) so the caller can see the point
/// was moved instead of discovering it later as an ERC failure.
pub fn snap_reporting(x: f64, y: f64) -> ((f64, f64), Option<serde_json::Value>) {
    let (sx, sy) =
        konnect_sexp::geometry::snap_point(x, y, konnect_sexp::geometry::SCHEMATIC_GRID_MM);
    if (sx - x).abs() > 1e-9 || (sy - y).abs() > 1e-9 {
        ((sx, sy), Some(serde_json::json!({ "x": x, "y": y })))
    } else {
        ((sx, sy), None)
    }
}

/// [`snap_reporting`], except that a point already sitting on a placed pin is
/// left exactly where it is (P.6.8.9).
///
/// The grid snap exists to rescue a caller who derived a coordinate loosely
/// (E6). A pin's own position needs no rescuing, and 7.6 % of them cannot
/// survive one: measured over the KiCad 10 demo corpus, **3 670 of 48 068**
/// placed pin endpoints do not sit on the 1.27 mm grid — a symbol placed
/// off-grid (127 of 6 447 placements) or a pin whose length is not a grid
/// multiple puts them there. Snapping such a point moves it up to 0.635 mm
/// off the pin, and what gets written is a wire beside the pin, a junction
/// beside the pin, or a no-connect that marks nothing — each reported as a
/// success.
///
/// `pins` is the caller's already-computed [`all_pin_endpoints`]: every site
/// that uses this either had that list in hand already or needs it for its own
/// junction pass, so nothing here re-parses a sheet.
///
/// Tolerance 0.01, the same one `add_pin_midwire_junctions` and
/// [`pin_outward_at`] compare points with.
pub(crate) fn snap_unless_pin(
    pins: &[(f64, f64)],
    x: f64,
    y: f64,
) -> ((f64, f64), Option<serde_json::Value>) {
    use konnect_sexp::geometry::points_coincident;
    if pins
        .iter()
        .any(|(px, py)| points_coincident(*px, *py, x, y, 0.01))
    {
        return ((x, y), None);
    }
    snap_reporting(x, y)
}

/// Where a sheet sits in its project, as the `(instances …)` block needs it.
///
/// Both halves of that block belong to the **root** sheet, not to the file
/// being written into: the project name is the one the `.kicad_pro` carries,
/// and the path starts at the root's uuid. On a root sheet the two coincide,
/// which is why deriving them from the file's own stem and uuid looked right
/// for so long; on a child sheet they name a project and a path KiCad matches
/// against nothing, and every symbol placed there reads as unannotated.
pub struct SheetInstanceContext {
    /// The `.kicad_pro`'s stem.
    pub project_name: String,
    /// One `"/<root-uuid>/<sheet-uuid>[/<sheet-uuid>…]"` per placement of this
    /// sheet in the hierarchy. A sheet instantiated twice — KiCad's own
    /// `complex_hierarchy` does exactly that with `ampli_ht.kicad_sch` — needs
    /// an entry for each, or the symbol is annotated in one instance and
    /// invisible in the other.
    pub paths: Vec<String>,
}

/// Resolve `sch_path`'s place in its project, or `None` when it cannot be
/// resolved and the caller must fall back to standalone behaviour.
///
/// `None` covers: a root sheet (it sits beside its own `.kicad_pro`), a
/// schematic belonging to no project, a directory holding several projects, a
/// root that cannot be read or carries no uuid, and a sheet that does not
/// appear anywhere in that root's tree. Every one of those is a case where a
/// guess would be worse than today's behaviour.
///
/// The walk is depth-bounded and tracks visited files, like every other
/// hierarchy walk here: a sheet may reference a file that references it back.
pub fn sheet_instance_context(sch_path: &std::path::Path) -> Option<SheetInstanceContext> {
    use crate::tools::sch_export::{project_root_schematic, same_file};

    // A file beside its own `.kicad_pro` is a root: today's derivation is
    // already right for it, and `ensure_root_uuid` can repair a missing uuid,
    // which this function deliberately does not do.
    if sch_path.with_extension("kicad_pro").is_file() {
        return None;
    }
    let dir = sch_path
        .parent()
        .unwrap_or_else(|| std::path::Path::new("."));
    let root = project_root_schematic(dir)?;
    if same_file(&root, sch_path) {
        return None;
    }
    let project_name = root.file_stem()?.to_str()?.to_string();
    let root_sch = konnect_schematic_editor::Schematic::load(&root).ok()?;
    let root_uuid = root_sch.uuid.clone()?;

    let mut paths = Vec::new();
    let mut visited = std::collections::HashSet::new();
    collect_sheet_paths(
        &root,
        sch_path,
        &format!("/{root_uuid}"),
        0,
        &mut visited,
        &mut paths,
    );
    if paths.is_empty() {
        return None;
    }
    // A file reachable by several routes must be written in a stable order, or
    // two identical calls produce two different files.
    paths.sort();
    paths.dedup();
    Some(SheetInstanceContext {
        project_name,
        paths,
    })
}

/// Append, to `out`, the instance path of every placement of `target` beneath
/// `sheet` — whose own path is `prefix`.
fn collect_sheet_paths(
    sheet: &std::path::Path,
    target: &std::path::Path,
    prefix: &str,
    depth: usize,
    visited: &mut std::collections::HashSet<std::path::PathBuf>,
    out: &mut Vec<String>,
) {
    use crate::tools::sch_export::{canonical, same_file};

    if depth > crate::tools::sch_hierarchy::MAX_HIERARCHY_DEPTH {
        return;
    }
    if !visited.insert(canonical(sheet)) {
        return;
    }
    let Ok(sch) = konnect_schematic_editor::Schematic::load(sheet) else {
        return;
    };
    let dir = sheet.parent().unwrap_or_else(|| std::path::Path::new("."));
    for child_sheet in sch.sheets.iter() {
        let child = dir.join(child_sheet.file());
        let child_path = format!("{prefix}/{}", child_sheet.uuid);
        if same_file(&child, target) {
            out.push(child_path.clone());
        }
        // Not `else`: a sheet can be both a placement of the target and a
        // parent of another placement of it further down.
        collect_sheet_paths(&child, target, &child_path, depth + 1, visited, out);
    }
    // A file reached through one branch may sit under another as well, so it
    // must not stay marked once this branch is done.
    visited.remove(&canonical(sheet));
}

/// Every file reachable from `root` by following `(sheet …)` references, plus
/// every reference this walk could not follow.
///
/// The third walker of this repo's schematic hierarchy, after
/// `sch_hierarchy::build_hierarchy_node` and `collect_sheet_paths` above —
/// this one exists so `design_review`'s audits can be run once per reachable
/// file instead of once on whatever single path a caller happened to pass, and
/// so `sch_export::sheet_tree_contains` can ask the same question ("is this
/// file in that tree?") without its own copy of the walk.
pub(crate) struct SheetWalk {
    /// Root first, then every child sheet in the order this walk first found
    /// it. No duplicates, even for a sheet instantiated more than once.
    pub sheets: Vec<std::path::PathBuf>,
    /// A `(sheet …)` reference this walk could not follow, with why: the file
    /// is missing, unreadable, or failed to parse. The path is the one the
    /// referencing sheet named, not a resolved one — there is nothing to
    /// resolve it against.
    pub unloadable: Vec<(std::path::PathBuf, String)>,
}

/// Walk the schematic hierarchy rooted at `root`. See [`SheetWalk`].
pub(crate) fn reachable_sheets(root: &std::path::Path) -> SheetWalk {
    let mut sheets = Vec::new();
    let mut unloadable = Vec::new();
    let mut visited = std::collections::HashSet::new();
    walk_reachable_sheets(root, 0, &mut visited, &mut sheets, &mut unloadable);
    SheetWalk { sheets, unloadable }
}

fn walk_reachable_sheets(
    file: &std::path::Path,
    depth: usize,
    visited: &mut std::collections::HashSet<std::path::PathBuf>,
    sheets: &mut Vec<std::path::PathBuf>,
    unloadable: &mut Vec<(std::path::PathBuf, String)>,
) {
    use crate::tools::sch_export::canonical;

    if depth > crate::tools::sch_hierarchy::MAX_HIERARCHY_DEPTH {
        return;
    }
    if !visited.insert(canonical(file)) {
        return;
    }
    match konnect_schematic_editor::Schematic::load(file) {
        Ok(sch) => {
            sheets.push(file.to_path_buf());
            let dir = file.parent().unwrap_or_else(|| std::path::Path::new("."));
            for child_sheet in sch.sheets.iter() {
                let child = dir.join(child_sheet.file());
                walk_reachable_sheets(&child, depth + 1, visited, sheets, unloadable);
            }
        }
        Err(e) => unloadable.push((file.to_path_buf(), e.to_string())),
    }
    // A file reached through one branch may sit under another as well, so it
    // must not stay marked once this branch is done — same reasoning as
    // `collect_sheet_paths`.
    visited.remove(&canonical(file));
}

/// The project name and instance paths a symbol placed in `sch_path` must be
/// written with.
///
/// One call site's worth of the answer to "where does this sheet live": it
/// resolves the sheet's real place in its project via
/// [`sheet_instance_context`], and falls back to the standalone derivation —
/// this file's own stem and uuid — when it cannot be resolved. `sch` is only
/// touched on that fallback, where [`ensure_root_uuid`] may assign a uuid to a
/// file that predates Konnect writing them.
pub fn instance_targets(
    sch_path: &std::path::Path,
    sch: &mut konnect_schematic_editor::Schematic,
) -> (String, Vec<String>) {
    match sheet_instance_context(sch_path) {
        Some(ctx) => (ctx.project_name, ctx.paths),
        None => {
            let root_uuid = ensure_root_uuid(sch);
            (project_name_for(sch_path), vec![format!("/{root_uuid}")])
        }
    }
}

/// Root UUID of a loaded schematic, assigning a fresh one when the file
/// predates Konnect writing root UUIDs — the file is repaired on its next
/// overwrite. Instance paths are built as "/<root-uuid>[/<sheet-uuid>…]".
pub fn ensure_root_uuid(sch: &mut konnect_schematic_editor::Schematic) -> String {
    match &sch.uuid {
        Some(u) => u.clone(),
        None => {
            let u = konnect_sexp::writer::new_uuid();
            sch.uuid = Some(u.clone());
            u
        }
    }
}

/// One placed pin: the instance it belongs to, where its connection point
/// actually lands on the sheet, and the placement origin (the instance's own
/// `(at …)`) that connection point was transformed from.
///
/// The single definition of "the pins this schematic really has": unit-aware
/// (a multi-unit symbol declares different pins per unit, P.6.8.1) and
/// transformed by the placement, so nothing downstream re-derives either.
/// Moved here from `sch_analysis` (D136, P.6.8.5): `all_pin_endpoints` below
/// was the same "for each instance, for each pin of its unit" loop as
/// `placed_pins`, kept as a second copy only because they started in
/// different files.
pub(crate) struct PlacedPin {
    pub reference: String,
    pub number: String,
    pub name: String,
    pub x: f64,
    pub y: f64,
    /// The instance's own placement point — not the pin's — which is what
    /// [`pin_outward_at`] measures the pin's direction against.
    pub origin_x: f64,
    pub origin_y: f64,
}

pub(crate) fn placed_pins(tree: &konnect_sexp::SexpNode) -> Vec<PlacedPin> {
    use konnect_sexp::schematic::{
        extract_lib_pins_for_unit, extract_symbol_instances, find_lib_symbol, pin_endpoint,
    };
    let lib_syms = tree
        .find("lib_symbols")
        .map(|node| node.find_all("symbol"))
        .unwrap_or_default();
    let mut out = Vec::new();
    for instance in extract_symbol_instances(tree) {
        let Some(lib_sym) = find_lib_symbol(&lib_syms, &instance) else {
            continue;
        };
        for pin in extract_lib_pins_for_unit(lib_sym, instance.unit) {
            let (x, y) = pin_endpoint(&pin, instance.pin_transform());
            out.push(PlacedPin {
                reference: instance.reference.clone(),
                number: pin.number.clone(),
                name: pin.name.clone(),
                x,
                y,
                origin_x: instance.x,
                origin_y: instance.y,
            });
        }
    }
    out
}

/// All symbol pin connection points in a parsed schematic tree.
///
/// Unit-aware: a multi-unit library symbol superimposes every unit's pins on
/// one placement, so an instance of unit 1 must not report unit 2's pins (#35).
/// These coordinates drive junction insertion, and a dot dropped on a phantom
/// pin where two wires cross would short them.
pub(crate) fn all_pin_endpoints(tree: &konnect_sexp::SexpNode) -> Vec<(f64, f64)> {
    placed_pins(tree).into_iter().map(|p| (p.x, p.y)).collect()
}

/// The direction that leads a stub off the pin placed at `(x, y)` without
/// crossing its symbol's body: the dominant axis away from the instance's
/// own placement origin (`dx = pin.x - origin.x`, `dy = pin.y - origin.y`;
/// `|dx| >= |dy|` picks `"left"`/`"right"` by the sign of `dx`, otherwise
/// `"up"`/`"down"` by the sign of `dy`).
///
/// This needs no rotation/mirror bookkeeping of its own: `placed_pins`
/// already transformed both the pin and the origin into sheet space, so the
/// vector between them already points outward in whatever orientation the
/// instance was placed in. `None` when no placed pin sits at `(x, y)` — the
/// caller falls back to its own default rather than guessing (P.6.8.5).
///
/// Tolerance matches [`add_pin_midwire_junctions`]'s `0.01`, the value
/// already used to compare points in this module.
pub(crate) fn pin_outward_at(
    tree: &konnect_sexp::SexpNode,
    x: f64,
    y: f64,
) -> Option<&'static str> {
    use konnect_sexp::geometry::points_coincident;
    let tol = 0.01;
    let pin = placed_pins(tree)
        .into_iter()
        .find(|p| points_coincident(p.x, p.y, x, y, tol))?;
    let dx = pin.x - pin.origin_x;
    let dy = pin.y - pin.origin_y;
    Some(if dx.abs() >= dy.abs() {
        if dx < 0.0 {
            "left"
        } else {
            "right"
        }
    } else if dy < 0.0 {
        "up"
    } else {
        "down"
    })
}

/// Add junction dots for pins of `reference` that land mid-segment on a wire.
/// KiCad connects a pin mid-wire only through a junction dot (verified with
/// kicad-cli 10: a junction alone connects; splitting the wire is unnecessary).
/// Returns the junction positions added.
pub(crate) fn add_pin_midwire_junctions(
    sch_path: &std::path::Path,
    reference: &str,
) -> anyhow::Result<Vec<(f64, f64)>> {
    use konnect_sexp::geometry::{point_on_segment, points_coincident};
    use konnect_sexp::schematic::{
        extract_junction_points, extract_lib_pins_for_unit, extract_symbol_instances,
        extract_wires, find_lib_symbol, pin_endpoint, read_schematic,
    };
    let tol = 0.01;
    let (_, tree) = read_schematic(sch_path)?;
    let wires = extract_wires(&tree);
    if wires.is_empty() {
        return Ok(Vec::new());
    }
    let junctions = extract_junction_points(&tree);
    let lib_syms = tree
        .find("lib_symbols")
        .map(|n| n.find_all("symbol"))
        .unwrap_or_default();
    let mut to_add: Vec<(f64, f64)> = Vec::new();
    for inst in extract_symbol_instances(&tree)
        .iter()
        .filter(|i| i.reference == reference)
    {
        let Some(sym) = find_lib_symbol(&lib_syms, inst) else {
            continue;
        };
        let t = inst.pin_transform();
        // Unit-aware for the same reason as all_pin_endpoints: this one writes
        // to the user's file, so a phantom-pin junction is a real defect.
        for pin in extract_lib_pins_for_unit(sym, inst.unit) {
            let (px, py) = pin_endpoint(&pin, t);
            let mid_wire = wires.iter().any(|w| {
                point_on_segment(px, py, w.x1, w.y1, w.x2, w.y2, tol)
                    && !points_coincident(px, py, w.x1, w.y1, tol)
                    && !points_coincident(px, py, w.x2, w.y2, tol)
            });
            let already = junctions
                .iter()
                .chain(to_add.iter())
                .any(|(jx, jy)| points_coincident(px, py, *jx, *jy, tol));
            if mid_wire && !already {
                to_add.push((px, py));
            }
        }
    }
    if !to_add.is_empty() {
        let mut sch = konnect_schematic_editor::Schematic::load(sch_path)?;
        for &(x, y) in &to_add {
            sch.add_junction(x, y);
        }
        sch.overwrite()?;
    }
    Ok(to_add)
}

/// Round a computed millimetre coordinate to six decimals (D125).
///
/// Six decimals, measured: across 126 933 `(at ...)` coordinates in the KiCad
/// 10 demo schematics, every one but a single value carries at most **four**
/// decimals. The exception, `59.209102362204725`, is an inch conversion rather
/// than float noise, and six decimals moves it by 0.4 nm - under KiCAD's own
/// 1 nm internal resolution. Addition noise, meanwhile, shows up around the
/// thirteenth decimal. Six separates the two with room on both sides.
///
/// Anything that *computes* a coordinate goes through here: a bulk move adds a
/// delta, a placed field runs the library anchor through a rotation. Neither
/// may leak binary-float noise into a file the caller never asked to change --
/// a symbol's own anchor is protected by `snap_point`, but a property anchor
/// is not, and `139.7 -> 144.78` moves a field at `241.3` to
/// `246.38000000000002` and one at `3.556` to `8.636000000000013`. Writing
/// that is the same class of damage P.6.9.4 removed.
pub(crate) fn mm(value: f64) -> f64 {
    (value * 1e6).round() / 1e6
}

/// Push the four properties eeschema writes onto a freshly placed symbol --
/// `Reference`, `Value`, `Footprint`, `Datasheet` -- where the **library
/// symbol itself** says they belong (P.6.8.8).
///
/// The anchor comes from the embedded `lib_symbols` entry and is transformed
/// exactly like a pin: `transform_pin` flips the library's Y-up space, applies
/// the placement rotation and mirror, and translates to the instance origin.
/// The text angle is the library's own, not the placement's.
///
/// Measured over the KiCad 10 demo corpus, 12 894 placed `Reference`/`Value`
/// fields, against the position each file actually carries:
///
/// | rule                                        | reproduces |
/// |---------------------------------------------|------------|
/// | fixed `y -/+ 3.81`, angle 0 (what this did)  | 7.5 %      |
/// | library anchor **transformed** (this)        | 41.4 %     |
/// | library anchor translated, rotation ignored  | 24.2 %     |
///
/// The remainder is fields a human dragged, which no rule reproduces and none
/// should. What decides it is the rotated buckets, where the old rule is
/// essentially never right (10 of 2 440 at 90 degrees) and rotating the anchor
/// beats not rotating it more than ten to one.
///
/// `sch` must already carry the library definition -- `ensure_lib_symbol`
/// first -- or every field falls back to the old fixed offsets, which is also
/// what happens for a symbol whose library entry declares no such field.
pub(crate) fn push_placed_fields(
    sch: &konnect_schematic_editor::Schematic,
    sym: &mut konnect_schematic_editor::Symbol,
    reference: &str,
    value: &str,
    hide_reference: bool,
) {
    use konnect_sexp::geometry::{transform_pin, PinTransform};

    let lib_key = sym.lib_symbol_name().to_string();
    let (x, y) = (sym.at.x, sym.at.y);
    let mirror = sym.mirror.clone().unwrap_or_default();
    let transform = PinTransform {
        comp_x: x,
        comp_y: y,
        rotation_deg: sym.at.rotation.unwrap_or(0.0),
        mirror_x: mirror == "x" || mirror == "xy",
        mirror_y: mirror == "y" || mirror == "xy",
    };

    // Reference above the component, Value below, Footprint/Datasheet on the
    // origin: the fallback, used when the library entry has nothing to say.
    for (name, value, fallback_dy, hide) in [
        ("Reference", reference, -3.81, hide_reference),
        ("Value", value, 3.81, false),
        ("Footprint", "", 0.0, true),
        ("Datasheet", "", 0.0, true),
    ] {
        let prop = match konnect_schematic_editor::library::field_anchor(sch, &lib_key, name) {
            Some(anchor) => {
                let (px, py) = transform_pin(anchor.x, anchor.y, transform);
                // `hide` unions with the library's: a power symbol's library
                // entry hides its own Reference, and the caller hides the
                // Reference of anything designated `#PWR` whether or not the
                // library thought to.
                anchored_property(
                    name,
                    value,
                    mm(px),
                    mm(py),
                    anchor.angle,
                    hide || anchor.hide,
                    anchor.effects,
                )
            }
            None => positioned_property(name, value, x, y + fallback_dy, 0.0, hide),
        };
        sym.properties.push(prop);
    }
}

/// A property written at an already-transformed point, carrying the library's
/// own `(effects ...)` -- font size and justification both -- rather than the
/// 1.27mm default [`positioned_property`] invents.
///
/// Copying the justification is not decoration: measured on the demo corpus,
/// the fields eeschema placed itself carry the library's justification
/// verbatim in the overwhelming majority, and a `left`-justified reference
/// written without it shifts by half its own width.
fn anchored_property(
    name: &str,
    value: &str,
    x: f64,
    y: f64,
    angle: f64,
    hide: bool,
    effects: Option<konnect_schematic_editor::sexp::SexpNode>,
) -> konnect_schematic_editor::Property {
    use konnect_schematic_editor::sexp::{atom, SexpNode};
    use konnect_schematic_editor::types::fmt_f64;

    let mut prop = konnect_schematic_editor::Property::new(name, value);
    prop.sub_nodes.push(SexpNode::List(vec![
        atom("at"),
        atom(fmt_f64(x)),
        atom(fmt_f64(y)),
        atom(fmt_f64(angle)),
    ]));
    if hide {
        prop.sub_nodes
            .push(SexpNode::List(vec![atom("hide"), atom("yes")]));
    }
    prop.sub_nodes.push(effects.unwrap_or_else(|| {
        SexpNode::List(vec![
            atom("effects"),
            SexpNode::List(vec![
                atom("font"),
                SexpNode::List(vec![atom("size"), atom("1.27"), atom("1.27")]),
            ]),
        ])
    }));
    prop
}

/// A symbol-instance property positioned in absolute sheet coordinates, with
/// eeschema's default 1.27mm font. The `(at)` node is mandatory: a property
/// written without one is defaulted to the sheet origin by KiCAD, which is how
/// every `#PWR` reference used to pile up in the top-left corner (PR #95).
///
/// Hidden properties get KiCAD 10's property-level `(hide yes)` — a sibling
/// before `(effects)`, exactly as eeschema writes instances (PR #96); the
/// legacy hide-inside-effects form renders the same but round-trips dirty.
pub(crate) fn positioned_property(
    name: &str,
    value: &str,
    x: f64,
    y: f64,
    rotation: f64,
    hide: bool,
) -> konnect_schematic_editor::Property {
    use konnect_schematic_editor::sexp::{atom, SexpNode};
    use konnect_schematic_editor::types::fmt_f64;

    let mut prop = konnect_schematic_editor::Property::new(name, value);
    prop.sub_nodes.push(SexpNode::List(vec![
        atom("at"),
        atom(fmt_f64(x)),
        atom(fmt_f64(y)),
        atom(fmt_f64(rotation)),
    ]));
    if hide {
        prop.sub_nodes
            .push(SexpNode::List(vec![atom("hide"), atom("yes")]));
    }
    prop.sub_nodes.push(SexpNode::List(vec![
        atom("effects"),
        SexpNode::List(vec![
            atom("font"),
            SexpNode::List(vec![atom("size"), atom("1.27"), atom("1.27")]),
        ]),
    ]));
    prop
}

// ─── Schematic text helpers ──────────────────────────────────────────────────

/// Byte range of the placed `(symbol …)` block whose Reference property is
/// `reference`, for the text-editing tool paths.
///
/// Works regardless of indentation — eeschema saves with tabs, this crate's
/// writer uses two spaces — and skips library definitions inside `lib_symbols`,
/// which carry a Reference property of their own (`"R"`, `"#PWR"`, or whatever
/// a hand-authored library sets) but never a `lib_id`. Only placed instances
/// have one, so that's the discriminator.
pub fn find_symbol_instance_block(content: &str, reference: &str) -> Option<(usize, usize)> {
    find_all_symbol_instance_blocks(content, reference)
        .into_iter()
        .next()
}

/// Every placed `(symbol …)` block whose Reference property is `reference`,
/// in document order.
///
/// A multi-unit symbol (e.g. a quad op-amp) is written as one such block per
/// unit, all sharing the same designator and each carrying its own uuid and
/// its own copy of `Value`/`Footprint`/`Datasheet` (P.6.8.1 fixture
/// `multiunit_lm2904.kicad_sch`). Measured on that fixture: editing `Value`
/// on the first unit's block alone and exporting the netlist reports the
/// edited value, but editing the *second* unit's block alone reports the
/// stale one — KiCad's netlist export reads only the first block. A tool
/// that also reads or writes only the first block therefore produces a
/// correct netlist by accident while leaving a file that contradicts
/// itself: every unit past the first still shows the old value in eeschema,
/// and any by-unit read (this crate's included) returns it. This is the
/// shared block-finder `find_symbol_instance_block` used to guess at with a
/// single hit; the two must not diverge on what "an instance block" means
/// (D136), so that one is now expressed in terms of this one.
pub fn find_all_symbol_instance_blocks(content: &str, reference: &str) -> Vec<(usize, usize)> {
    let ref_search = format!(r#"(property "Reference" "{reference}""#);
    let mut from = 0usize;
    let mut blocks = Vec::new();

    while let Some(rel) = content[from..].find(&ref_search) {
        let ref_pos = from + rel;
        if let Some((start, end)) =
            konnect_sexp::writer::find_enclosing_block(content, "symbol", ref_pos)
        {
            if content[start..end].contains("(lib_id ") {
                blocks.push((start, end));
            }
        }
        from = ref_pos + ref_search.len();
    }
    blocks
}

/// The `(uuid "…")` of one such block, by plain text search.
///
/// Every message that has to name the units of a multi-unit symbol reads it
/// the same way — the single-symbol refusal in `sch_components` and the
/// per-entry one in `sch_batch` — and a second copy of this search is a second
/// thing to drift (D136). Text rather than an [`ItemId`] because these
/// messages are written *before* an edit, about blocks located by offset.
pub(crate) fn symbol_block_uuid(block: &str) -> Option<String> {
    const NEEDLE: &str = r#"(uuid ""#;
    let start = block.find(NEEDLE)? + NEEDLE.len();
    let end = start + block[start..].find('"')?;
    Some(block[start..end].to_string())
}

// ─── Symbol property scanning (string-aware) ─────────────────────────────────
//
// Shared by `sch_components` (single-symbol property edits) and `sch_batch`
// (bulk move, which must drag each property's own `(at …)` along with the
// symbol). A naive `find("(property \"")` is fooled by a property *value*
// that happens to contain that literal text; these walk the tree by nesting
// depth and quote/escape state instead, the same technique
// `konnect_sexp::writer::find_direct_child_blocks` already uses for top-level
// schematic items.

/// Property keys that carry an invariant a generic "add a custom property"
/// call would break.
///
/// `Reference` is the only one: `edit_schematic_component`'s
/// `new_reference` argument routes a `Reference` change through
/// `sch_components::update_instance_reference`, which repoints the symbol's
/// `(instances …)` entries — the designator KiCAD's own netlist export
/// actually reads — to match. Writing `Reference` through this generic path
/// instead would leave `(instances …)` pointing at the stale designator, so
/// it is refused. `Value` / `Footprint` / `Datasheet` carry no such
/// invariant — they are ordinary properties like any custom key, and
/// `add_component_annotation` setting one is exactly how
/// `the_bom_audit_finds_missing_footprints_and_lets_go_when_they_are_assigned`
/// (design_review.rs) already uses it — so they are not in this list.
pub(crate) const RESERVED_PROPERTY_KEYS: &[&str] = &["Reference"];

/// Direct-child `(property …)` blocks of the symbol at `sym_block` (which
/// must itself start with `(symbol`), by nesting depth rather than text
/// search.
pub(crate) fn symbol_property_blocks(sym_block: &str) -> Vec<(usize, usize)> {
    konnect_sexp::writer::find_direct_child_blocks(sym_block, "symbol")
        .into_iter()
        .filter(|&(s, e)| sym_block[s..e].starts_with("(property "))
        .collect()
}

/// Byte range (relative to `s`), exclusive of the surrounding quotes, of the
/// first quoted string found at or after `from`. Honors backslash escapes,
/// so a value like `"a \"quoted\" word"` is not cut short at the escaped
/// quote.
pub(crate) fn quoted_string_after(s: &str, from: usize) -> Option<(usize, usize)> {
    let rel_open = s.get(from..)?.find('"')?;
    let open = from + rel_open;
    let bytes = s.as_bytes();
    let mut i = open + 1;
    let mut escape = false;
    while i < bytes.len() {
        let b = bytes[i];
        if escape {
            escape = false;
        } else if b == b'\\' {
            escape = true;
        } else if b == b'"' {
            return Some((open + 1, i));
        }
        i += 1;
    }
    None
}

/// An existing `(property "<key>" "<value>" …)` block located inside a
/// symbol, with byte ranges relative to the same `content` the symbol was
/// found in.
pub(crate) struct SymbolProperty {
    pub value_start: usize,
    pub value_end: usize,
}

/// The direct-child property of the symbol at `content[sym_start..sym_end]`
/// whose key is exactly `field`, if it has one. String-aware: a property
/// whose *value* contains the literal text `(property "` is not mistaken for
/// a second property, because candidates come from
/// [`symbol_property_blocks`] (depth-based) and the key comparison is on the
/// quote/escape-aware extracted text, not a substring match.
pub(crate) fn find_symbol_property(
    content: &str,
    sym_start: usize,
    sym_end: usize,
    field: &str,
) -> Option<SymbolProperty> {
    let sym_block = &content[sym_start..sym_end];
    for (p_start, p_end) in symbol_property_blocks(sym_block) {
        let block = &sym_block[p_start..p_end];
        let (key_s, key_e) = quoted_string_after(block, 0)?;
        if &block[key_s..key_e] != field {
            continue;
        }
        let (val_s, val_e) = quoted_string_after(block, key_e + 1)?;
        return Some(SymbolProperty {
            value_start: sym_start + p_start + val_s,
            value_end: sym_start + p_start + val_e,
        });
    }
    None
}

/// Byte range (in `content`) of the coordinate text inside each `(at x y
/// rot)` that is a direct child of a `(property …)` under the symbol at
/// `content[sym_start..sym_end]` — one entry per property that has one
/// (every property eeschema or this crate writes does).
///
/// For bulk-move: a symbol's field text carries its own absolute `(at …)`,
/// so moving only the symbol's own anchor leaves every field's text sitting
/// where the symbol used to be.
pub(crate) fn symbol_property_at_spans(
    content: &str,
    sym_start: usize,
    sym_end: usize,
) -> Vec<(usize, usize)> {
    let sym_block = &content[sym_start..sym_end];
    let mut out = Vec::new();
    for (p_start, p_end) in symbol_property_blocks(sym_block) {
        let prop_block = &sym_block[p_start..p_end];
        for (a_start, a_end) in
            konnect_sexp::writer::find_direct_child_blocks(prop_block, "property")
        {
            let at_block = &prop_block[a_start..a_end];
            if let Some(rest) = at_block.strip_prefix("(at ") {
                let coord_len = rest.len().saturating_sub(1); // drop the closing ')'
                let coord_abs_start = sym_start + p_start + a_start + 4;
                out.push((coord_abs_start, coord_abs_start + coord_len));
            }
        }
    }
    out
}

/// Where to insert a property the symbol at `content[sym_start..sym_end]`
/// does not carry yet.
pub(crate) struct SymbolInsertionSite {
    /// Byte offset in `content` to insert the new property's text at.
    pub insert_at: usize,
    /// Indentation for the new `(property …)` line, read off an existing
    /// direct child of the symbol so it matches the file's own style: tabs
    /// on a file eeschema saved, this crate's own two-space indent on one
    /// this crate wrote (P.6.9.4).
    pub indent: String,
    /// Indentation for the property's own children (`(at …)`, `(effects
    /// …)`), one nesting level deeper than `indent`.
    pub child_indent: String,
    /// The symbol's own position — `(x, y)` from its own `(at x y rot)`,
    /// the anchor a new hidden property should use.
    ///
    /// Measured on `CM5.kicad_sch` (KiCad 10 demos): a hidden custom
    /// property nothing else has repositioned (`Description` on the `GND`
    /// power symbol at `(at 139.7 241.3 0)`, and again on a *rotated*
    /// connector symbol at `(at 119.38 238.76 270)`) is written at
    /// `(at <symbol-x> <symbol-y> 0)` — the symbol's own (x, y), rotation
    /// always 0 regardless of the symbol's own rotation. The origin
    /// `(at 0 0 0)` this code used to write unconditionally only matches
    /// that by coincidence when a symbol happens to sit at the origin.
    pub anchor: (f64, f64),
}

/// Compute [`SymbolInsertionSite`] for the symbol at
/// `content[sym_start..sym_end]`. `None` only for a symbol block malformed
/// enough to carry no `(at …)` of its own, which should not occur for an
/// already-placed symbol.
pub(crate) fn symbol_insertion_site(
    content: &str,
    sym_start: usize,
    sym_end: usize,
) -> Option<SymbolInsertionSite> {
    let sym_block = &content[sym_start..sym_end];
    let children = konnect_sexp::writer::find_direct_child_blocks(sym_block, "symbol");

    // The symbol's own `(at x y rot)` is a direct child that comes before any
    // `(property …)`, so the first one found is it, not a property's.
    let (at_s, at_e) = children
        .iter()
        .find(|&&(s, e)| sym_block[s..e].starts_with("(at "))
        .copied()?;
    let at_text = &sym_block[at_s + 4..at_e.saturating_sub(1)];
    let mut parts = at_text.split_whitespace();
    let x: f64 = parts.next()?.parse().ok()?;
    let y: f64 = parts.next()?.parse().ok()?;

    let indent_of = |abs_pos: usize| -> String {
        let line_start = content[..abs_pos].rfind('\n').map(|p| p + 1).unwrap_or(0);
        content[line_start..abs_pos]
            .chars()
            .take_while(|c| *c == ' ' || *c == '\t')
            .collect()
    };
    // Indentation of an existing direct child, so the inserted line matches
    // this file's own style; a symbol block with no children to measure
    // (should not happen for a placed symbol) falls back to a tab, the shape
    // eeschema itself writes.
    let indent = children
        .last()
        .map(|&(s, _)| indent_of(sym_start + s))
        .unwrap_or_else(|| "\t".to_string());
    // One nesting level deeper, measured from an existing property's own
    // `(at …)` line if there is one; otherwise `indent` plus one more unit of
    // whatever it is already made of.
    let child_indent = symbol_property_blocks(sym_block)
        .first()
        .and_then(|&(p_s, p_e)| {
            let prop_block = &sym_block[p_s..p_e];
            konnect_sexp::writer::find_direct_child_blocks(prop_block, "property")
                .first()
                .map(|&(c_s, _)| indent_of(sym_start + p_s + c_s))
        })
        .unwrap_or_else(|| {
            let unit = if indent.starts_with('\t') { "\t" } else { "  " };
            format!("{indent}{unit}")
        });

    let insert_at = sym_block
        .find("(instances")
        .or_else(|| sym_block.rfind(')'))
        .map(|rel| sym_start + rel)?;

    Some(SymbolInsertionSite {
        insert_at,
        indent,
        child_indent,
        anchor: (x, y),
    })
}

/// Why [`set_symbol_property`] could not apply a change.
#[derive(Debug)]
pub(crate) enum SetPropertyError {
    /// `field` is in the caller's reject-list (typically
    /// [`RESERVED_PROPERTY_KEYS`]).
    Reserved(String),
    /// The symbol block has no `(at …)` of its own to insert a new property
    /// relative to — too malformed to edit safely.
    Malformed,
}

impl std::fmt::Display for SetPropertyError {
    fn fmt(&self, f: &mut std::fmt::Formatter<'_>) -> std::fmt::Result {
        match self {
            SetPropertyError::Reserved(field) => write!(
                f,
                "'{field}' is a reserved property; use edit_schematic_component to change it"
            ),
            SetPropertyError::Malformed => {
                write!(f, "symbol block is too malformed to add a property to")
            }
        }
    }
}

/// Whether [`set_symbol_property`] updated a property the symbol already had
/// or inserted a new one.
#[derive(Debug)]
pub(crate) enum SetPropertyOutcome {
    Updated,
    Inserted,
}

/// Set property `field` on the symbol at `content[sym_start..sym_end]` to
/// `value`: update it in place if the symbol already carries one, otherwise
/// insert a new hidden one at the symbol's own position ([`symbol_insertion_site`]).
///
/// `reject` is checked first and unconditionally — including against a
/// property the symbol already has — so a caller that must not touch a given
/// key (e.g. `Reference`, whose designator lives in `(instances …)` too and
/// needs its own update path) cannot do so through this generic entry point
/// at all.
pub(crate) fn set_symbol_property(
    content: &str,
    sym_start: usize,
    sym_end: usize,
    field: &str,
    value: &str,
    reject: &[&str],
) -> Result<(String, SetPropertyOutcome), SetPropertyError> {
    if reject.contains(&field) {
        return Err(SetPropertyError::Reserved(field.to_string()));
    }
    if let Some(prop) = find_symbol_property(content, sym_start, sym_end, field) {
        let updated = format!(
            "{}{}{}",
            &content[..prop.value_start],
            value,
            &content[prop.value_end..]
        );
        return Ok((updated, SetPropertyOutcome::Updated));
    }
    let site =
        symbol_insertion_site(content, sym_start, sym_end).ok_or(SetPropertyError::Malformed)?;
    let (ax, ay) = site.anchor;
    let indent = &site.indent;
    let child = &site.child_indent;
    let property = format!(
        "{indent}(property \"{field}\" \"{value}\"\n\
         {child}(at {ax} {ay} 0)\n\
         {child}(effects (font (size 1.27 1.27)) (hide yes))\n\
         {indent})\n\
         {indent}"
    );
    let updated = format!(
        "{}{}{}",
        &content[..site.insert_at],
        property,
        &content[site.insert_at..]
    );
    Ok((updated, SetPropertyOutcome::Inserted))
}

/// [`set_symbol_property`], applied to every unit of `reference` rather than
/// just the block a plain search happens to land on first.
///
/// `Value` / `Footprint` / `Datasheet` and any custom field are properties of
/// the *component*, not of one unit's placement — KiCad's own editor keeps
/// them identical across every unit of a multi-unit symbol. Writing only the
/// first block, as `find_symbol_instance_block` alone would, is the
/// "accidentally correct netlist, self-contradicting file" defect documented
/// on [`find_all_symbol_instance_blocks`]; this is how the reference-addressed
/// edit paths (`edit_schematic_component`, `batch_edit`,
/// `add_component_annotation`, `replace_component`'s `lib_id`) avoid it.
///
/// Edits are applied in descending start-offset order: rewriting a later
/// block only shifts bytes after its own start, which never reaches an
/// earlier block still waiting its turn, so every block's offset from the
/// initial scan stays valid when its edit is finally applied — the same
/// reasoning `handle_batch_edit` already relies on by re-searching after
/// every write instead.
///
/// The returned outcome is the first unit's ([`SetPropertyOutcome::Inserted`]
/// if the property was absent there, `Updated` otherwise) — what a caller
/// reporting "added" vs. a plain change means by "the property".
pub(crate) fn set_symbol_property_on_all_units(
    content: &str,
    reference: &str,
    field: &str,
    value: &str,
    reject: &[&str],
) -> Result<(String, SetPropertyOutcome), SetPropertyError> {
    let mut blocks = find_all_symbol_instance_blocks(content, reference);
    blocks.sort_by_key(|b| std::cmp::Reverse(b.0));

    let mut new_content = content.to_string();
    let mut outcomes: Vec<(usize, SetPropertyOutcome)> = Vec::new();
    for (start, end) in blocks {
        let (updated, outcome) =
            set_symbol_property(&new_content, start, end, field, value, reject)?;
        new_content = updated;
        outcomes.push((start, outcome));
    }
    outcomes.sort_by_key(|(start, _)| *start);
    let outcome = outcomes
        .into_iter()
        .next()
        .map(|(_, o)| o)
        .unwrap_or(SetPropertyOutcome::Updated);
    Ok((new_content, outcome))
}

/// Properties a symbol cannot be stripped of. `Reference` and `Value` are
/// what eeschema requires of every symbol; removing either leaves a file
/// KiCAD reads as a symbol with no designator or no value at all.
pub(crate) const UNDELETABLE_PROPERTY_KEYS: &[&str] = &["Reference", "Value"];

/// Why [`remove_symbol_property`] could not remove a property.
#[derive(Debug)]
pub(crate) enum RemovePropertyError {
    /// `field` is one of [`UNDELETABLE_PROPERTY_KEYS`].
    Undeletable(String),
    /// The symbol carries no property by that name. Removing what is not
    /// there is reported rather than passed off as a change: a caller that
    /// misspelled the key would otherwise be told its cleanup succeeded.
    Absent(String),
}

impl std::fmt::Display for RemovePropertyError {
    fn fmt(&self, f: &mut std::fmt::Formatter<'_>) -> std::fmt::Result {
        match self {
            RemovePropertyError::Undeletable(field) => {
                write!(f, "'{field}' is required by KiCAD and cannot be removed")
            }
            RemovePropertyError::Absent(field) => {
                write!(f, "the symbol carries no '{field}' property")
            }
        }
    }
}

/// Remove the property `field` from the symbol at
/// `content[sym_start..sym_end]`, block and trailing whitespace, so the
/// document keeps the line structure eeschema wrote.
///
/// The counterpart of [`set_symbol_property`]'s insert-when-missing half
/// (W.3.5): a property this crate — or a client — added by mistake was
/// otherwise permanent, editable to the empty string and never removable,
/// which is not the same thing to KiCAD's field list, its BOM export or a
/// reader of the file.
pub(crate) fn remove_symbol_property(
    content: &str,
    sym_start: usize,
    sym_end: usize,
    field: &str,
) -> Result<String, RemovePropertyError> {
    if UNDELETABLE_PROPERTY_KEYS.contains(&field) {
        return Err(RemovePropertyError::Undeletable(field.to_string()));
    }
    let sym_block = &content[sym_start..sym_end];
    let (p_start, p_end) = symbol_property_blocks(sym_block)
        .into_iter()
        .find(|&(p_start, p_end)| {
            let block = &sym_block[p_start..p_end];
            quoted_string_after(block, 0).is_some_and(|(s, e)| &block[s..e] == field)
        })
        .ok_or_else(|| RemovePropertyError::Absent(field.to_string()))?;

    // The block plus what surrounds it on its own line: the indentation before
    // it and the newline after, so removing the last property of a symbol does
    // not leave a blank indented line behind.
    let mut start = sym_start + p_start;
    let mut end = sym_start + p_end;
    let line_start = content[..start].rfind('\n').map(|p| p + 1).unwrap_or(0);
    if content[line_start..start]
        .chars()
        .all(|c| c == ' ' || c == '\t')
    {
        start = line_start;
        if let Some(rel) = content[end..].find('\n') {
            end += rel + 1;
        }
    }
    Ok(format!("{}{}", &content[..start], &content[end..]))
}

/// [`remove_symbol_property`], applied to every unit of `reference`.
///
/// A property is the component's, not one unit's — the same reasoning as
/// [`set_symbol_property_on_all_units`], and the same descending-order walk.
/// A unit that does not carry the property is not an error here: what the
/// caller asked for is that no unit carries it afterwards. Absence on *every*
/// unit still is one.
pub(crate) fn remove_symbol_property_on_all_units(
    content: &str,
    reference: &str,
    field: &str,
) -> Result<String, RemovePropertyError> {
    let mut blocks = find_all_symbol_instance_blocks(content, reference);
    blocks.sort_by_key(|b| std::cmp::Reverse(b.0));

    let mut new_content = content.to_string();
    let mut removed = 0usize;
    for (start, end) in blocks {
        match remove_symbol_property(&new_content, start, end, field) {
            Ok(updated) => {
                new_content = updated;
                removed += 1;
            }
            Err(RemovePropertyError::Absent(_)) => continue,
            Err(other) => return Err(other),
        }
    }
    if removed == 0 {
        return Err(RemovePropertyError::Absent(field.to_string()));
    }
    Ok(new_content)
}

/// The three native symbol attributes KiCAD stores as tags of the symbol
/// block itself — not as properties (W.3.1).
///
/// `in_bom` and `on_board` default to yes and `dnp` to no, which is why a
/// symbol that carries none of the three is still fully determined.
pub(crate) const SYMBOL_ATTRIBUTES: &[&str] = &["in_bom", "on_board", "dnp"];

/// The order eeschema writes a symbol block's direct children in. Used only
/// to place a newly inserted attribute where KiCAD would have written it, so
/// a file this tool touches keeps looking like one KiCAD wrote. A child not
/// listed here sorts last, which puts an inserted attribute before it.
const SYMBOL_CHILD_ORDER: &[&str] = &[
    "lib_id",
    "at",
    "unit",
    "exclude_from_sim",
    "in_bom",
    "on_board",
    "dnp",
    "fields_autoplaced",
    "uuid",
    "property",
    "pin",
    "instances",
];

/// The head word of an S-expression block, e.g. `"property"` for
/// `(property "Value" …)`.
fn block_head(block: &str) -> &str {
    block
        .strip_prefix('(')
        .unwrap_or(block)
        .split(|c: char| c.is_whitespace() || c == '(' || c == ')')
        .next()
        .unwrap_or("")
}

/// Set the native attribute `name` (one of [`SYMBOL_ATTRIBUTES`]) on the
/// symbol at `content[sym_start..sym_end]`.
///
/// These are tags of the symbol block, not properties: writing `dnp` through
/// [`set_symbol_property`] would produce `(property "dnp" "yes")`, a custom
/// field KiCAD shows in the symbol's field list and ignores everywhere it
/// matters — the netlist, the BOM, the board update. Hence a separate path
/// (W.3.2).
///
/// A symbol that does not carry the tag yet has one inserted where eeschema
/// would have written it ([`SYMBOL_CHILD_ORDER`]), because omitting the tag
/// is how KiCAD spells the default and an explicit non-default has to be
/// written to exist at all.
pub(crate) fn set_symbol_attribute(
    content: &str,
    sym_start: usize,
    sym_end: usize,
    name: &str,
    value: bool,
) -> Result<(String, SetPropertyOutcome), SetPropertyError> {
    if !SYMBOL_ATTRIBUTES.contains(&name) {
        return Err(SetPropertyError::Reserved(name.to_string()));
    }
    let sym_block = &content[sym_start..sym_end];
    let children = konnect_sexp::writer::find_direct_child_blocks(sym_block, "symbol");
    let tag = format!("({name} {})", if value { "yes" } else { "no" });

    if let Some(&(s, e)) = children
        .iter()
        .find(|&&(s, e)| block_head(&sym_block[s..e]) == name)
    {
        let updated = format!(
            "{}{}{}",
            &content[..sym_start + s],
            tag,
            &content[sym_start + e..]
        );
        return Ok((updated, SetPropertyOutcome::Updated));
    }

    let rank = |head: &str| {
        SYMBOL_CHILD_ORDER
            .iter()
            .position(|k| *k == head)
            .unwrap_or(SYMBOL_CHILD_ORDER.len())
    };
    let own_rank = rank(name);
    // The first child that belongs after this attribute; the tag is inserted
    // on its own line just before it.
    let (before_s, _) = children
        .iter()
        .find(|&&(s, e)| rank(block_head(&sym_block[s..e])) > own_rank)
        .copied()
        .ok_or(SetPropertyError::Malformed)?;
    let insert_at = sym_start + before_s;
    let line_start = content[..insert_at].rfind('\n').map(|p| p + 1).unwrap_or(0);
    let indent: String = content[line_start..insert_at]
        .chars()
        .take_while(|c| *c == ' ' || *c == '\t')
        .collect();
    let updated = format!(
        "{}{tag}\n{indent}{}",
        &content[..insert_at],
        &content[insert_at..]
    );
    Ok((updated, SetPropertyOutcome::Inserted))
}

/// [`set_symbol_attribute`], applied to every unit of `reference`.
///
/// The three attributes belong to the component, not to one unit's placement:
/// KiCAD's own editor sets them on every unit at once, and a file where unit
/// A is `dnp yes` and unit B is not is the same self-contradiction
/// [`set_symbol_property_on_all_units`] exists to avoid. Blocks are rewritten
/// in descending start order for the same reason.
pub(crate) fn set_symbol_attribute_on_all_units(
    content: &str,
    reference: &str,
    name: &str,
    value: bool,
) -> Result<(String, SetPropertyOutcome), SetPropertyError> {
    let mut blocks = find_all_symbol_instance_blocks(content, reference);
    blocks.sort_by_key(|b| std::cmp::Reverse(b.0));

    let mut new_content = content.to_string();
    let mut outcomes: Vec<(usize, SetPropertyOutcome)> = Vec::new();
    for (start, end) in blocks {
        let (updated, outcome) = set_symbol_attribute(&new_content, start, end, name, value)?;
        new_content = updated;
        outcomes.push((start, outcome));
    }
    outcomes.sort_by_key(|(start, _)| *start);
    let outcome = outcomes
        .into_iter()
        .next()
        .map(|(_, o)| o)
        .unwrap_or(SetPropertyOutcome::Updated);
    Ok((new_content, outcome))
}

/// `(start, end, kind)` of a top-level schematic item's own block, resolved
/// by UUID via the canonical index in `konnect_sexp::command`, for the
/// text-editing tool paths.
///
/// Returns `Ok(None)` when no item carries this UUID as its own (direct-
/// child) identity — a UUID nested inside another item (e.g. a sheet pin)
/// does not match. `kind` is the item's S-expression head (`"wire"`,
/// `"symbol"`, `"text"`, …), for callers that must reject an existing UUID
/// belonging to the wrong kind of item.
///
/// # Errors
///
/// Propagates a [`konnect_sexp::SexpError`] if `content` cannot be indexed
/// at all — missing `kicad_sch` root, or a direct-child block that fails to
/// parse.
pub(crate) fn find_schematic_item_by_uuid(
    content: &str,
    uuid: &str,
) -> Result<Option<(usize, usize, Option<String>)>, konnect_sexp::SexpError> {
    let items = konnect_sexp::item_locations(content)?;
    Ok(items
        .into_iter()
        .find(|item| item.id.as_str() == uuid)
        .map(|item| (item.start, item.end, item.kind)))
}

/// As [`find_schematic_item_by_uuid`], but including any leading
/// whitespace/newline before the block, for callers that delete the item.
///
/// # Errors
///
/// See [`find_schematic_item_by_uuid`].
pub(crate) fn find_schematic_item_block_for_delete(
    content: &str,
    uuid: &str,
) -> Result<Option<(usize, usize, Option<String>)>, konnect_sexp::SexpError> {
    let Some((start, _end, kind)) = find_schematic_item_by_uuid(content, uuid)? else {
        return Ok(None);
    };
    Ok(
        konnect_sexp::writer::find_block_with_leading_whitespace(content, start)
            .map(|(ws_start, end)| (ws_start, end, kind)),
    )
}

/// Resolve a `uuid` to one top-level item of an expected kind (D.4.1.4).
///
/// `kinds` is the set of s-expression tags the calling tool edits — three for
/// a label, one for a wire or a no-connect. A uuid that names a real item of
/// some *other* kind is `NotFound`, never a wrong-kind edit: the caller asked
/// for a no-connect and there is none at that address.
///
/// Returns the item's own byte range in `content`, invalidated by any edit to
/// that string like every other offset here.
///
/// # Errors
///
/// `MalformedDocument` when `content` cannot be indexed; `NotFound` (with the
/// document's uuids of the requested kinds as candidates) when nothing of that
/// kind carries the uuid.
pub(crate) fn resolve_item_by_uuid(
    content: &str,
    uuid: &str,
    kinds: &[&str],
    item_kind: &str,
    sch_path: &std::path::Path,
) -> Result<(usize, usize), Box<crate::mcp::protocol::CallToolResult>> {
    use crate::mcp::error::ToolErrorKind;
    use crate::mcp::protocol::CallToolResult;

    let items = match konnect_sexp::item_locations(content) {
        Ok(items) => items,
        Err(err) => {
            return Err(Box::new(CallToolResult::error_kind(
                ToolErrorKind::MalformedDocument {
                    path: sch_path.display().to_string(),
                    detail: err.to_string(),
                },
                "Cannot parse schematic document",
            )))
        }
    };
    let of_kind = |item: &konnect_sexp::ItemLocation| {
        item.kind
            .as_deref()
            .is_some_and(|kind| kinds.contains(&kind))
    };
    match items
        .iter()
        .find(|item| item.id.as_str() == uuid && of_kind(item))
    {
        Some(item) => Ok((item.start, item.end)),
        None => Err(Box::new(CallToolResult::error_kind(
            ToolErrorKind::NotFound {
                document: sch_path.display().to_string(),
                item_kind: item_kind.to_string(),
                key: uuid.to_string(),
                candidates: items
                    .iter()
                    .filter(|item| of_kind(item))
                    .map(|item| item.id.as_str().to_string())
                    .collect(),
            },
            format!("No {item_kind} with UUID '{uuid}' in schematic"),
        ))),
    }
}

/// A component address that resolved: which symbol instance the call meant,
/// however it was named.
///
/// `reference` is read out of the resolved block, never echoed from the
/// request, so a `uuid`-addressed call and a `reference`-addressed call hand
/// the same string to everything downstream.
#[derive(Debug, Clone, PartialEq, Eq)]
pub(crate) struct ResolvedComponent {
    pub reference: String,
    /// Byte range of the symbol's own block in the `content` it was resolved
    /// against — invalidated by any edit to that string, like every other
    /// offset in this module.
    pub start: usize,
    pub end: usize,
}

/// Resolve `reference` or `uuid` — whichever the call carries — to one symbol
/// instance (D.4.1.2).
///
/// `reference` wins when both are present: it is the form every existing
/// caller uses, and a call that names both and means two different symbols is
/// a caller bug, not an address to guess at (INV8 keeps the old form working
/// unchanged).
///
/// A `uuid` that names a real item of the wrong kind is `NotFound` with
/// `item_kind: "component"`, not a wrong-kind edit: the caller asked for a
/// component and there is none at that address.
///
/// # Errors
///
/// Returns the `CallToolResult` to hand back: `InvalidArgument` when neither
/// form is present, `NotFound` (with the document's symbol UUIDs as
/// candidates) when the address resolves to nothing, `MalformedDocument` when
/// `content` cannot be indexed.
pub(crate) fn resolve_component(
    content: &str,
    args: &serde_json::Value,
    sch_path: &std::path::Path,
) -> Result<ResolvedComponent, Box<crate::mcp::protocol::CallToolResult>> {
    use crate::mcp::error::ToolErrorKind;
    use crate::mcp::protocol::CallToolResult;

    if let Some(reference) = opt_str(args, "reference") {
        let Some((start, end)) = find_symbol_instance_block(content, reference) else {
            return Err(Box::new(CallToolResult::error_kind(
                ToolErrorKind::NotFound {
                    document: sch_path.display().to_string(),
                    item_kind: "component".to_string(),
                    key: reference.to_string(),
                    candidates: Vec::new(),
                },
                format!("Component '{reference}' not found in schematic"),
            )));
        };
        return Ok(ResolvedComponent {
            reference: reference.to_string(),
            start,
            end,
        });
    }

    let Some(uuid) = opt_str(args, "uuid") else {
        return Err(Box::new(CallToolResult::error_kind(
            ToolErrorKind::InvalidArgument {
                field: "reference".to_string(),
                reason: "one of 'reference' or 'uuid' is required to address a component"
                    .to_string(),
            },
            "Missing component address: pass 'reference' or 'uuid'",
        )));
    };

    let items = match konnect_sexp::item_locations(content) {
        Ok(items) => items,
        Err(err) => {
            return Err(Box::new(CallToolResult::error_kind(
                ToolErrorKind::MalformedDocument {
                    path: sch_path.display().to_string(),
                    detail: err.to_string(),
                },
                "Cannot parse schematic document",
            )))
        }
    };

    match items
        .iter()
        .find(|item| item.id.as_str() == uuid && item.kind.as_deref() == Some("symbol"))
    {
        Some(item) => {
            let Some(reference) = symbol_block_reference(&content[item.start..item.end]) else {
                return Err(Box::new(CallToolResult::error_kind(
                    ToolErrorKind::MalformedDocument {
                        path: sch_path.display().to_string(),
                        detail: format!("symbol '{uuid}' carries no Reference property"),
                    },
                    format!("Symbol '{uuid}' has no reference designator"),
                )));
            };
            Ok(ResolvedComponent {
                reference,
                start: item.start,
                end: item.end,
            })
        }
        None => Err(Box::new(CallToolResult::error_kind(
            ToolErrorKind::NotFound {
                document: sch_path.display().to_string(),
                item_kind: "component".to_string(),
                key: uuid.to_string(),
                candidates: items
                    .iter()
                    .filter(|item| item.kind.as_deref() == Some("symbol"))
                    .map(|item| item.id.as_str().to_string())
                    .collect(),
            },
            format!("No component with UUID '{uuid}' in schematic"),
        ))),
    }
}

/// Every symbol in `content` by its own direct-child `uuid`, mapped to the
/// designator that symbol carries (D.4.1.6).
///
/// Indexed once for a whole batch, like `handle_batch_delete_wire`: every
/// lookup in one call shares the same document. A uuid on an item of another
/// kind is simply absent from the map, so no caller can edit the wrong item.
///
/// # Errors
///
/// `MalformedDocument` when `content` cannot be indexed.
pub(crate) fn symbol_references_by_uuid(
    content: &str,
    sch_path: &std::path::Path,
) -> Result<std::collections::HashMap<String, String>, Box<crate::mcp::protocol::CallToolResult>> {
    use crate::mcp::error::ToolErrorKind;
    use crate::mcp::protocol::CallToolResult;

    let items = match konnect_sexp::item_locations(content) {
        Ok(items) => items,
        Err(err) => {
            return Err(Box::new(CallToolResult::error_kind(
                ToolErrorKind::MalformedDocument {
                    path: sch_path.display().to_string(),
                    detail: err.to_string(),
                },
                "Cannot parse schematic document",
            )))
        }
    };
    Ok(items
        .iter()
        .filter(|item| item.kind.as_deref() == Some("symbol"))
        .filter_map(|item| {
            symbol_block_reference(&content[item.start..item.end])
                .map(|reference| (item.id.as_str().to_string(), reference))
        })
        .collect())
}

/// The one wording every plural tool reports an unresolvable component uuid
/// with, so the same address failing in two tools reads the same.
pub(crate) fn no_component_with_uuid(uuid: &str) -> String {
    format!("No component with UUID '{uuid}' in schematic")
}

/// The component addresses one plural call names (D.4.1.6).
///
/// `references` holds the designators to act on, every `references` entry in
/// call order first — evaluated without reading anything, exactly as before —
/// then every `uuids` entry that resolved, deduplicated so an item named by
/// both forms is acted on once.
pub(crate) struct ComponentBatch {
    pub references: Vec<String>,
    /// One message per `uuids` entry that named no symbol: a uuid absent from
    /// the document, or present on an item of another kind.
    pub unresolved: Vec<String>,
}

/// Resolve the `references` / `uuids` pair of a plural component tool.
///
/// The two arrays are accepted together and the result is their union: a
/// caller migrating one address at a time never has to choose. Nothing is
/// translated into the other form — a `references` entry is passed through
/// untouched, so the historical path keeps its own not-found reporting.
///
/// # Errors
///
/// `InvalidArgument` when neither array is present (or one is present but is
/// not an array), `MalformedDocument` when `uuids` are given and `content`
/// cannot be indexed.
pub(crate) fn resolve_component_batch(
    content: &str,
    args: &serde_json::Value,
    sch_path: &std::path::Path,
) -> Result<ComponentBatch, Box<crate::mcp::protocol::CallToolResult>> {
    use crate::mcp::error::ToolErrorKind;
    use crate::mcp::protocol::CallToolResult;

    let array = |field: &str| -> Result<Vec<String>, Box<CallToolResult>> {
        match &args[field] {
            serde_json::Value::Null => Ok(Vec::new()),
            serde_json::Value::Array(items) => Ok(items
                .iter()
                .filter_map(|v| v.as_str().map(String::from))
                .collect()),
            _ => Err(Box::new(CallToolResult::error_kind(
                ToolErrorKind::InvalidArgument {
                    field: field.to_string(),
                    reason: "must be an array".to_string(),
                },
                format!("Missing '{field}' array"),
            ))),
        }
    };
    let references = array("references")?;
    let uuids = array("uuids")?;
    if args["references"].is_null() && args["uuids"].is_null() {
        return Err(Box::new(CallToolResult::error_kind(
            ToolErrorKind::InvalidArgument {
                field: "references".to_string(),
                reason: "one of 'references' or 'uuids' is required to address components"
                    .to_string(),
            },
            "Missing component addresses: pass 'references' or 'uuids'",
        )));
    }

    let mut batch = ComponentBatch {
        references,
        unresolved: Vec::new(),
    };
    if uuids.is_empty() {
        // Nothing to merge, so the historical list is passed through exactly
        // as it arrived — duplicates included, as it always behaved.
        return Ok(batch);
    }

    let by_uuid = symbol_references_by_uuid(content, sch_path)?;
    for uuid in &uuids {
        match by_uuid.get(uuid.as_str()) {
            Some(reference) => batch.references.push(reference.clone()),
            // A uuid on an item of another kind lands here too: the caller
            // asked for a component and there is none at that address.
            None => batch.unresolved.push(no_component_with_uuid(uuid)),
        }
    }
    let mut seen = std::collections::HashSet::new();
    batch
        .references
        .retain(|reference| seen.insert(reference.clone()));
    Ok(batch)
}

/// The `Reference` property value of one symbol block, by the same textual
/// shape [`find_symbol_instance_block`] searches for.
fn symbol_block_reference(block: &str) -> Option<String> {
    const NEEDLE: &str = r#"(property "Reference" ""#;
    let start = block.find(NEEDLE)? + NEEDLE.len();
    let end = start + block[start..].find('"')?;
    Some(block[start..end].to_string())
}

#[cfg(test)]
mod schematic_item_lookup_tests {
    use super::*;

    const SCH: &str = "(kicad_sch\n\t(version 20260306)\n\t(wire\n\t\t(pts (xy 0 0) (xy 10 0))\n\t\t(uuid \"11111111-1111-1111-1111-111111111111\")\n\t)\n\t(sheet\n\t\t(at 0 0)\n\t\t(uuid \"22222222-2222-2222-2222-222222222222\")\n\t\t(pin \"Name\" input (at 0 0 0)\n\t\t\t(uuid \"33333333-3333-3333-3333-333333333333\")\n\t\t)\n\t)\n)\n";

    #[test]
    fn finds_own_uuid_with_kind() {
        let (start, end, kind) =
            find_schematic_item_by_uuid(SCH, "11111111-1111-1111-1111-111111111111")
                .expect("indexable")
                .expect("found");
        assert_eq!(kind.as_deref(), Some("wire"));
        assert!(SCH[start..end].starts_with("(wire"));
    }

    #[test]
    fn does_not_match_a_nested_uuid() {
        // A sheet pin's own UUID must not resolve to the enclosing sheet:
        // that identity belongs to the pin, not the top-level item.
        assert_eq!(
            find_schematic_item_by_uuid(SCH, "33333333-3333-3333-3333-333333333333")
                .expect("indexable"),
            None
        );
    }

    #[test]
    fn unknown_uuid_is_none() {
        assert_eq!(
            find_schematic_item_by_uuid(SCH, "ffffffff-ffff-ffff-ffff-ffffffffffff")
                .expect("indexable"),
            None
        );
    }

    #[test]
    fn delete_variant_includes_leading_whitespace() {
        let (start, end, kind) =
            find_schematic_item_block_for_delete(SCH, "11111111-1111-1111-1111-111111111111")
                .expect("indexable")
                .expect("found");
        assert_eq!(kind.as_deref(), Some("wire"));
        assert!(SCH[start..end].starts_with('\n'));
        assert!(SCH[start..end].trim_start().starts_with("(wire"));
    }
}

#[cfg(test)]
mod symbol_block_tests {
    use super::*;

    /// Instance blocks as eeschema writes them: tab-indented, and preceded by a
    /// lib_symbols definition carrying its own Reference property.
    const EESCHEMA_STYLE: &str = "(kicad_sch\n\t(lib_symbols\n\t\t(symbol \"Device:R\"\n\t\t\t(property \"Reference\" \"R\"\n\t\t\t\t(at 2.032 0 90)\n\t\t\t)\n\t\t)\n\t)\n\t(symbol\n\t\t(lib_id \"Device:R\")\n\t\t(at 100 80 0)\n\t\t(property \"Reference\" \"R1\"\n\t\t\t(at 102 78 0)\n\t\t)\n\t\t(property \"Value\" \"10k\"\n\t\t\t(at 102 82 0)\n\t\t)\n\t)\n)\n";

    /// Same shape, two-space indented, as this crate's writer emits.
    const KONNECT_STYLE: &str = "(kicad_sch\n  (lib_symbols\n    (symbol \"Device:R\"\n      (property \"Reference\" \"R\"\n        (at 2.032 0 90)\n      )\n    )\n  )\n  (symbol\n    (lib_id \"Device:R\")\n    (at 100 80 0)\n    (property \"Reference\" \"R1\"\n      (at 102 78 0)\n    )\n  )\n)\n";

    #[test]
    fn finds_instance_in_tab_indented_file() {
        let (start, end) = find_symbol_instance_block(EESCHEMA_STYLE, "R1").expect("R1 block");
        let block = &EESCHEMA_STYLE[start..end];
        assert!(block.starts_with("(symbol"));
        assert!(block.contains("(lib_id \"Device:R\")"));
        assert!(block.contains("\"R1\""));
        assert!(
            block.contains("\"10k\""),
            "block must span the whole symbol"
        );
    }

    #[test]
    fn finds_instance_in_space_indented_file() {
        let (start, end) = find_symbol_instance_block(KONNECT_STYLE, "R1").expect("R1 block");
        assert!(KONNECT_STYLE[start..end].contains("(lib_id \"Device:R\")"));
    }

    #[test]
    fn library_definition_is_not_mistaken_for_an_instance() {
        // A hand-authored library whose default Reference matches a placed
        // instance's designator must not shadow the instance.
        let sch = "(kicad_sch\n\t(lib_symbols\n\t\t(symbol \"Custom:Thing\"\n\t\t\t(property \"Reference\" \"U1\"\n\t\t\t\t(at 0 0 0)\n\t\t\t)\n\t\t)\n\t)\n\t(symbol\n\t\t(lib_id \"Custom:Thing\")\n\t\t(property \"Reference\" \"U1\"\n\t\t\t(at 5 5 0)\n\t\t)\n\t)\n)\n";
        let (start, end) = find_symbol_instance_block(sch, "U1").expect("instance");
        assert!(
            sch[start..end].contains("(lib_id "),
            "must skip the lib_symbols definition and return the placed instance"
        );
    }

    #[test]
    fn unknown_reference_is_none() {
        assert!(find_symbol_instance_block(EESCHEMA_STYLE, "R99").is_none());
    }

    #[test]
    fn reference_prefix_does_not_match_longer_designator() {
        // "R1" must not match the R12 instance.
        let sch = "(kicad_sch\n\t(symbol\n\t\t(lib_id \"Device:R\")\n\t\t(property \"Reference\" \"R12\"\n\t\t\t(at 1 1 0)\n\t\t)\n\t)\n)\n";
        assert!(find_symbol_instance_block(sch, "R1").is_none());
    }
}

#[cfg(test)]
mod symbol_property_tests {
    use super::*;

    /// A placed instance, tab-indented like eeschema writes one (P.6.9.4),
    /// with a `Note` property whose *value* contains the literal text
    /// `(property "Sku" "` — the exact pattern a naive `str::find` for
    /// `(property "Sku" "` would be fooled by — quoted with the escaped-quote
    /// shape KiCad itself uses (measured on `CM5.kicad_sch`'s `Description`
    /// property, which carries an escaped `"GND"` the same way).
    const TAB_INDENTED: &str = "(kicad_sch\n\t(symbol\n\t\t(lib_id \"Device:R\")\n\t\t(at 100 80 0)\n\t\t(uuid \"u1\")\n\t\t(property \"Reference\" \"R1\"\n\t\t\t(at 102 78 0)\n\t\t\t(effects (font (size 1.27 1.27)))\n\t\t)\n\t\t(property \"Value\" \"10k\"\n\t\t\t(at 102 82 0)\n\t\t\t(effects (font (size 1.27 1.27)))\n\t\t)\n\t\t(property \"Note\" \"has (property \\\"Sku\\\" \\\"nested\"\n\t\t\t(at 100 80 0)\n\t\t\t(hide yes)\n\t\t\t(effects (font (size 1.27 1.27)))\n\t\t)\n\t\t(instances\n\t\t\t(project \"p\" (path \"/root\" (reference \"R1\") (unit 1)))\n\t\t)\n\t)\n)\n";

    const SPACE_INDENTED: &str = "(kicad_sch\n  (symbol\n    (lib_id \"Device:R\")\n    (at 100 80 0)\n    (uuid \"u1\")\n    (property \"Reference\" \"R1\"\n      (at 102 78 0)\n      (effects (font (size 1.27 1.27)))\n    )\n    (property \"Value\" \"10k\"\n      (at 102 82 0)\n      (effects (font (size 1.27 1.27)))\n    )\n    (instances\n      (project \"p\" (path \"/root\" (reference \"R1\") (unit 1)))\n    )\n  )\n)\n";

    fn sym_range(content: &str) -> (usize, usize) {
        find_symbol_instance_block(content, "R1").expect("R1 block")
    }

    #[test]
    fn find_symbol_property_is_not_derailed_by_a_lookalike_value() {
        let (start, end) = sym_range(TAB_INDENTED);
        // Before the fix, a naive `find("(property \"Sku\" \"")` would match
        // inside `Note`'s value and report a phantom `Sku` property.
        assert!(
            find_symbol_property(TAB_INDENTED, start, end, "Sku").is_none(),
            "the lookalike text inside Note's value must not be found as a real property"
        );
        // The real property must still be found correctly despite the decoy.
        let value = find_symbol_property(TAB_INDENTED, start, end, "Value").expect("Value");
        assert_eq!(&TAB_INDENTED[value.value_start..value.value_end], "10k");
    }

    #[test]
    fn quoted_string_after_honors_escaped_quotes() {
        let s = r#""a \"quoted\" word""#;
        let (start, end) = quoted_string_after(s, 0).expect("span");
        assert_eq!(&s[start..end], r#"a \"quoted\" word"#);
    }

    #[test]
    fn set_symbol_property_updates_existing_value_in_place() {
        let (start, end) = sym_range(TAB_INDENTED);
        let (updated, outcome) =
            set_symbol_property(TAB_INDENTED, start, end, "Value", "4k7", &[]).expect("update");
        assert!(matches!(outcome, SetPropertyOutcome::Updated));
        assert_eq!(
            updated.matches("(property \"Value\" ").count(),
            1,
            "still exactly one Value property"
        );
        assert!(updated.contains("(property \"Value\" \"4k7\""));
        // The decoy text in Note survives untouched.
        assert!(updated.contains(r#"has (property \"Sku\" \"nested"#));
    }

    #[test]
    fn set_symbol_property_inserts_missing_property_with_matching_indentation() {
        let (start, end) = sym_range(TAB_INDENTED);
        let (updated, outcome) =
            set_symbol_property(TAB_INDENTED, start, end, "MPN", "RC0805", &[]).expect("insert");
        assert!(matches!(outcome, SetPropertyOutcome::Inserted));
        let idx = updated
            .find("(property \"MPN\" \"RC0805\"")
            .expect("inserted property");
        let line_start = updated[..idx].rfind('\n').map(|p| p + 1).unwrap_or(0);
        assert!(
            updated[line_start..idx].chars().all(|c| c == '\t'),
            "inserted property must be tab-indented to match the surrounding tab-indented block: {:?}",
            &updated[line_start..idx]
        );
        // Anchor is the symbol's own position (100 80), not the origin.
        assert!(
            updated.contains("(at 100 80 0)\n\t\t\t(effects"),
            "new hidden property must anchor at the symbol's own position: {updated}"
        );
    }

    #[test]
    fn set_symbol_property_inserts_missing_property_with_space_indentation() {
        let (start, end) = sym_range(SPACE_INDENTED);
        let (updated, _) =
            set_symbol_property(SPACE_INDENTED, start, end, "MPN", "RC0805", &[]).expect("insert");
        let idx = updated
            .find("(property \"MPN\" \"RC0805\"")
            .expect("inserted property");
        let line_start = updated[..idx].rfind('\n').map(|p| p + 1).unwrap_or(0);
        assert!(
            !updated[line_start..idx].contains('\t'),
            "a space-indented file must not gain a tab-indented insertion: {:?}",
            &updated[line_start..idx]
        );
    }

    #[test]
    fn set_symbol_property_refuses_reserved_keys() {
        let (start, end) = sym_range(TAB_INDENTED);
        let err = set_symbol_property(TAB_INDENTED, start, end, "Reference", "R9", &["Reference"])
            .unwrap_err();
        assert!(matches!(err, SetPropertyError::Reserved(_)));
    }

    #[test]
    fn symbol_property_at_spans_finds_every_property_anchor() {
        let (start, end) = sym_range(TAB_INDENTED);
        let spans = symbol_property_at_spans(TAB_INDENTED, start, end);
        // Reference, Value, Note: three properties, three anchors, and the
        // decoy `(property "Sku" "...` text inside Note's value must not
        // contribute a fourth.
        assert_eq!(spans.len(), 3, "{spans:?}");
        let texts: Vec<&str> = spans.iter().map(|&(s, e)| &TAB_INDENTED[s..e]).collect();
        assert!(texts.contains(&"102 78 0"));
        assert!(texts.contains(&"102 82 0"));
        assert!(texts.contains(&"100 80 0"));
    }
}

#[cfg(test)]
mod arg_helper_tests {
    use super::*;
    use crate::mcp::error::extract_error_kind;
    use serde_json::json;

    #[test]
    fn require_str_missing_produces_structured_invalid_argument() {
        let args = json!({});
        let err = require_str(&args, "path").expect_err("should fail");
        assert!(err.is_error);
        assert_eq!(
            extract_error_kind(&err).as_deref(),
            Some("invalid_argument")
        );
        // The body carries the field name so clients can branch.
        let body = match &err.content[0] {
            crate::mcp::protocol::ToolContent::Text { text } => text.clone(),
            _ => panic!(),
        };
        let parsed: serde_json::Value = serde_json::from_str(&body).unwrap();
        assert_eq!(parsed["error"]["field"], "path");
    }

    #[test]
    fn require_f64_non_number_produces_structured_invalid_argument() {
        let args = json!({ "x": "not a number" });
        let err = require_f64(&args, "x").expect_err("should fail");
        assert_eq!(
            extract_error_kind(&err).as_deref(),
            Some("invalid_argument")
        );
    }

    /// The `anyhow` helper says the same thing as `require_str`, by type: the
    /// marker rides the chain and `from_anyhow` downcasts it. No assertion
    /// here reads the message, which is the point — a classifier that matched
    /// text would pass this too, and would break the first time the prose
    /// changed.
    #[test]
    fn get_path_missing_classifies_as_invalid_argument_by_type() {
        let args = json!({});
        let err = get_path(&args, "board").expect_err("no board key");
        assert!(err.chain().any(|cause| cause
            .downcast_ref::<crate::mcp::error::MissingArgument>()
            .is_some()));
        match crate::mcp::error::ToolErrorKind::from_anyhow(&err) {
            crate::mcp::error::ToolErrorKind::InvalidArgument { field, .. } => {
                assert_eq!(field, "board")
            }
            other => panic!("an argument nobody supplied is not a handler failure: {other:?}"),
        }
    }

    /// An unrelated failure is untouched: only the marker reclassifies, so a
    /// tool that tried and failed keeps the classification it already had.
    #[test]
    fn an_error_without_the_marker_is_not_reclassified() {
        let err = anyhow::anyhow!("the tool tried and failed");
        assert!(!matches!(
            crate::mcp::error::ToolErrorKind::from_anyhow(&err),
            crate::mcp::error::ToolErrorKind::InvalidArgument { .. }
        ));
    }

    #[test]
    fn get_path_present_returns_the_path() {
        let args = json!({ "board": "b.kicad_pcb" });
        let path = get_path(&args, "board").expect("present");
        assert_eq!(path, std::path::PathBuf::from("b.kicad_pcb"));
    }

    #[test]
    fn require_str_present_returns_value() {
        let args = json!({ "name": "ok" });
        let v = require_str(&args, "name").expect("should parse");
        assert_eq!(v, "ok");
    }

    #[test]
    fn require_array_present_returns_its_elements() {
        let args = json!({ "layers": ["Edge.Cuts", "F.Cu"] });
        let v = require_array(&args, "layers").expect("should parse");
        assert_eq!(v.len(), 2);
        assert_eq!(v[0], "Edge.Cuts");
    }

    /// An empty list is something the caller said, not something they omitted,
    /// so it survives the check that absence does not.
    #[test]
    fn require_array_accepts_an_explicitly_empty_array() {
        let args = json!({ "pads": [] });
        let v = require_array(&args, "pads").expect("an empty array is a value");
        assert!(v.is_empty());
    }

    #[test]
    fn require_array_missing_produces_structured_invalid_argument() {
        let args = json!({});
        let err = require_array(&args, "pads").expect_err("should fail");
        assert_eq!(
            extract_error_kind(&err).as_deref(),
            Some("invalid_argument")
        );
        let body = match &err.content[0] {
            crate::mcp::protocol::ToolContent::Text { text } => text.clone(),
            _ => panic!(),
        };
        let parsed: serde_json::Value = serde_json::from_str(&body).unwrap();
        assert_eq!(parsed["error"]["field"], "pads");
    }

    #[test]
    fn require_array_non_array_is_refused() {
        let args = json!({ "pads": "1,2" });
        let err = require_array(&args, "pads").expect_err("should fail");
        assert_eq!(
            extract_error_kind(&err).as_deref(),
            Some("invalid_argument")
        );
    }

    #[test]
    fn require_u64_present_returns_value() {
        let args = json!({ "count_x": 4 });
        assert_eq!(require_u64(&args, "count_x").expect("should parse"), 4);
    }

    #[test]
    fn require_u64_missing_produces_structured_invalid_argument() {
        let args = json!({});
        let err = require_u64(&args, "count_x").expect_err("should fail");
        assert_eq!(
            extract_error_kind(&err).as_deref(),
            Some("invalid_argument")
        );
        let body = match &err.content[0] {
            crate::mcp::protocol::ToolContent::Text { text } => text.clone(),
            _ => panic!(),
        };
        let parsed: serde_json::Value = serde_json::from_str(&body).unwrap();
        assert_eq!(parsed["error"]["field"], "count_x");
    }

    /// A negative or fractional count is not an unsigned integer, and guessing
    /// one from it would be the substitution this helper exists to stop.
    #[test]
    fn require_u64_non_integer_is_refused() {
        for bad in [json!("4"), json!(-1), json!(2.5)] {
            let args = json!({ "count_x": bad });
            let err = require_u64(&args, "count_x").expect_err("should fail");
            assert_eq!(
                extract_error_kind(&err).as_deref(),
                Some("invalid_argument")
            );
        }
    }
}

// ─── KiCAD config directory detection ────────────────────────────────────────

/// Find the KiCAD user config directory by probing for installed version directories.
/// Checks versions in descending order: 10.0, 9.0, 8.0, then bare "kicad".
pub fn kicad_config_dir() -> std::path::PathBuf {
    let base = kicad_config_base();
    let versions = ["10.0", "9.0", "8.0"];
    for ver in &versions {
        let dir = base.join(ver);
        if dir.is_dir() {
            return dir;
        }
    }
    // Fallback: bare kicad dir or 10.0 (will be created on first use)
    base.join("10.0")
}

/// Platform-specific base directory for KiCAD configs.
fn kicad_config_base() -> std::path::PathBuf {
    #[cfg(target_os = "windows")]
    {
        let appdata = std::env::var("APPDATA").unwrap_or_default();
        std::path::PathBuf::from(appdata).join("kicad")
    }
    #[cfg(target_os = "macos")]
    {
        let home = std::env::var("HOME").unwrap_or_default();
        std::path::PathBuf::from(home)
            .join("Library")
            .join("Preferences")
            .join("kicad")
    }
    #[cfg(not(any(target_os = "windows", target_os = "macos")))]
    {
        let home = std::env::var("HOME").unwrap_or_default();
        std::path::PathBuf::from(home).join(".config").join("kicad")
    }
}

// ─── KiCAD symbol library resolution ────────────────────────────────────────

/// Resolve a lib_id like "Device:R" to the full symbol S-expression definition.
/// KiCAD 10 stores symbols in .kicad_symdir directories, one .kicad_sym file per symbol.
/// Returns the symbol block with the lib_id prefix (e.g. "Device:R") as the symbol name.
pub fn resolve_lib_symbol(lib_id: &str) -> Option<String> {
    let parts: Vec<&str> = lib_id.splitn(2, ':').collect();
    if parts.len() != 2 {
        tracing::warn!(
            "[BETA] Cannot resolve lib_id '{}' — expected 'Library:Symbol' format",
            lib_id
        );
        return None;
    }
    let (library_name, symbol_name) = (parts[0], parts[1]);

    let sym_dirs = find_kicad_symbol_dirs();

    for base_dir in &sym_dirs {
        // KiCAD 10: Library.kicad_symdir/SymbolName.kicad_sym
        let symdir_path = base_dir.join(format!("{}.kicad_symdir", library_name));
        let sym_file = symdir_path.join(format!("{}.kicad_sym", symbol_name));

        if sym_file.exists() {
            tracing::debug!("[BETA] Found symbol file: {}", sym_file.display());
            match std::fs::read_to_string(&sym_file) {
                Ok(content) => {
                    if let Some(sym_block) = extract_symbol_block(&content, symbol_name) {
                        let renamed = sym_block.replacen(
                            &format!("(symbol \"{}\"", symbol_name),
                            &format!("(symbol \"{}:{}\"", library_name, symbol_name),
                            1,
                        );
                        return Some(renamed);
                    }
                }
                Err(e) => tracing::warn!("[BETA] Failed to read {}: {}", sym_file.display(), e),
            }
        }

        // Fallback: KiCAD 8/9 format — Library.kicad_sym (single file)
        let legacy_path = base_dir.join(format!("{}.kicad_sym", library_name));
        if legacy_path.exists() {
            match std::fs::read_to_string(&legacy_path) {
                Ok(content) => {
                    if let Some(sym_block) = extract_symbol_block(&content, symbol_name) {
                        let renamed = sym_block.replacen(
                            &format!("(symbol \"{}\"", symbol_name),
                            &format!("(symbol \"{}:{}\"", library_name, symbol_name),
                            1,
                        );
                        return Some(renamed);
                    }
                }
                Err(e) => tracing::warn!("[BETA] Failed to read {}: {}", legacy_path.display(), e),
            }
        }
    }

    tracing::warn!(
        "[BETA] Symbol '{}' not found in any library directory",
        lib_id
    );
    None
}

/// Extract a top-level (symbol "NAME" ...) block from a .kicad_sym file.
fn extract_symbol_block(content: &str, symbol_name: &str) -> Option<String> {
    let pattern = format!("(symbol \"{}\"", symbol_name);
    let start = content.find(&pattern)?;
    let mut depth = 0i32;
    let mut end = start;
    for (i, ch) in content[start..].char_indices() {
        match ch {
            '(' => depth += 1,
            ')' => {
                depth -= 1;
                if depth == 0 {
                    end = start + i + 1;
                    break;
                }
            }
            _ => {}
        }
    }
    if end > start {
        Some(content[start..end].to_string())
    } else {
        None
    }
}

/// Structured "this lib_id doesn't exist" error, with did-you-mean hints —
/// silently accepting an unresolvable lib_id writes a netlist-invisible
/// component with an empty pin list (#34).
pub fn lib_symbol_not_found_error(lib_id: &str) -> CallToolResult {
    let library = lib_id.split(':').next().unwrap_or(lib_id);
    // Which of the two is missing decides `item_kind`, and the message already
    // branched on it: a library nobody installed and a symbol that library does
    // not contain are different repairs.
    let library_missing = !konnect_schematic_editor::library::library_exists(library);
    let mut msg = if library_missing {
        format!(
            "Library '{}' not found in the installed KiCAD symbol libraries \
             (lib_id '{}'). Check the library name, the KiCAD install, or \
             KICAD10_SYMBOL_DIR.",
            library, lib_id
        )
    } else {
        format!(
            "Library symbol '{}' not found in the installed KiCAD libraries.",
            lib_id
        )
    };
    let suggestions = konnect_schematic_editor::library::suggest_symbols(lib_id, 3);
    if !suggestions.is_empty() {
        msg.push_str(&format!(
            " Did you mean: {}? (KiCAD 10 renamed several older symbol names)",
            suggestions.join(", ")
        ));
    }
    // Structured candidates, capped small, for a repair pass or the LLM to act
    // on directly — a deterministic lookup over the installed libraries, never
    // a guess: nothing here is auto-substituted for the lib_id the caller
    // asked for. Computed only here, on the failure path; a successful
    // placement never calls this.
    let candidates = konnect_schematic_editor::library::suggest_lib_ids(lib_id, 8);
    CallToolResult::error_kind(
        crate::mcp::error::ToolErrorKind::NotFound {
            document: "installed KiCAD symbol libraries".to_string(),
            item_kind: if library_missing { "library" } else { "symbol" }.to_string(),
            key: lib_id.to_string(),
            candidates,
        },
        msg,
    )
}

/// Insert a symbol definition into the schematic's lib_symbols section.
/// Creates the lib_symbols section if it doesn't exist. Skips if already present.
///
/// Returns `false` when `lib_id` cannot be resolved — callers must surface
/// that as an error rather than writing a definition-less instance (#34).
#[must_use]
pub fn ensure_lib_symbol_in_schematic(content: &mut String, lib_id: &str) -> bool {
    // Check if already present
    let lib_id_check = format!("(symbol \"{}\"", lib_id);
    if content.contains(&lib_id_check) {
        return true;
    }

    // Resolve the symbol from KiCAD libraries. Prefer the flattened resolver:
    // derived symbols ((extends "Parent")) must be embedded with the parent's
    // units copied in, not as a stub kicad-cli can't netlist (#35). Fall back
    // to the local raw resolver for parity with the pre-flattening behavior.
    let sym_def = match konnect_schematic_editor::library::resolve_lib_symbol_flattened(lib_id)
        .or_else(|| resolve_lib_symbol(lib_id))
    {
        Some(s) => s,
        None => return false,
    };

    // Ensure lib_symbols section exists
    if !content.contains("(lib_symbols") {
        if let Some(insert_after) = content.find(")\n") {
            content.insert_str(insert_after + 2, "\n\t(lib_symbols\n\t)\n");
        }
    }

    // Find the closing paren of lib_symbols and insert before it
    if let Some(ls_start) = content.find("(lib_symbols") {
        let mut depth = 0i32;
        let mut ls_end = ls_start;
        for (i, ch) in content[ls_start..].char_indices() {
            match ch {
                '(' => depth += 1,
                ')' => {
                    depth -= 1;
                    if depth == 0 {
                        ls_end = ls_start + i;
                        break;
                    }
                }
                _ => {}
            }
        }
        let indented = sym_def
            .lines()
            .map(|l| {
                if l.is_empty() {
                    String::new()
                } else {
                    format!("\t\t{}", l)
                }
            })
            .collect::<Vec<_>>()
            .join("\n");
        content.insert_str(ls_end, &format!("\n{}\n\t", indented));
    }
    true
}

/// Find directories holding a bundled KiCAD library kind — `"symbols"`,
/// `"footprints"` or `"3dmodels"`.
///
/// The matching environment variable wins when KiCad has exported it (it does
/// so for plugins); otherwise the well-known install locations are searched,
/// newest KiCad first. The names are not a plain uppercasing of `kind` — they
/// are singular, and the 3D one is not a word:
///
/// | `kind`        | variable                |
/// |---------------|-------------------------|
/// | `symbols`     | `KICAD<major>_SYMBOL_DIR`    |
/// | `footprints`  | `KICAD<major>_FOOTPRINT_DIR` |
/// | `3dmodels`    | `KICAD<major>_3DMODEL_DIR`   |
pub(crate) fn find_kicad_library_dirs(kind: &str) -> Vec<std::path::PathBuf> {
    konnect_schematic_editor::kicad_paths::library_dirs(kind)
}

/// Find directories where KiCAD symbol libraries are stored.
fn find_kicad_symbol_dirs() -> Vec<std::path::PathBuf> {
    find_kicad_library_dirs("symbols")
}

#[cfg(test)]
mod lib_symbol_not_found_error_tests {
    use super::*;
    use crate::mcp::error::extract_error_kind;
    use crate::mcp::protocol::ToolContent;

    fn error_body(result: &CallToolResult) -> serde_json::Value {
        let ToolContent::Text { text } = &result.content[0] else {
            panic!("structured errors are text content")
        };
        serde_json::from_str(text).expect("structured error body is JSON")
    }

    /// Fixture: one installed library, `Device`, with a single `R` symbol.
    /// Locks `sch_components::tests::SYMBOL_DIR_ENV` — the same
    /// process-global `KICAD10_SYMBOL_DIR` other test modules in this crate
    /// fixture, so this doesn't race them (progress.md: two independent
    /// locks around the same env var don't serialize anything).
    ///
    /// `async` only because that lock is a `tokio` mutex (E10): every other
    /// holder spans an `.await`, and the whole point is that they all queue on
    /// the same one, so the two tests below take it the same way.
    async fn write_device_r_fixture() -> (tempfile::TempDir, tokio::sync::MutexGuard<'static, ()>) {
        let guard = crate::tools::sch_components::tests::SYMBOL_DIR_ENV
            .lock()
            .await;
        let libdir = tempfile::tempdir().unwrap();
        let symdir = libdir.path().join("Device.kicad_symdir");
        std::fs::create_dir_all(&symdir).unwrap();
        std::fs::write(
            symdir.join("R.kicad_sym"),
            "(kicad_symbol_lib\n\t(version 20241209)\n\t(generator \"test\")\n\t(symbol \"R\"\n\t\t(property \"Reference\" \"R\" (at 0 0 0))\n\t\t(property \"Value\" \"R\" (at 0 0 0))\n\t)\n)\n",
        )
        .unwrap();
        std::env::set_var("KICAD10_SYMBOL_DIR", libdir.path());
        (libdir, guard)
    }

    #[tokio::test]
    async fn invented_library_error_carries_the_plausible_real_lib_id() {
        let _fixture = write_device_r_fixture().await;
        let result = lib_symbol_not_found_error("Resistor:R");
        assert!(result.is_error);

        let body = error_body(&result);
        let candidates: Vec<&str> = body["error"]["candidates"]
            .as_array()
            .expect("candidates array present")
            .iter()
            .filter_map(|v| v.as_str())
            .collect();
        assert!(
            candidates.contains(&"Device:R"),
            "expected Device:R among {candidates:?}"
        );
        assert!(candidates.len() <= 8, "candidate list must stay small");
    }

    #[tokio::test]
    async fn candidates_travel_with_a_not_found_rather_than_the_catch_all() {
        // This site answered "handler_error", and an earlier change pinned that
        // so adding structured candidates could not move it. D.6.1 is what
        // moves it, deliberately: a lib_id nobody installed is a NotFound, and
        // the catch-all was only ever reached because `NotFound` had nowhere to
        // put `candidates`. It does now, so the site no longer pays
        // `handler_error`'s "we have not looked at this" contract for one
        // structured field. Both messages are unchanged.
        let _fixture = write_device_r_fixture().await;
        let result = lib_symbol_not_found_error("Resistor:R");
        assert_eq!(extract_error_kind(&result).as_deref(), Some("not_found"));

        let unrelated = lib_symbol_not_found_error("Definitely_Bogus_xyzzy:Nope");
        assert_eq!(extract_error_kind(&unrelated).as_deref(), Some("not_found"));
    }
}
