nevenfo/kicad-agentic-mcp/crates/konnect-core/src/tools/pcb_components.rs

//! `pcb_components` toolset — place, move, rotate, query, and array footprints on the PCB.
//!
//! Most operations use the KiCAD IPC API so they integrate with KiCAD's undo/redo
//! system and don't require a separate file-sync step. `get_board_2d_view` uses
//! kicad-cli to render a PNG.

use crate::mcp::error::ToolErrorKind;
use crate::mcp::protocol::CallToolResult;
use crate::tool;
use crate::tools::ipc_boundary::{guarded_ipc as ipc, ipc_error_result_with, with_ipc};
use crate::tools::library::{
    footprint_lib_nickname_for_dir, is_lib_id, resolve_footprint_path, FootprintPathError,
};
use crate::tools::{get_path, require_f64, require_str, require_u64, ToolContext, ToolDef};
use crate::try_arg;
use anyhow::Context;
use konnect_sexp::writer::{
    apply_edits, find_balanced_block, find_block_starts, find_direct_child_blocks, new_uuid,
    read_consistent, write_atomic, write_atomic_if_unchanged,
};
use konnect_sexp::SexpEdit;
use serde_json::json;
use std::collections::{HashMap, HashSet};
use std::path::Path;

// ─── IPC helper ───────────────────────────────────────────────────────────────
//
// P.6.9.22: `ipc!` used to be defined here, board-guarded. It now lives once,
// shared with `pcb_routing.rs`, in `ipc_boundary::guarded_ipc` — see that
// macro's doc comment for why two copies is what let one of them diverge.

// ─── Footprint-library resolution ───────────────────────────────────────────

/// Read the library source of `lib_id` (`Library:Footprint`), resolving it
/// through the project's fp-lib-table (the board's directory), then the global
/// table, then the conventional KiCad library directories — the lookup that
/// `library::resolve_footprint_path` owns.
fn resolve_footprint_source(lib_id: &str, board: &Path) -> anyhow::Result<String> {
    let path = resolve_footprint_file(lib_id, board)?;
    std::fs::read_to_string(&path)
        .map_err(|error| anyhow::anyhow!("failed to read {}: {error}", path.display()))
}

/// The resolution half of [`resolve_footprint_source`], for a caller that
/// reports "does not resolve" and "cannot be read" as different failures.
pub(crate) fn resolve_footprint_file(
    lib_id: &str,
    board_path: &Path,
) -> anyhow::Result<std::path::PathBuf> {
    let (nickname, entry) = lib_id.split_once(':').ok_or_else(|| {
        anyhow::anyhow!("footprint must use Library:Footprint syntax, got '{lib_id}'")
    })?;
    if nickname.is_empty() || entry.is_empty() {
        anyhow::bail!("footprint must use a non-empty Library:Footprint identifier");
    }
    super::library::resolve_footprint_path(lib_id, board_path.parent())
        .map_err(|message| anyhow::anyhow!(message))
}

/// Structured rejection for any back-side (`B.*`) placement layer.
///
/// Placing on the back is not a layer rename: KiCAD's flip mirrors the
/// footprint's geometry (pad X positions negate, every front layer swaps with
/// its back counterpart per item). Until Konnect implements that mirror,
/// pretending to support `B.Cu` silently produces wrong copper, so the layer
/// is refused up front — before anything is resolved, sent, or written.
fn back_side_layer_error(layer: &str) -> Option<CallToolResult> {
    if !layer.starts_with("B.") {
        return None;
    }
    Some(CallToolResult::error_kind(
        crate::mcp::error::ToolErrorKind::InvalidArgument {
            field: "layer".to_string(),
            reason: format!("back-side placement on '{layer}' is not yet supported"),
        },
        format!(
            "Cannot place on '{layer}': back-side placement is not yet supported, \
             because a correct flip must mirror the footprint geometry rather than \
             just rename its layers. Place the footprint on F.Cu and flip it to the \
             back in KiCAD (select it and press F)."
        ),
    ))
}

fn escape_sexp_string(value: &str) -> String {
    value.replace('\\', "\\\\").replace('"', "\\\"")
}

fn replace_quoted_after(source: &mut String, marker: &str, value: &str) -> anyhow::Result<()> {
    let start = source
        .find(marker)
        .map(|offset| offset + marker.len())
        .ok_or_else(|| anyhow::anyhow!("footprint library data is missing {marker}"))?;
    let bytes = source.as_bytes();
    let mut escaped = false;
    let end = (start..bytes.len())
        .find(|index| {
            let byte = bytes[*index];
            if escaped {
                escaped = false;
                false
            } else if byte == b'\\' {
                escaped = true;
                false
            } else {
                byte == b'"'
            }
        })
        .ok_or_else(|| anyhow::anyhow!("unterminated quoted value after {marker}"))?;
    source.replace_range(start..end, &escape_sexp_string(value));
    Ok(())
}

#[allow(clippy::too_many_arguments)]
fn prepare_footprint_source(
    source: &str,
    lib_id: &str,
    reference: &str,
    value: Option<&str>,
    x: f64,
    y: f64,
    rotation: f64,
    layer: &str,
) -> anyhow::Result<String> {
    // No back-side placement: a correct F.Cu→B.Cu flip mirrors the geometry
    // (pad X positions negate, layers swap per item) the way KiCAD's own flip
    // does. A textual layer swap produces wrong copper, so it is refused
    // outright — see back_side_layer_error.
    if layer != "F.Cu" {
        anyhow::bail!(
            "footprints can only be placed on F.Cu (back-side placement is not yet \
             supported because a correct flip must mirror the geometry), got '{layer}'"
        );
    }
    let mut prepared = source.to_string();
    replace_quoted_after(&mut prepared, "(footprint \"", lib_id)?;
    replace_quoted_after(&mut prepared, "(property \"Reference\" \"", reference)?;
    if let Some(value) = value {
        replace_quoted_after(&mut prepared, "(property \"Value\" \"", value)?;
    }
    replace_quoted_after(&mut prepared, "(layer \"", layer)?;
    let layer_start = prepared
        .find("(layer \"")
        .context("footprint library data has no root layer")?;
    let layer_end = prepared[layer_start..]
        .find(')')
        .map(|offset| layer_start + offset + 1)
        .context("footprint root layer is unterminated")?;
    prepared.insert_str(layer_end, &format!("\n\t(at {x} {y} {rotation})"));
    konnect_sexp::parse_sexp(&prepared).context("prepared footprint is not valid S-expression")?;
    Ok(prepared)
}

pub(crate) fn extract_pad_definitions(
    source: &str,
) -> anyhow::Result<Vec<konnect_ipc::IpcPadDefinition>> {
    let footprint = konnect_sexp::parse_sexp(source)?;
    footprint
        .find_all("pad")
        .into_iter()
        .map(|pad| {
            let required = |index: usize, label: &str| {
                pad.get(index)
                    .and_then(konnect_sexp::SexpNode::as_str)
                    .ok_or_else(|| anyhow::anyhow!("footprint pad is missing {label}"))
            };
            let shape = required(3, "shape")?.to_string();
            if shape == "custom" {
                anyhow::bail!(
                    "custom-shape pads are not supported by KiCad 10's typed placement path"
                );
            }
            let at = pad
                .find("at")
                .context("footprint pad is missing its position")?;
            let size = pad
                .find("size")
                .context("footprint pad is missing its size")?;
            let layers = pad
                .find("layers")
                .context("footprint pad is missing its layer set")?
                .children()
                .unwrap_or_default()
                .iter()
                .skip(1)
                .filter_map(konnect_sexp::SexpNode::as_str)
                .map(str::to_string)
                .collect();
            let (drill_x, drill_y, drill_oval) = match pad.find("drill") {
                Some(drill)
                    if drill.get(1).and_then(konnect_sexp::SexpNode::as_str) == Some("oval") =>
                {
                    (
                        drill.get_f64(2),
                        drill.get_f64(3).or_else(|| drill.get_f64(2)),
                        true,
                    )
                }
                Some(drill) => (
                    drill.get_f64(1),
                    drill.get_f64(2).or_else(|| drill.get_f64(1)),
                    false,
                ),
                None => (None, None, false),
            };
            Ok(konnect_ipc::IpcPadDefinition {
                number: required(1, "number")?.to_string(),
                pad_type: required(2, "type")?.to_string(),
                shape,
                x: at
                    .get_f64(1)
                    .context("footprint pad has an invalid X position")?,
                y: at
                    .get_f64(2)
                    .context("footprint pad has an invalid Y position")?,
                rotation: at.get_f64(3).unwrap_or(0.0),
                size_x: size
                    .get_f64(1)
                    .context("footprint pad has an invalid width")?,
                size_y: size
                    .get_f64(2)
                    .context("footprint pad has an invalid height")?,
                drill_x,
                drill_y,
                drill_oval,
                layers,
                roundrect_ratio: pad.find_f64("roundrect_rratio").unwrap_or(0.0),
            })
        })
        .collect()
}

// ─── Footprint graphics extraction ───────────────────────────────────────────

/// `(start x y)`-style point child of a graphic node.
fn graphic_point(
    node: &konnect_sexp::SexpNode,
    tag: &str,
    kind: &str,
) -> anyhow::Result<(f64, f64)> {
    let point = node
        .find(tag)
        .ok_or_else(|| anyhow::anyhow!("footprint {kind} is missing its ({tag} …)"))?;
    Ok((
        point
            .get_f64(1)
            .ok_or_else(|| anyhow::anyhow!("footprint {kind} has an invalid {tag} X"))?,
        point
            .get_f64(2)
            .ok_or_else(|| anyhow::anyhow!("footprint {kind} has an invalid {tag} Y"))?,
    ))
}

fn graphic_layer(node: &konnect_sexp::SexpNode, kind: &str) -> anyhow::Result<String> {
    node.find_str("layer")
        .map(str::to_string)
        .ok_or_else(|| anyhow::anyhow!("footprint {kind} is missing its layer"))
}

/// Stroke width in mm: modern `(stroke (width w) …)`, legacy bare `(width w)`.
/// KiCad's default silkscreen line width stands in when neither is present.
fn graphic_stroke_width(node: &konnect_sexp::SexpNode) -> f64 {
    node.find("stroke")
        .and_then(|stroke| stroke.find_f64("width"))
        .or_else(|| node.find_f64("width"))
        .unwrap_or(0.12)
}

/// `(fill yes)` (KiCad 8+) or legacy `(fill solid)`.
fn graphic_filled(node: &konnect_sexp::SexpNode) -> bool {
    matches!(node.find_str("fill"), Some("yes") | Some("solid"))
}

/// `(hide yes)` (modern) or a bare `hide` atom (legacy).
fn text_hidden(node: &konnect_sexp::SexpNode) -> bool {
    node.find_str("hide") == Some("yes")
        || node
            .children()
            .unwrap_or_default()
            .iter()
            .any(|child| child.as_str() == Some("hide"))
}

/// `(effects (font (size h w)))` glyph size, defaulting to KiCad's 1 mm.
fn text_size(node: &konnect_sexp::SexpNode) -> f64 {
    node.find("effects")
        .and_then(|effects| effects.find("font"))
        .and_then(|font| font.find("size"))
        .and_then(|size| size.get_f64(1))
        .unwrap_or(1.0)
}

/// Text position and angle from `(at x y [rot])`.
fn text_at(node: &konnect_sexp::SexpNode, kind: &str) -> anyhow::Result<((f64, f64), f64)> {
    let at = node
        .find("at")
        .ok_or_else(|| anyhow::anyhow!("footprint {kind} is missing its position"))?;
    Ok((
        (
            at.get_f64(1)
                .ok_or_else(|| anyhow::anyhow!("footprint {kind} has an invalid X position"))?,
            at.get_f64(2)
                .ok_or_else(|| anyhow::anyhow!("footprint {kind} has an invalid Y position"))?,
        ),
        at.get_f64(3).unwrap_or(0.0),
    ))
}

/// Parse a footprint's drawable children — `fp_line`, `fp_rect`, `fp_circle`,
/// `fp_arc`, `fp_poly` and visible `fp_text`/`property` texts — into
/// footprint-local [`konnect_ipc::IpcGraphicDefinition`]s.
///
/// The typed placement path previously shipped pads only, so a placed part had
/// no courtyard, silkscreen, or fab drawing: courtyard DRC had nothing to
/// check and KiCad's `lib_footprint_mismatch` flagged every placement.
///
/// `Reference` and `Value` properties are excluded — `build_footprint_item`
/// already carries those as first-class fields.
/// Footprint-local Reference/Value text anchors from the library source, so
/// placed parts keep the library's text layout (a synthesized offset put the
/// Reference on the part's own silkscreen — silk_overlap in live DRC).
pub(crate) fn extract_field_placement(source: &str) -> konnect_ipc::IpcFieldPlacement {
    let mut placement = konnect_ipc::IpcFieldPlacement::default();
    let Ok(footprint) = konnect_sexp::parse_sexp(source) else {
        return placement;
    };
    for prop in footprint.find_all("property") {
        let Some(name) = prop.get(1).and_then(|n| n.as_str()) else {
            continue;
        };
        let Some(at) = prop.find("at") else {
            continue;
        };
        let num = |i: usize| {
            at.get(i)
                .and_then(|v| v.as_str())
                .and_then(|s| s.parse::<f64>().ok())
        };
        let (x, y) = (num(1), num(2));
        let rot = num(3).unwrap_or(0.0);
        if let (Some(x), Some(y)) = (x, y) {
            match name {
                "Reference" => placement.reference_at = Some((x, y, rot)),
                "Value" => placement.value_at = Some((x, y, rot)),
                _ => {}
            }
        }
    }
    placement
}

pub(crate) fn extract_graphic_definitions(
    source: &str,
) -> anyhow::Result<Vec<konnect_ipc::IpcGraphicDefinition>> {
    use konnect_ipc::IpcGraphicDefinition as Graphic;
    let footprint = konnect_sexp::parse_sexp(source)?;
    let mut graphics = Vec::new();

    for line in footprint.find_all("fp_line") {
        graphics.push(Graphic::Line {
            start: graphic_point(line, "start", "fp_line")?,
            end: graphic_point(line, "end", "fp_line")?,
            layer: graphic_layer(line, "fp_line")?,
            width: graphic_stroke_width(line),
        });
    }
    for rect in footprint.find_all("fp_rect") {
        graphics.push(Graphic::Rect {
            start: graphic_point(rect, "start", "fp_rect")?,
            end: graphic_point(rect, "end", "fp_rect")?,
            layer: graphic_layer(rect, "fp_rect")?,
            width: graphic_stroke_width(rect),
            filled: graphic_filled(rect),
        });
    }
    for circle in footprint.find_all("fp_circle") {
        graphics.push(Graphic::Circle {
            center: graphic_point(circle, "center", "fp_circle")?,
            end: graphic_point(circle, "end", "fp_circle")?,
            layer: graphic_layer(circle, "fp_circle")?,
            width: graphic_stroke_width(circle),
            filled: graphic_filled(circle),
        });
    }
    for arc in footprint.find_all("fp_arc") {
        graphics.push(Graphic::Arc {
            start: graphic_point(arc, "start", "fp_arc")?,
            mid: graphic_point(arc, "mid", "fp_arc")?,
            end: graphic_point(arc, "end", "fp_arc")?,
            layer: graphic_layer(arc, "fp_arc")?,
            width: graphic_stroke_width(arc),
        });
    }
    for poly in footprint.find_all("fp_poly") {
        let pts = poly
            .find("pts")
            .ok_or_else(|| anyhow::anyhow!("footprint fp_poly is missing its (pts …)"))?;
        let points = pts
            .children()
            .unwrap_or_default()
            .iter()
            .filter(|node| node.head() == Some("xy"))
            .map(|node| {
                Ok((
                    node.get_f64(1)
                        .ok_or_else(|| anyhow::anyhow!("footprint fp_poly has an invalid X"))?,
                    node.get_f64(2)
                        .ok_or_else(|| anyhow::anyhow!("footprint fp_poly has an invalid Y"))?,
                ))
            })
            .collect::<anyhow::Result<Vec<_>>>()?;
        graphics.push(Graphic::Poly {
            points,
            layer: graphic_layer(poly, "fp_poly")?,
            width: graphic_stroke_width(poly),
            filled: graphic_filled(poly),
        });
    }
    for text in footprint.find_all("fp_text") {
        if text_hidden(text) {
            continue;
        }
        let content = text
            .get(2)
            .and_then(konnect_sexp::SexpNode::as_str)
            .ok_or_else(|| anyhow::anyhow!("footprint fp_text is missing its text"))?;
        let (position, rotation) = text_at(text, "fp_text")?;
        graphics.push(Graphic::Text {
            text: content.to_string(),
            position,
            rotation,
            layer: graphic_layer(text, "fp_text")?,
            size: text_size(text),
        });
    }
    for property in footprint.find_all("property") {
        let name = property.get(1).and_then(konnect_sexp::SexpNode::as_str);
        // Reference and Value travel as first-class fields; hidden built-ins
        // (Footprint, Datasheet, …) are not drawn.
        if matches!(name, Some("Reference") | Some("Value")) || text_hidden(property) {
            continue;
        }
        let Some(content) = property.get(2).and_then(konnect_sexp::SexpNode::as_str) else {
            continue;
        };
        let Ok((position, rotation)) = text_at(property, "property") else {
            continue;
        };
        let Ok(layer) = graphic_layer(property, "property") else {
            continue;
        };
        graphics.push(Graphic::Text {
            text: content.to_string(),
            position,
            rotation,
            layer,
            size: text_size(property),
        });
    }
    Ok(graphics)
}

// ─── Library footprint → board footprint (file-editing fallback) ─────────────
//
// Used ONLY when the IPC transport is unreachable (unconfigured socket or
// failed dial/send): a live KiCad must never have the board file edited
// behind its back. Ported from emolitor's PR #66.

/// Build a board-ready `(footprint …)` block for `lib_id`.
///
/// A library `.kicad_mod` is a complete footprint definition sitting at the
/// origin with a `REF**` placeholder reference. Placing it on a board means
/// renaming it to the full `Library:Footprint` id, stamping in a position,
/// rotation and fresh UUID, and substituting the real reference designator.
///
/// KiCAD's own parser then handles the pads and graphics, which is why the
/// whole definition is forwarded rather than reconstructed.
/// Why a board-ready footprint block could not be built.
///
/// D.6.5: [`board_footprint_sexp`] answered `Result<String, String>`, and that
/// String bundled three unrelated failures — a reference that resolves to
/// nothing, a file that cannot be read, and a `.kicad_mod` that is not a
/// footprint. Two of the three have a catalogued kind that is true of them,
/// which is the whole reason to keep them apart this far up.
#[derive(Debug)]
enum BoardFootprintError {
    /// The reference did not resolve to a file.
    Resolve(FootprintPathError),
    /// The file resolved and could not be read.
    Read {
        path: std::path::PathBuf,
        source: std::io::Error,
    },
    /// The file was read and is not a footprint definition.
    Malformed { path: std::path::PathBuf },
}

impl BoardFootprintError {
    /// The catalogued kind for this failure.
    ///
    /// `Malformed` returned `None` when this type landed, because no kind was
    /// true of a `.kicad_mod` whose first block is not `(footprint "NAME" …)`.
    /// `MalformedDocument` (D77) is that kind — added once six sites across
    /// four files had converged on the shape, which is the bar a new kind has
    /// to clear.
    fn kind(&self) -> ToolErrorKind {
        match self {
            Self::Resolve(error) => error.kind(),
            Self::Read { source, .. } => ToolErrorKind::from_io(source),
            Self::Malformed { path } => ToolErrorKind::MalformedDocument {
                path: path.display().to_string(),
                detail: "does not start with a (footprint \"NAME\" …) block".to_string(),
            },
        }
    }
}

impl std::fmt::Display for BoardFootprintError {
    fn fmt(&self, formatter: &mut std::fmt::Formatter<'_>) -> std::fmt::Result {
        match self {
            Self::Resolve(error) => write!(formatter, "{error}"),
            Self::Read { path, source } => {
                write!(
                    formatter,
                    "Cannot read footprint {}: {}",
                    path.display(),
                    source
                )
            }
            Self::Malformed { path } => write!(
                formatter,
                "{} does not start with a (footprint \"NAME\" …) block",
                path.display()
            ),
        }
    }
}

impl std::error::Error for BoardFootprintError {}

fn board_footprint_sexp(
    lib_id: &str,
    x: f64,
    y: f64,
    rotation: f64,
    layer: &str,
    reference: Option<&str>,
    project_dir: Option<&Path>,
) -> Result<String, BoardFootprintError> {
    let path = resolve_footprint_path(lib_id, project_dir).map_err(BoardFootprintError::Resolve)?;
    let content = std::fs::read_to_string(&path).map_err(|source| BoardFootprintError::Read {
        path: path.clone(),
        source,
    })?;

    let name_span = footprint_name_span(&content)
        .ok_or_else(|| BoardFootprintError::Malformed { path: path.clone() })?;

    // Board footprints carry the full library id, not the bare footprint name.
    // The declared name is the span without its surrounding quotes.
    let declared = &content[name_span.start + 1..name_span.end - 1];
    let mut out = String::with_capacity(content.len() + 128);
    out.push_str(&content[..name_span.start]);
    out.push_str(&quote_sexp_string(&board_lib_id(lib_id, &path, declared)));
    out.push_str(&format!(
        "\n\t(at {x} {y} {rotation})\n\t(uuid \"{}\")",
        new_uuid()
    ));
    out.push_str(&content[name_span.end..]);

    if rotation != 0.0 {
        out = apply_rotation_to_children(&out, rotation);
    }
    if let Some(reference) = reference {
        out = replace_property_value(&out, "Reference", reference);
    }
    if layer != "F.Cu" {
        out = replace_footprint_layer(&out, layer);
    }

    Ok(out)
}

/// The name a board entry should carry for a footprint read from `path`.
///
/// `resolve_footprint_path` also accepts a bare filesystem path, which is
/// convenient for a caller holding a `.kicad_mod` directly. That path must not
/// reach the board file: `(footprint "C:\…\R_0805_2012Metric.kicad_mod")` is
/// not a library identifier, and KiCad reports the placed part as a broken
/// library link. This function is therefore total — every branch returns
/// something that is not a path.
///
/// Preference order, most authoritative first:
///
/// 1. The caller already gave a `Library:Footprint` id — use it verbatim.
/// 2. The fp-lib-table maps a nickname to the containing directory. Only the
///    table can answer this: KiCad lets any nickname point at any path, so
///    `MyParts` may well live in `vendor.pretty`, and guessing from the
///    directory would silently mislink the part.
/// 3. The conventional `<nickname>.pretty/` layout. The library is not
///    registered, so the link will be broken either way, but this is the
///    nickname the user gets when they do register it.
/// 4. Neither — fall back to a bare footprint name, which links to nothing but
///    is at least a valid name. The library file's own is used when it is not
///    itself path-like; otherwise the file stem, which cannot contain a
///    separator.
fn board_lib_id(reference: &str, path: &Path, declared: &str) -> String {
    if is_lib_id(reference) {
        return reference.to_string();
    }
    let stem = path
        .file_stem()
        .map(|s| s.to_string_lossy().into_owned())
        .unwrap_or_default();

    if let Some(dir) = path.parent() {
        if let Some(nick) = footprint_lib_nickname_for_dir(dir) {
            return format!("{nick}:{stem}");
        }
        if let Some(nick) = pretty_dir_nickname(dir) {
            return format!("{nick}:{stem}");
        }
    }

    if declared.is_empty() || declared.contains('/') || declared.contains('\\') {
        stem
    } else {
        declared.to_string()
    }
}

/// The nickname a conventional `<nickname>.pretty` directory implies.
///
/// Matched case-insensitively: KiCad's own libraries are lowercase `.pretty`,
/// but Windows and macOS filesystems are case-insensitive, so a `.Pretty` on
/// disk is the same directory to KiCad and should not change the answer.
fn pretty_dir_nickname(dir: &Path) -> Option<String> {
    let name = dir.file_name()?.to_string_lossy().into_owned();
    let cut = name.len().checked_sub(".pretty".len())?;
    name[cut..]
        .eq_ignore_ascii_case(".pretty")
        .then(|| name[..cut].to_string())
        .filter(|nick| !nick.is_empty())
}

/// Fold the footprint's placement rotation into its pads and text items.
///
/// KiCad stores each pad's and text item's *absolute* orientation while their
/// positions stay in unrotated footprint-local coordinates — a `C_0603` placed
/// at -90° keeps `(at -0.775 0 270)` on pad 1. Omitting this leaves the pad
/// shapes unrotated relative to the body and makes KiCad's
/// `lib_footprint_mismatch` check fire.
///
/// Text is additionally kept readable: KiCad flips an angle that would leave a
/// label upside down by 180°, so a -90° footprint carries `90` on its reference.
fn apply_rotation_to_children(content: &str, rotation: f64) -> String {
    let mut out = content.to_string();

    for tag in ["pad", "property", "fp_text"] {
        let readable = tag != "pad";
        // Rewrite back-to-front so earlier byte offsets stay valid.
        let starts: Vec<usize> = find_block_starts(&out, tag);
        for start in starts.into_iter().rev() {
            let Some((bstart, bend)) = find_balanced_block(&out, start) else {
                continue;
            };
            // The block's own `(at …)` is its first — nested ones (a pad's
            // `(primitives …)`, for instance) come later.
            let Some(at_start) = find_block_starts(&out[bstart..bend], "at")
                .first()
                .map(|i| bstart + i)
            else {
                continue;
            };
            let Some((astart, aend)) = find_balanced_block(&out, at_start) else {
                continue;
            };
            let Some(rewritten) = rotate_at_block(&out[astart..aend], rotation, readable) else {
                continue;
            };
            out.replace_range(astart..aend, &rewritten);
        }
    }
    out
}

/// Rewrite `(at x y [angle])`, adding `rotation` to the angle.
///
/// Returns `None` when the block does not look like a positional `at`.
fn rotate_at_block(block: &str, rotation: f64, readable: bool) -> Option<String> {
    let inner = block.strip_prefix('(')?.strip_suffix(')')?;
    let mut parts = inner.split_whitespace();
    if parts.next()? != "at" {
        return None;
    }
    let x: f64 = parts.next()?.parse().ok()?;
    let y: f64 = parts.next()?.parse().ok()?;
    let existing: f64 = parts.next().and_then(|a| a.parse().ok()).unwrap_or(0.0);
    if parts.next().is_some() {
        return None; // `(at …)` with unexpected extra tokens — leave alone.
    }

    let mut angle = (existing + rotation).rem_euclid(360.0);
    if readable && angle > 90.0 && angle <= 270.0 {
        angle -= 180.0;
    }
    Some(format_at(x, y, angle))
}

/// Render `(at x y angle)`, dropping a zero angle as KiCad's writer does and
/// trimming trailing zeros from the decimals.
fn format_at(x: f64, y: f64, angle: f64) -> String {
    let n = |v: f64| {
        let s = format!("{v:.6}");
        let s = s.trim_end_matches('0').trim_end_matches('.').to_string();
        if s == "-0" {
            "0".to_string()
        } else {
            s
        }
    };
    if angle == 0.0 {
        format!("(at {} {})", n(x), n(y))
    } else {
        format!("(at {} {} {})", n(x), n(y), n(angle))
    }
}

/// Byte range of the quoted name in the leading `(footprint "NAME"` header,
/// including the surrounding quotes.
fn footprint_name_span(content: &str) -> Option<std::ops::Range<usize>> {
    let block = *find_block_starts(content, "footprint").first()?;
    let after_tag = block + "(footprint".len();
    let rel = content[after_tag..].find('"')?;
    let start = after_tag + rel;
    let end = start + 1 + content[start + 1..].find('"')?;
    Some(start..end + 1)
}
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
